intechstudio/grid-hardware/Packaging/PACKAGING-SLEEVE_Diecut.pdf

### Horizontal Grain

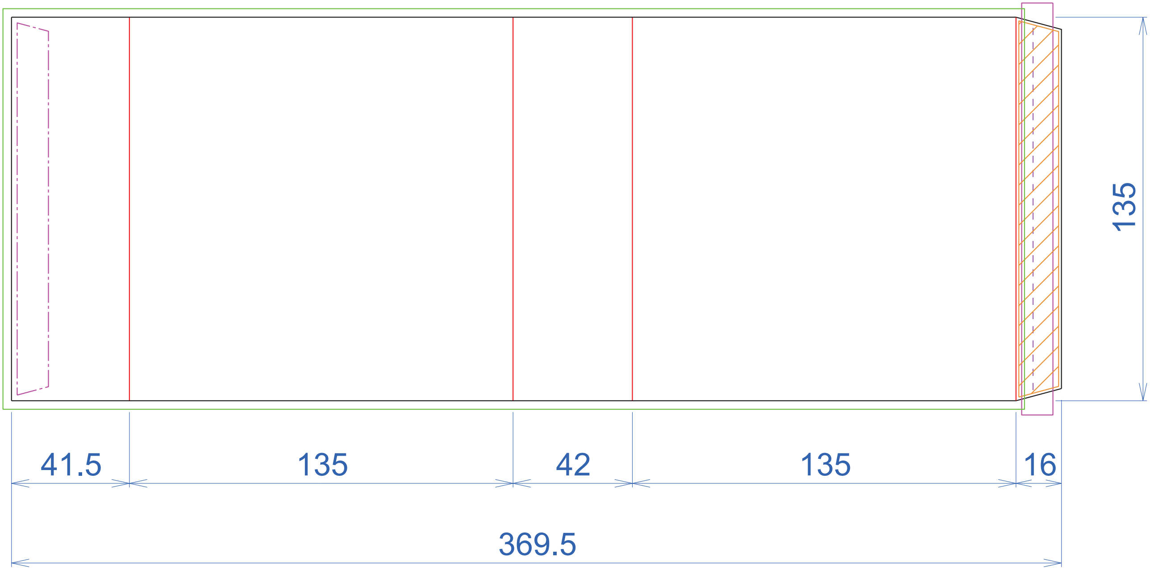
[picture p28: figure]
