intechstudio/grid-hardware/Electrical/failed to add usb.png

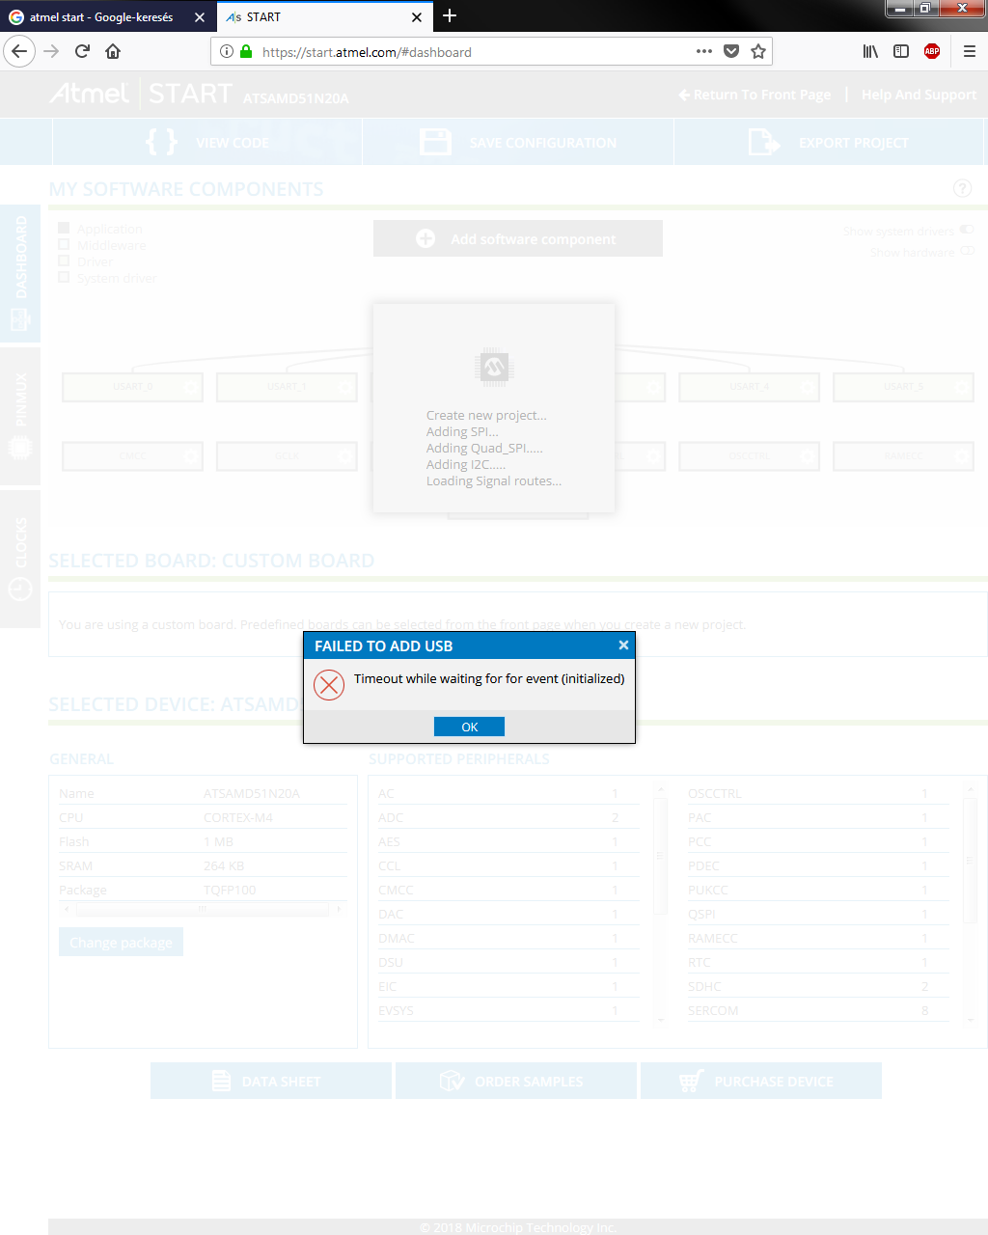
Electrical/failed to add usb.png
