intechstudio/grid-hardware/Electrical/Knowledge/4layer-stackup.jpg

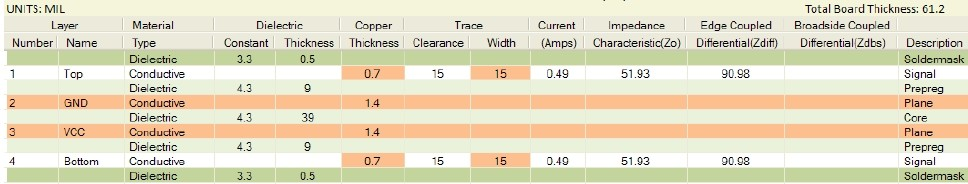
Electrical/Knowledge/4layer-stackup.jpg
