intechstudio/grid-hardware/Electrical/Knowledge/JLC_Stackup.PNG

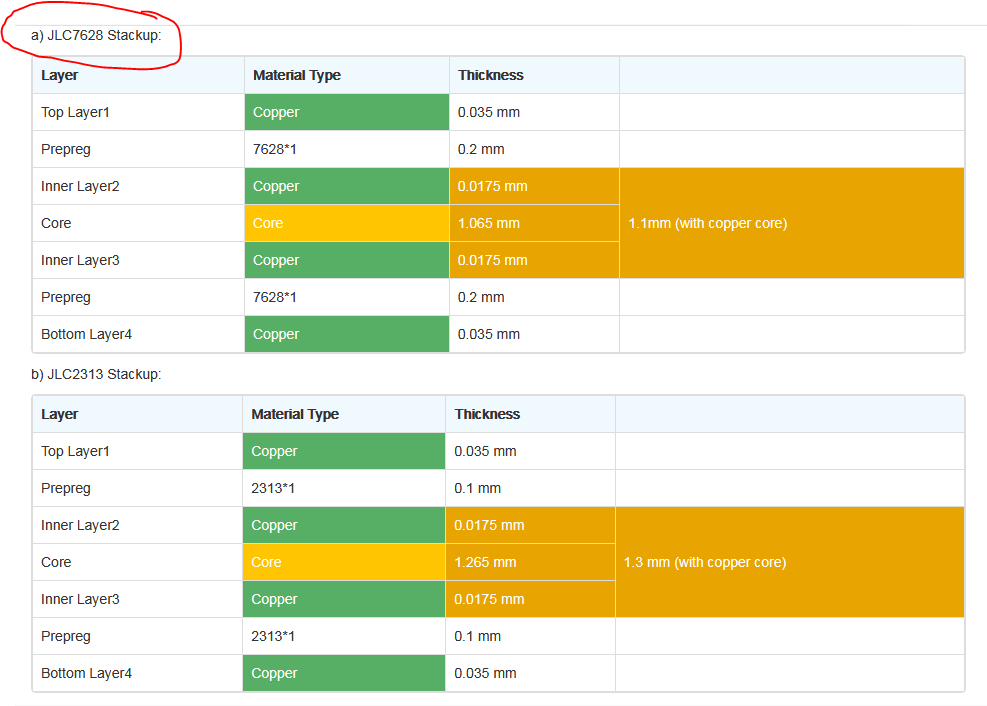
Electrical/Knowledge/JLC_Stackup.PNG
