intechstudio/grid-hardware/Electrical/Knowledge/New Stackup, JLC and WAY.PNG

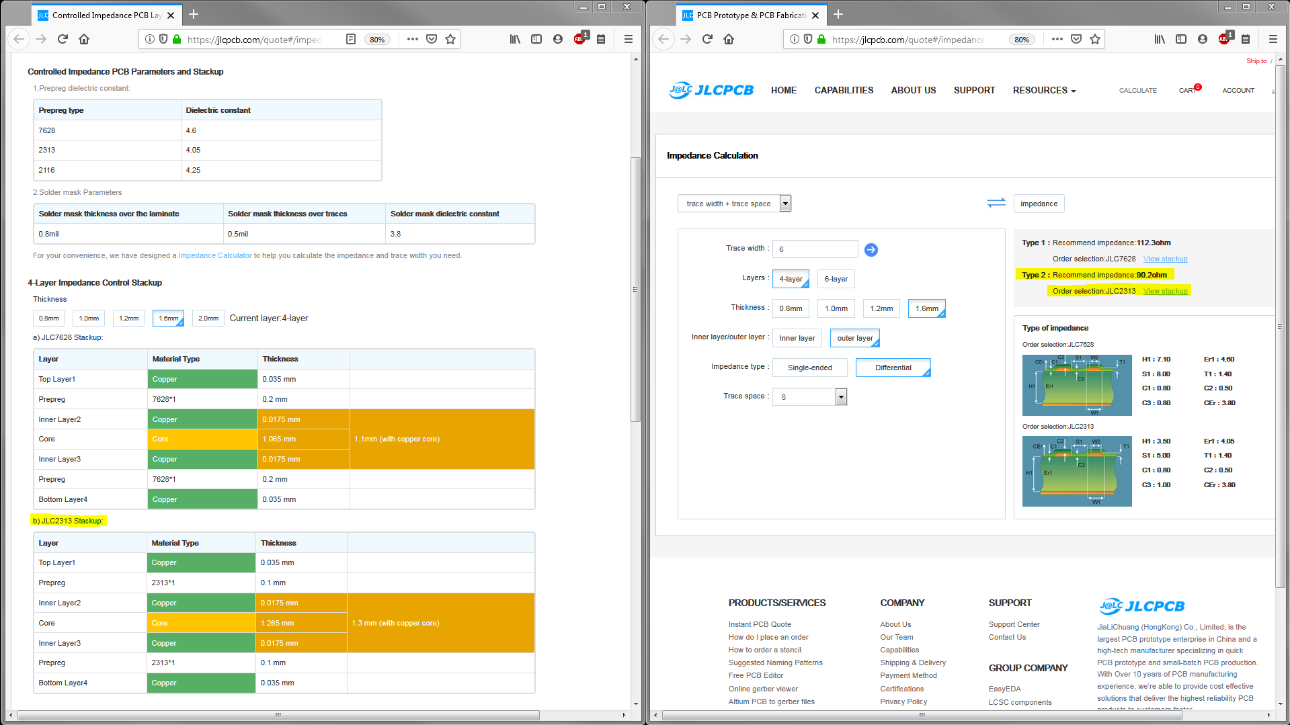
Electrical/Knowledge/New Stackup, JLC and WAY.PNG
