intechstudio/grid-hardware/Electrical/Knowledge/zdiff.png

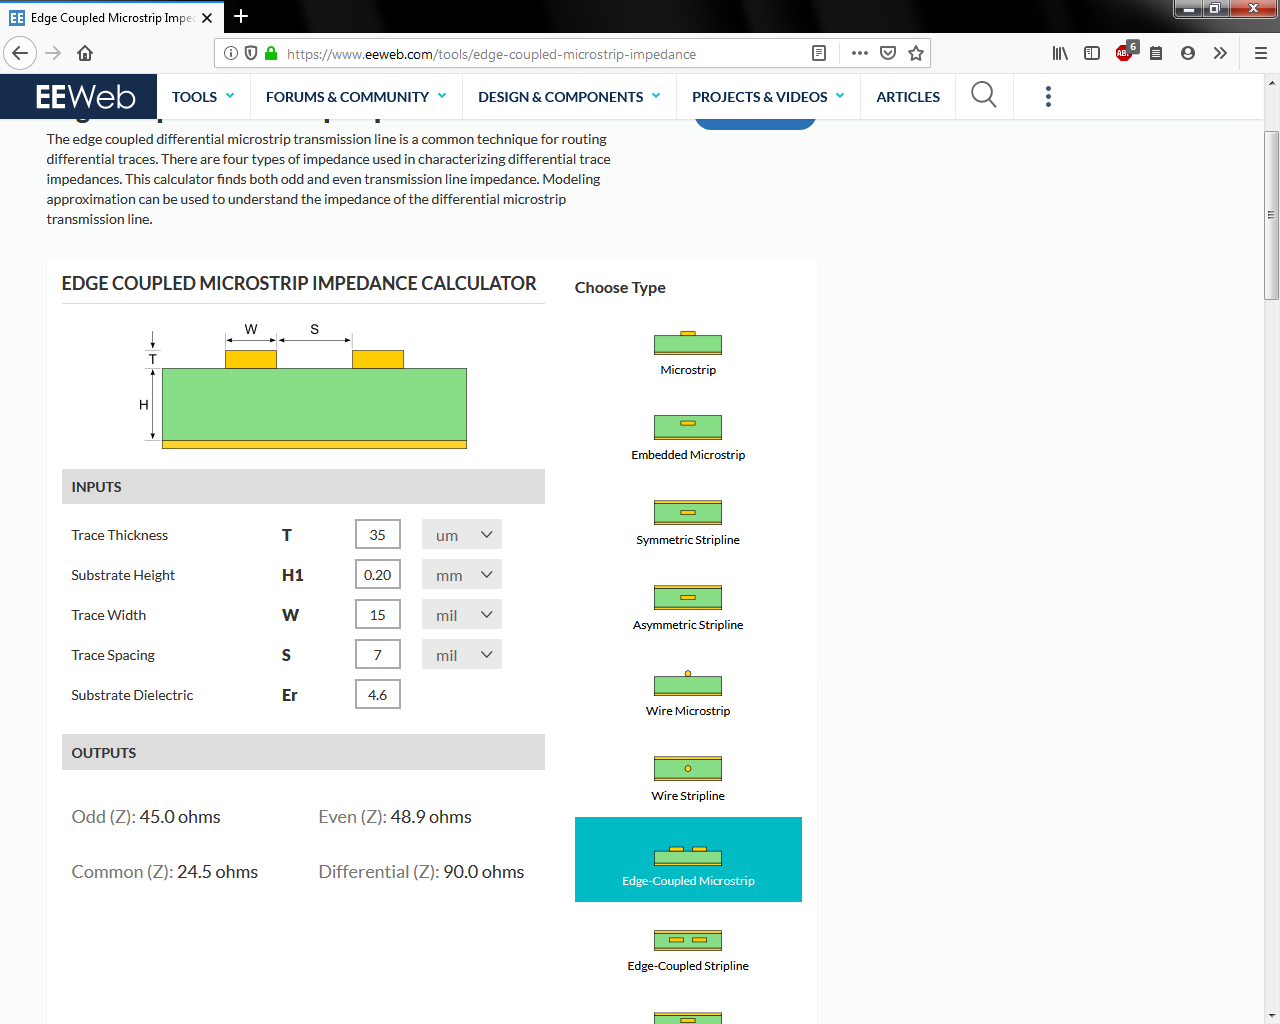
Electrical/Knowledge/zdiff.png
