intechstudio/grid-hardware/Electrical/rf_matching.png

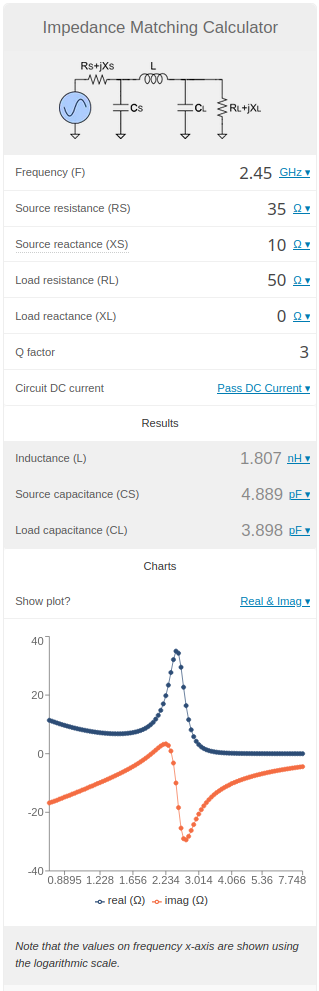
Electrical/rf_matching.png
