intechstudio/grid-hardware/Mechanical/Design/Pogo/Custom IS_POGO_Rev2_Latest/updated pogo.png

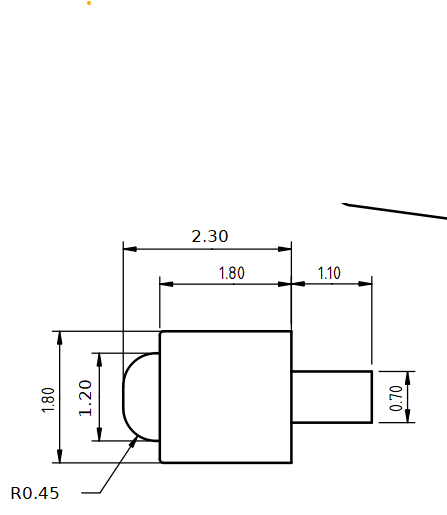
Mechanical/Design/Pogo/Custom IS_POGO_Rev2_Latest/updated pogo.png
