intechstudio/grid-hardware/Mechanical/Design/SMT-CONN-BATTERY/SMT-CONN-BATTERY_Photo.png

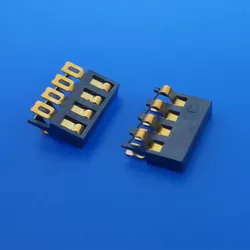
Mechanical/Design/SMT-CONN-BATTERY/SMT-CONN-BATTERY_Photo.png
