intechstudio/grid-hardware/Packaging/PACKAGING-SLEEVE-BU16.png

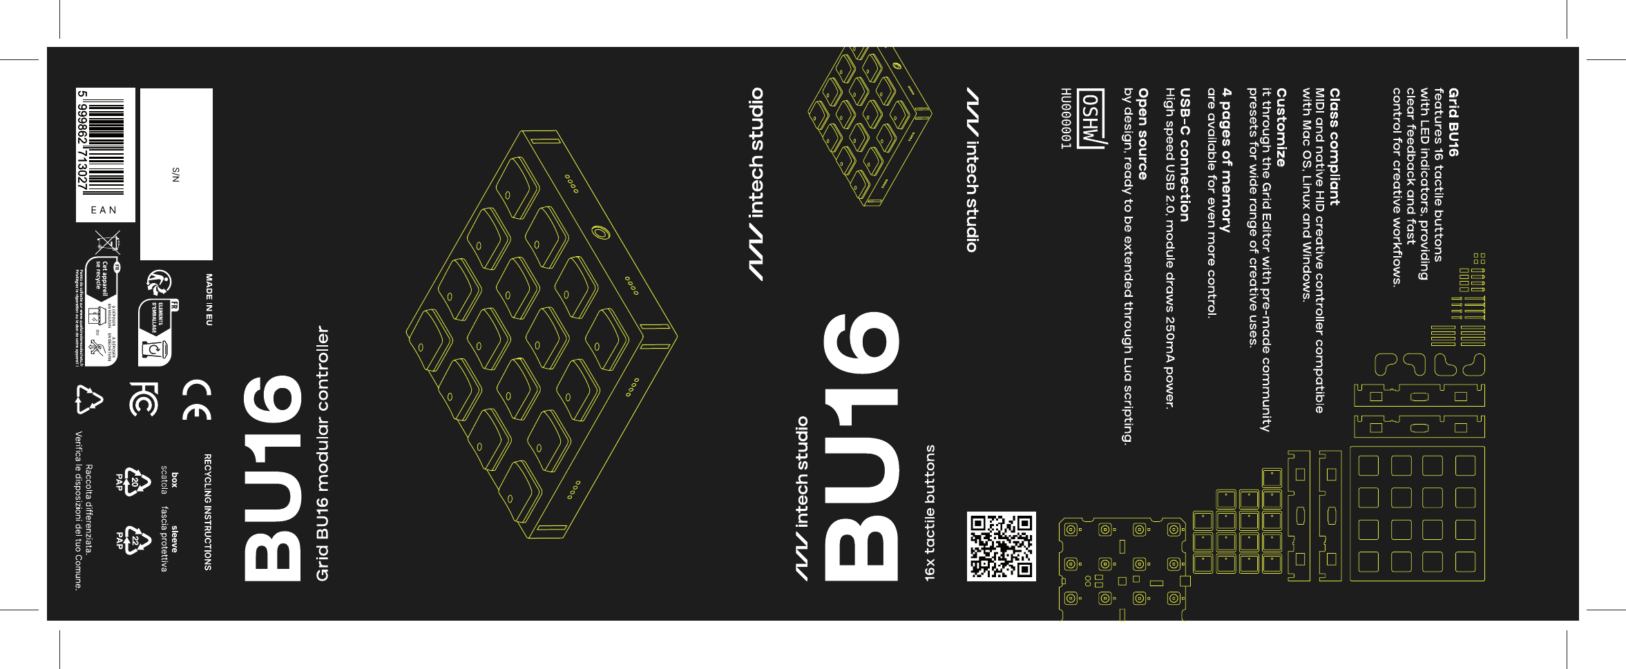
Packaging/PACKAGING-SLEEVE-BU16.png
