intechstudio/grid-hardware/Packaging/PACKAGING-SLEEVE-PBF4.png

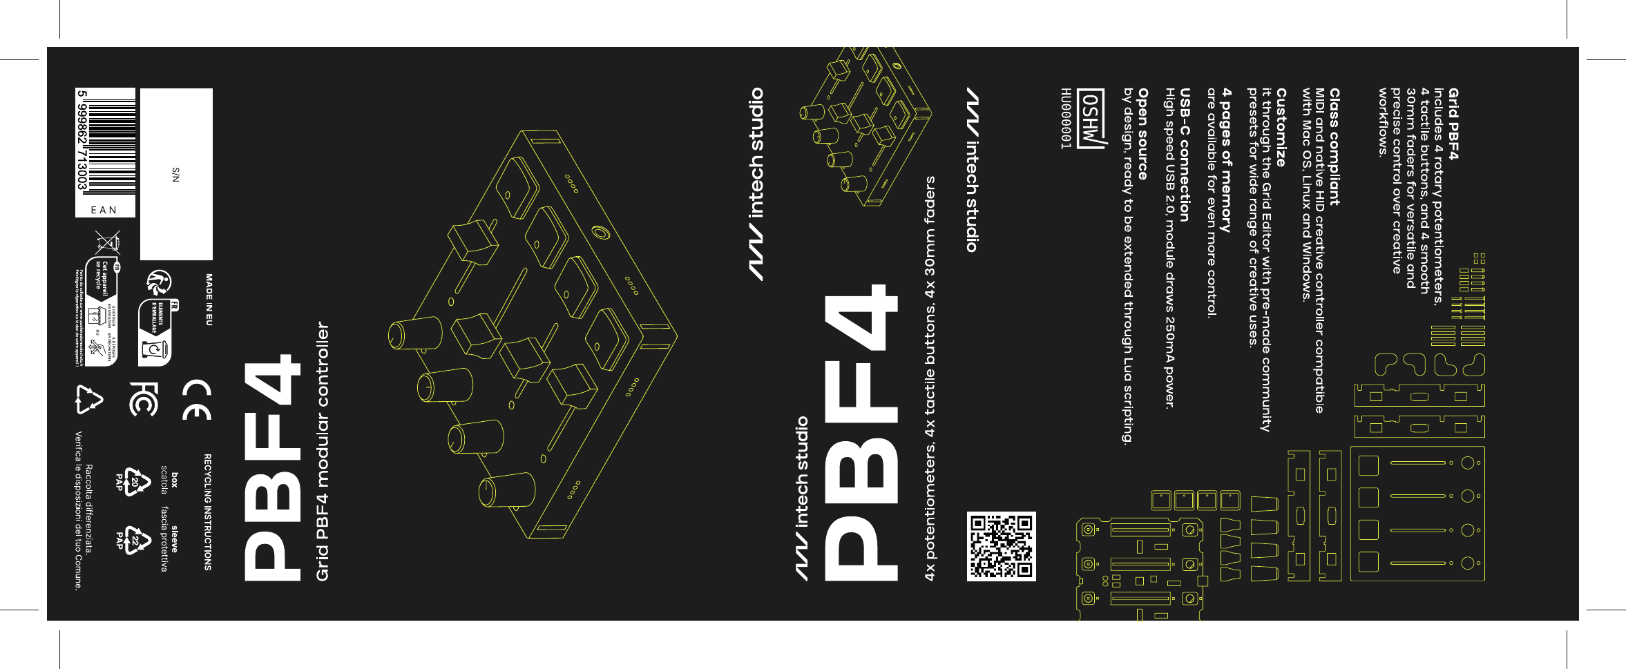
Packaging/PACKAGING-SLEEVE-PBF4.png
