intechstudio/grid-hardware/Packaging/PACKAGING-SLEEVE-PO16.png

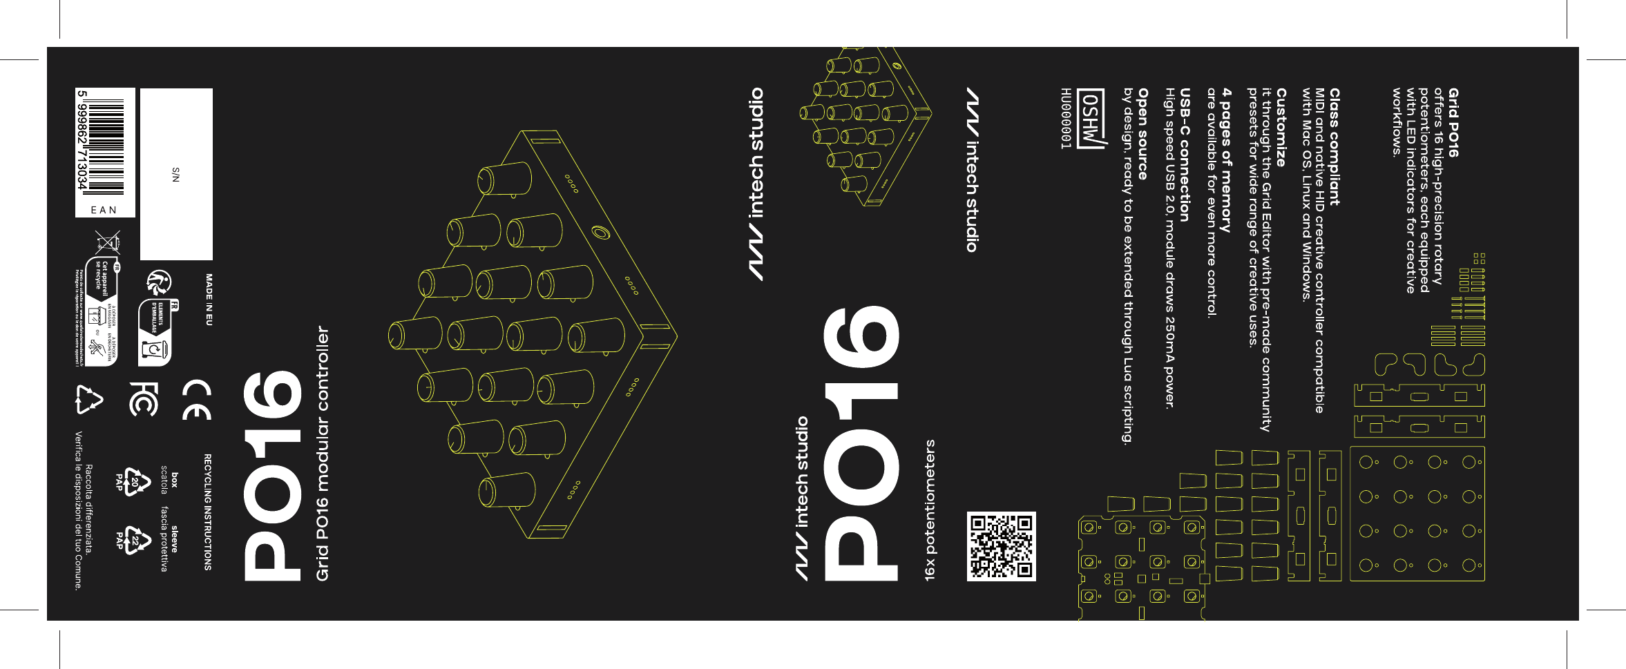
Packaging/PACKAGING-SLEEVE-PO16.png
