intechstudio/grid-hardware/Packaging/PACKAGING-SLEEVE-VSN1-L.png

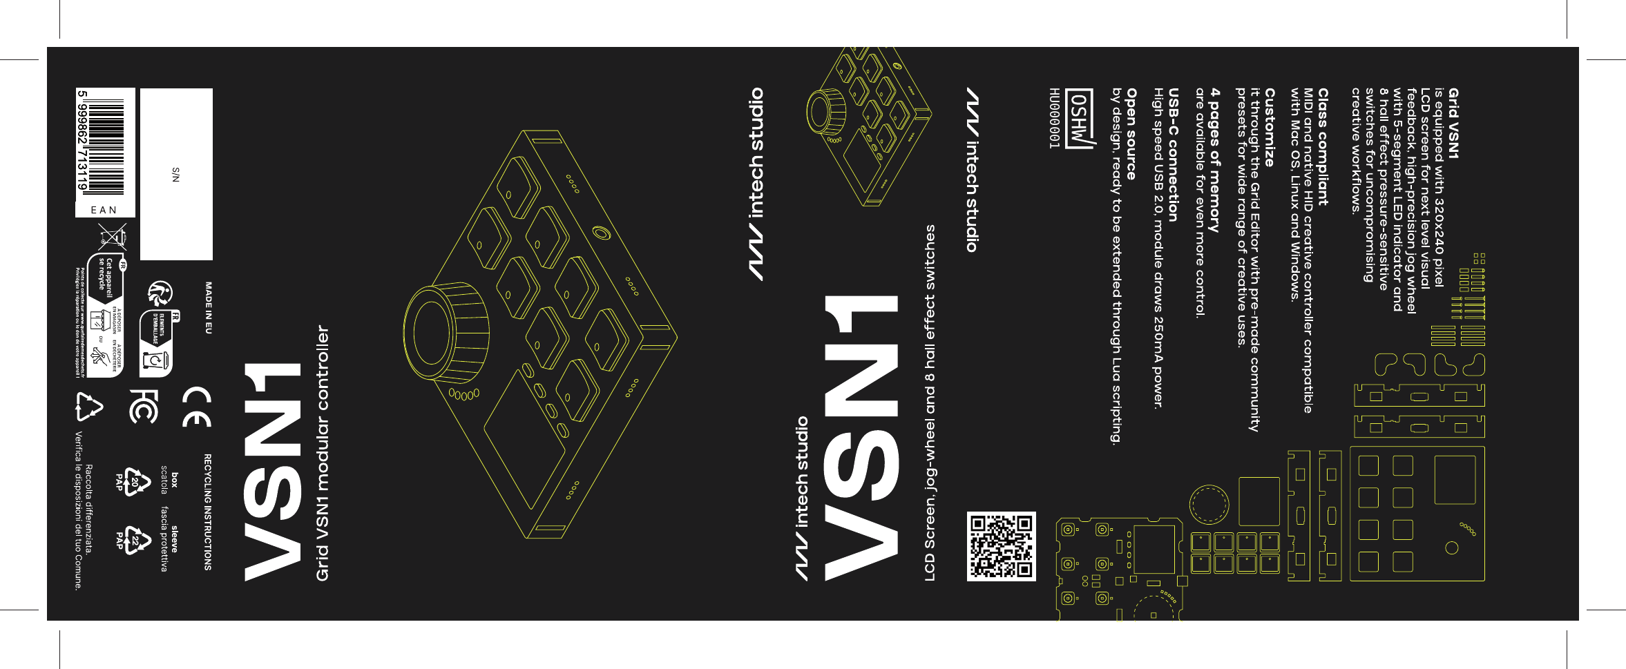
Packaging/PACKAGING-SLEEVE-VSN1-L.png
