intechstudio/grid-hardware/Packaging/PACKAGING-SLEEVE_Diecut.png

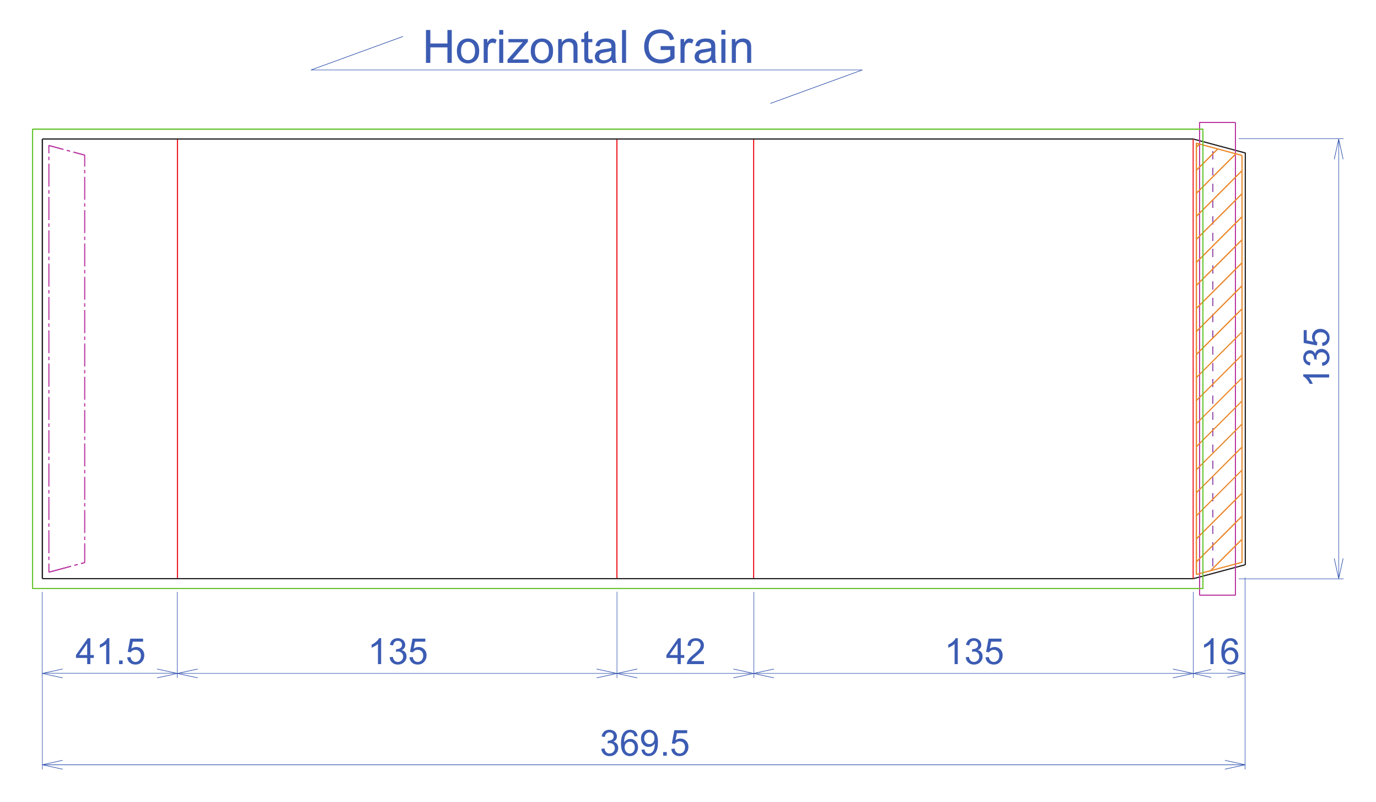
Packaging/PACKAGING-SLEEVE_Diecut.png
