intechstudio/grid-hardware/Packaging/PACKAGING-USB-CABLE.png

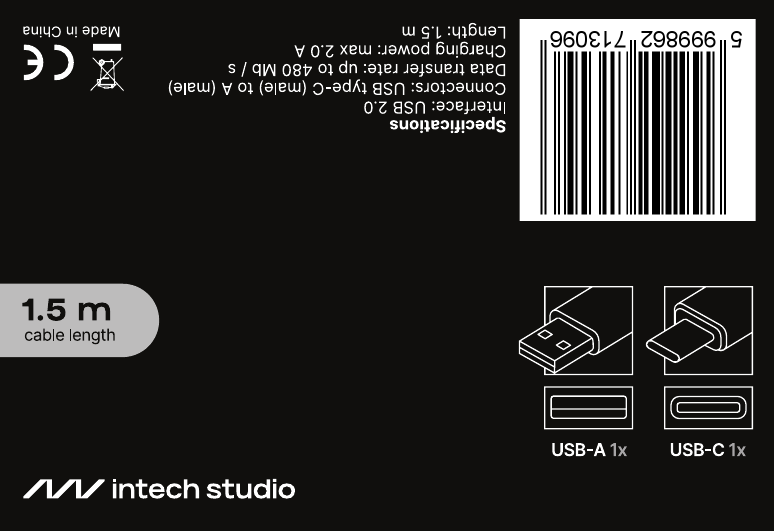
Packaging/PACKAGING-USB-CABLE.png
