intechstudio/grid-hardware/Electrical/Bill Of Materials/Photos/motherboard.jpg

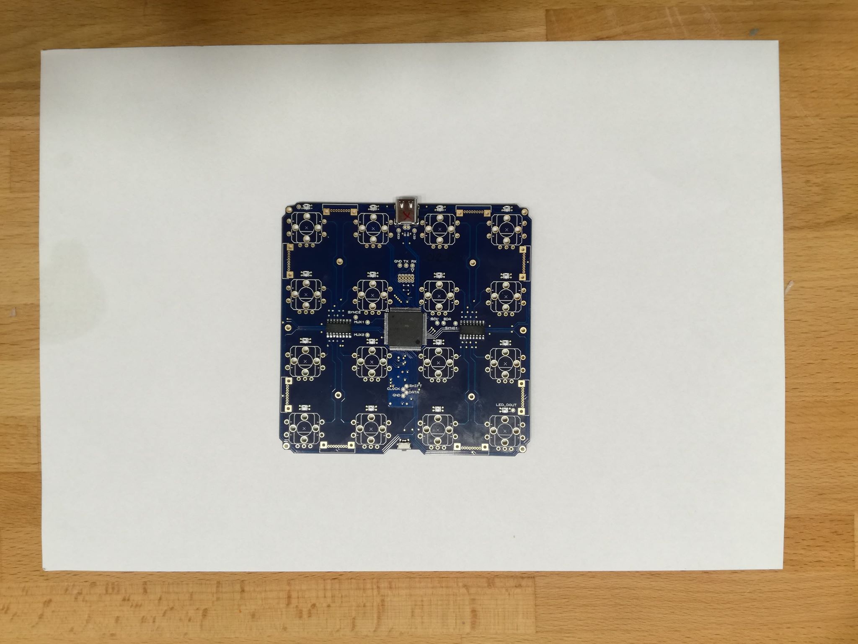
Electrical/Bill Of Materials/Photos/motherboard.jpg
