intechstudio/grid-hardware/Electrical/Bill Of Materials/Photos/product.jpg

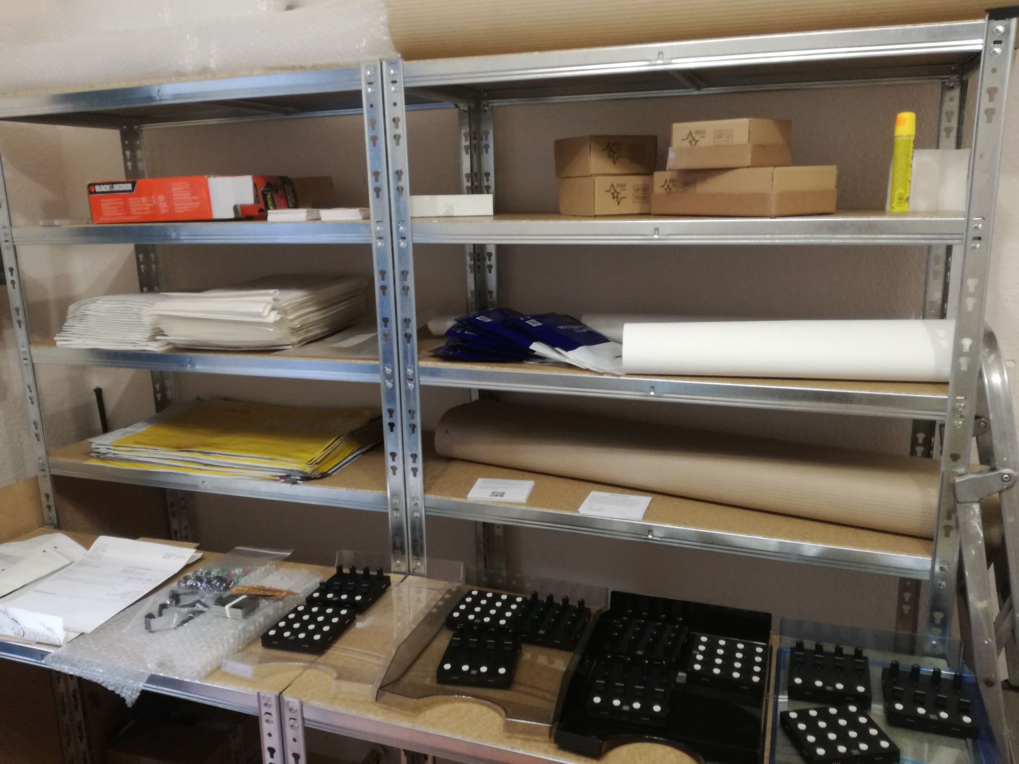
Electrical/Bill Of Materials/Photos/product.jpg
