intechstudio/grid-hardware/Manufacturing/Assembly/pot_cap_alignment_jig.FCStd

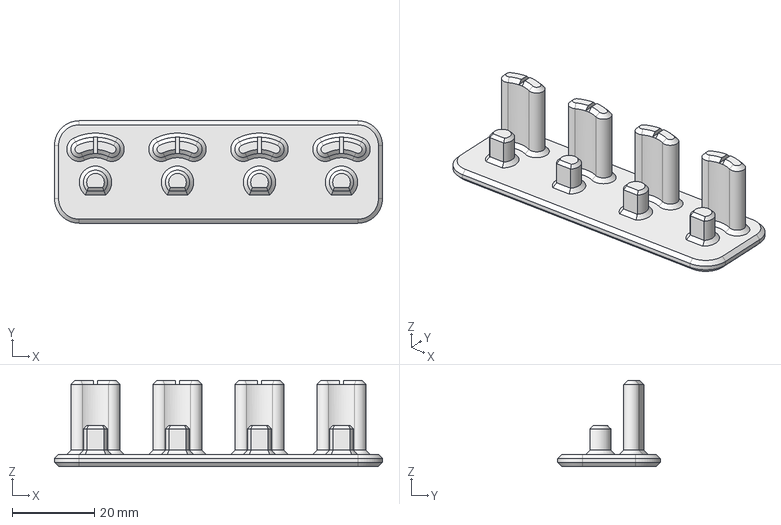
[picture p64: CAD file, 2020-11-19]
Manufacturing/Assembly/pot_cap_alignment_jig.FCStd
80.0 x 25.0 x 21.0 mm
