intechstudio/grid-hardware/Manufacturing/CarryCase/foam_insert.FCStd

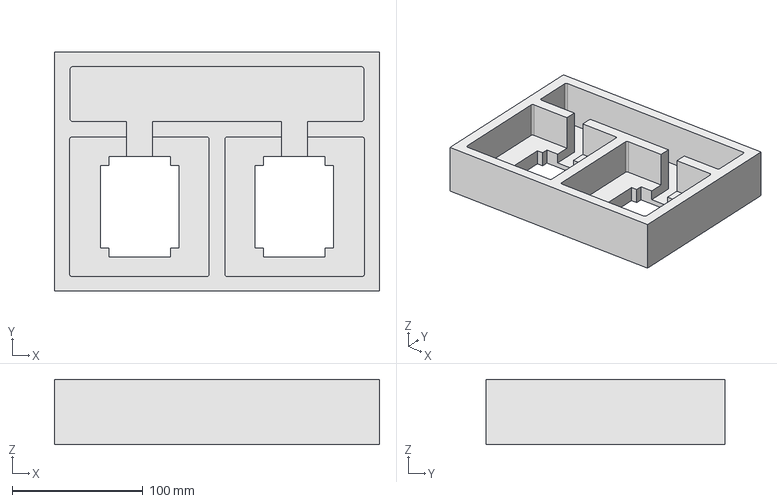
[picture p65: CAD file, 2023-02-24]
Manufacturing/CarryCase/foam_insert.FCStd
249.0 x 183.0 x 50.0 mm
