intechstudio/grid-hardware/Manufacturing/CNC/Electronics/cnc_endstop_mount_2.stl

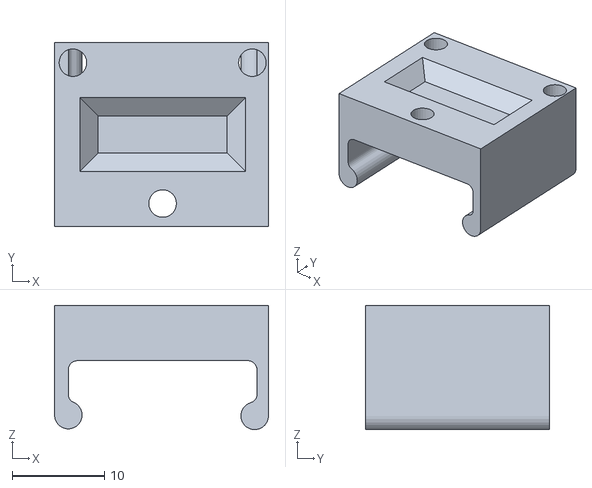
[picture p66: CAD file, 2021-02-25]
Manufacturing/CNC/Electronics/cnc_endstop_mount_2.stl
23.2 x 20.0 x 13.5
