intechstudio/grid-hardware/Manufacturing/CNC/vacuum_hole_fitting.FCStd

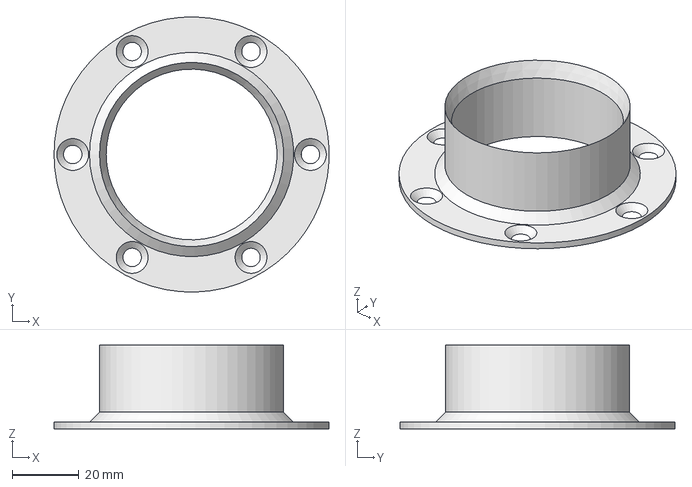
[picture p67: CAD file, 2021-04-12]
Manufacturing/CNC/vacuum_hole_fitting.FCStd
82.1 x 82.2 x 25.0 mm
