intechstudio/grid-hardware/Manufacturing/CNC_tristep/grid_cnc6.FCStd

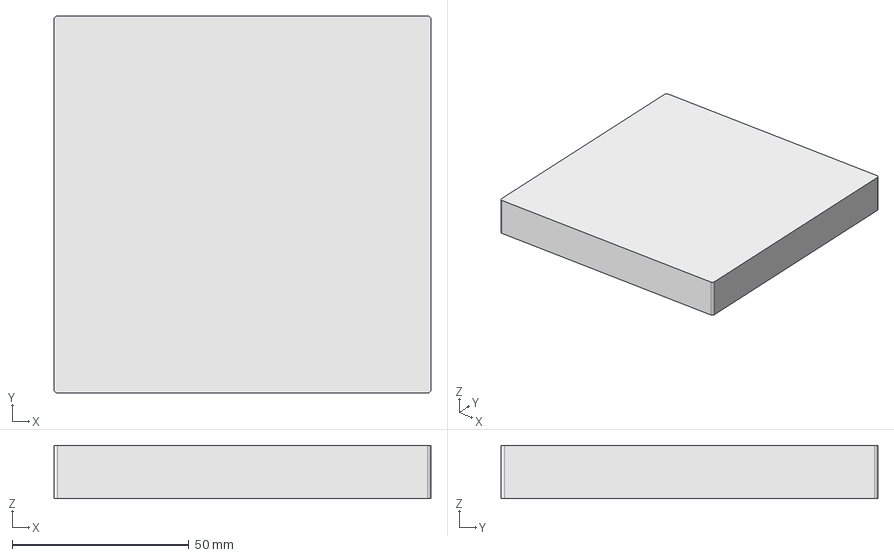
[picture p68: CAD file, 2023-06-28]
Manufacturing/CNC_tristep/grid_cnc6.FCStd
106.6 x 106.6 x 15.0 mm
