intechstudio/grid-hardware/Manufacturing/flatness_QC_jig/qc_jig_button_box.FCStd

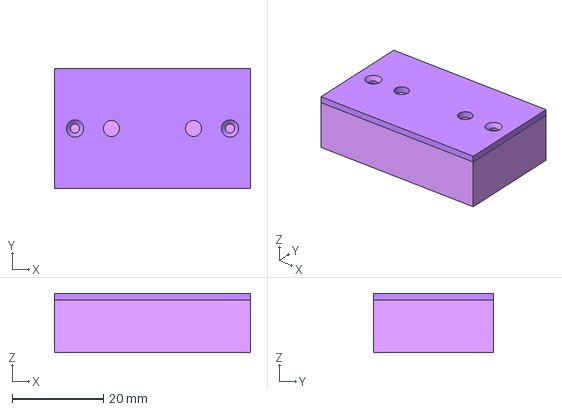
[picture p69: CAD file, 2024-06-20]
Manufacturing/flatness_QC_jig/qc_jig_button_box.FCStd
43.0 x 26.3 x 13.0 mm
