intechstudio/grid-hardware/Manufacturing/Fumefood/accessories/motormount.FCStd

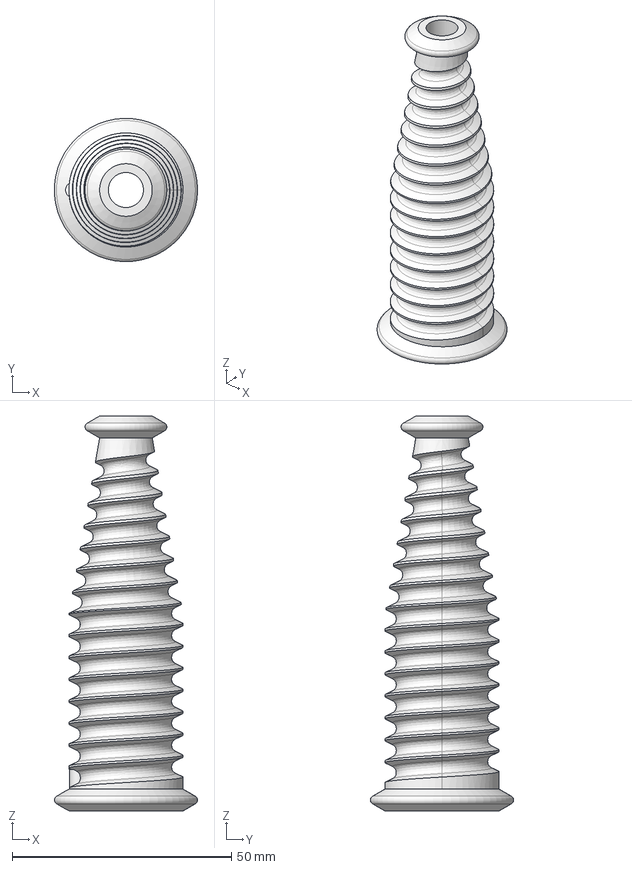
[picture p70: CAD file, 2021-10-26]
Manufacturing/Fumefood/accessories/motormount.FCStd
32.6 x 32.6 x 90.0 mm
