intechstudio/grid-hardware/Manufacturing/Fumefood/compliant_wheel.FCStd

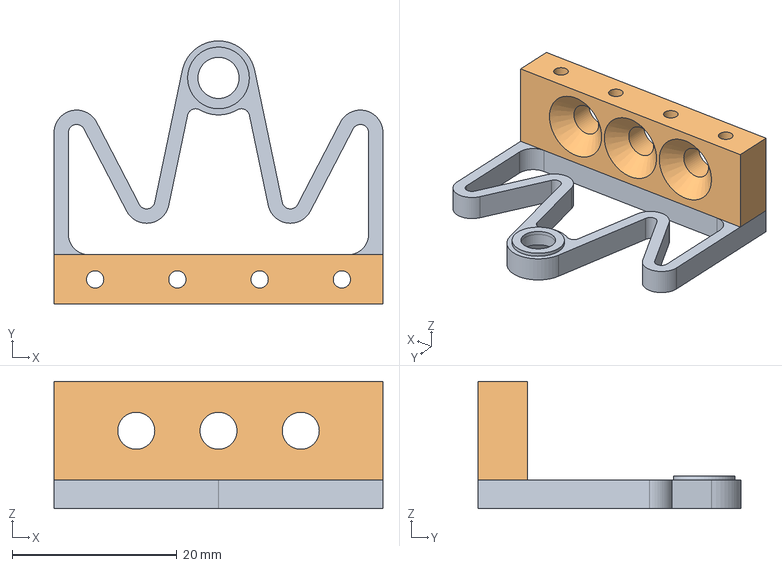
[picture p71: CAD file, 2021-03-19]
Manufacturing/Fumefood/compliant_wheel.FCStd
40.0 x 32.0 x 15.5 mm
