intechstudio/grid-hardware/Manufacturing/Fumefood/window_controls/2020_2x22mm_left.FCStd

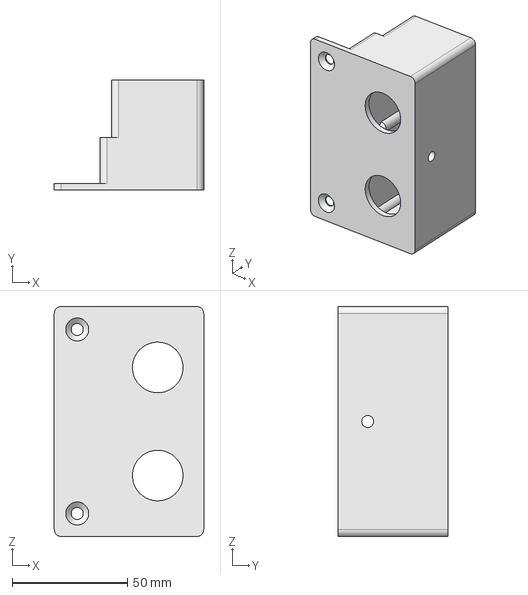
[picture p72: CAD file, 2021-09-23]
Manufacturing/Fumefood/window_controls/2020_2x22mm_left.FCStd
65.0 x 48.0 x 100.0 mm
