intechstudio/grid-hardware/Manufacturing/iroda/asztallab_szorito.FCStd

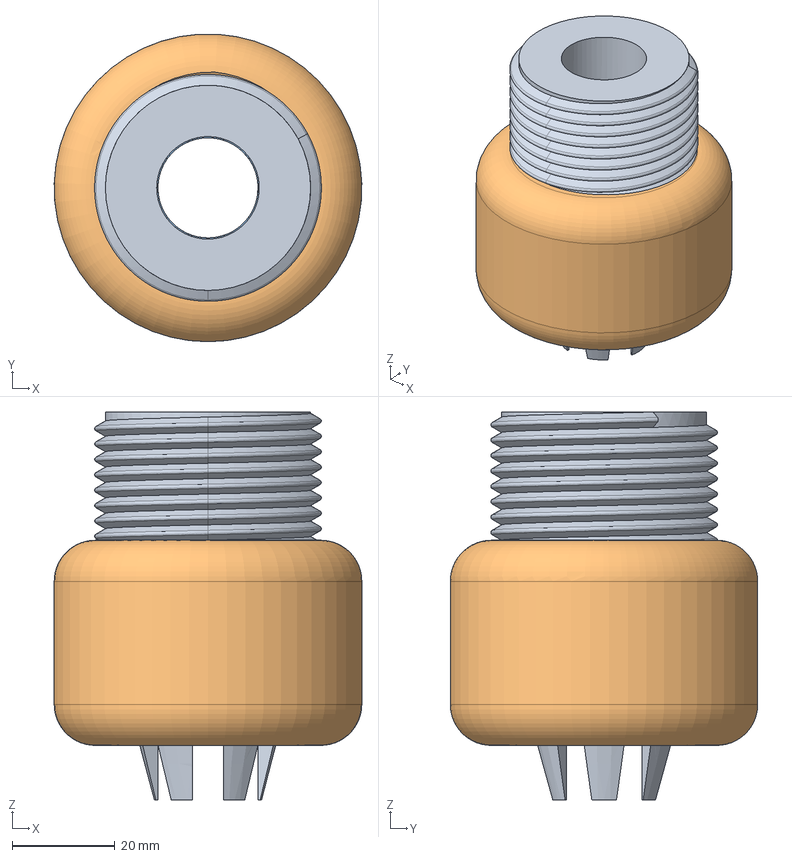
[picture p73: CAD file, 2024-03-14]
Manufacturing/iroda/asztallab_szorito.FCStd
60.0 x 59.9 x 75.6 mm
felso resz
szorito
hezagolo
