intechstudio/grid-hardware/Manufacturing/Laser/plotter_bearing_holder.FCStd

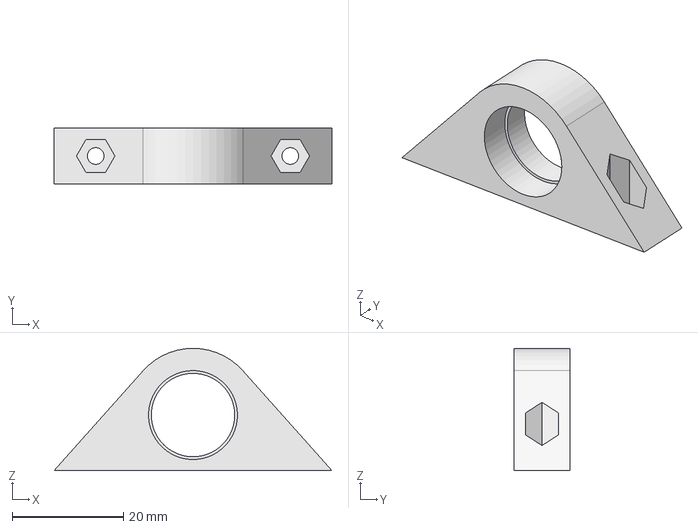
[picture p74: CAD file, 2021-02-25]
Manufacturing/Laser/plotter_bearing_holder.FCStd
50.0 x 10.0 x 22.0 mm
