intechstudio/grid-hardware/Manufacturing/Packaging/cardboard_insert.FCStd

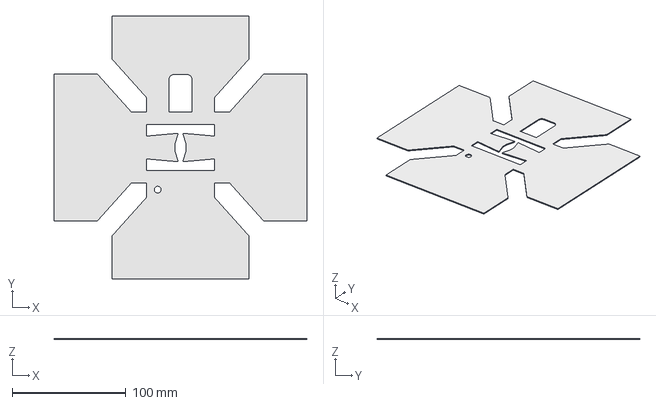
[picture p75: CAD file, 2023-03-27]
Manufacturing/Packaging/cardboard_insert.FCStd
222.0 x 231.0 x 1.00 mm
