intechstudio/grid-hardware/Manufacturing/Packaging/quote2/carboardinsert2.dxf

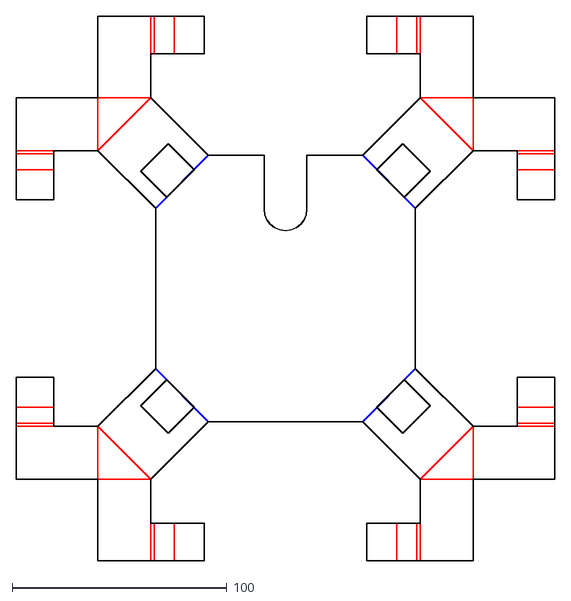
[picture p76: CAD file, 2020-11-30]
Manufacturing/Packaging/quote2/carboardinsert2.dxf
250.7 x 253.7
