intechstudio/grid-hardware/Manufacturing/Packaging/quote3/insert3.dxf

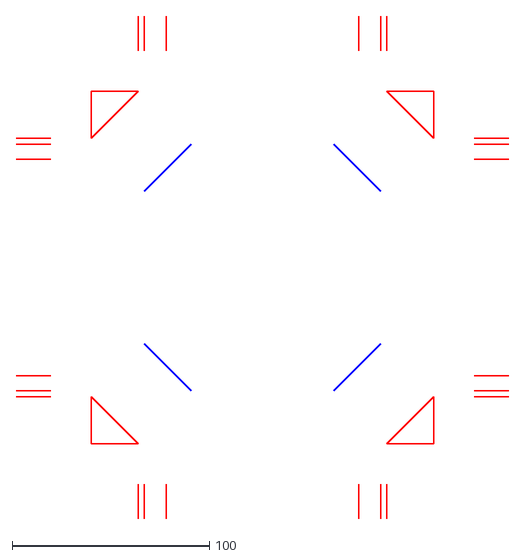
[picture p77: CAD file, 2020-12-07]
Manufacturing/Packaging/quote3/insert3.dxf
249.7 x 254.7
