intechstudio/grid-hardware/Manufacturing/Photobooth/gridstand_20deg.FCStd

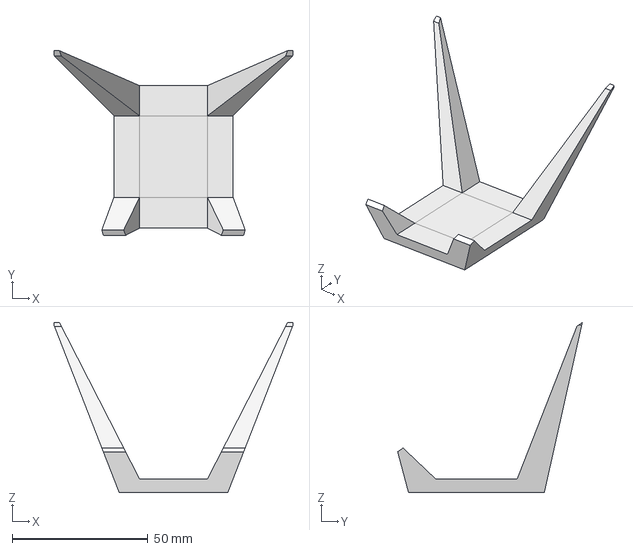
[picture p78: CAD file, 2021-02-25]
Manufacturing/Photobooth/gridstand_20deg.FCStd
88.0 x 68.0 x 62.6 mm
