intechstudio/grid-hardware/Manufacturing/Potbushing/pot_bushing.step

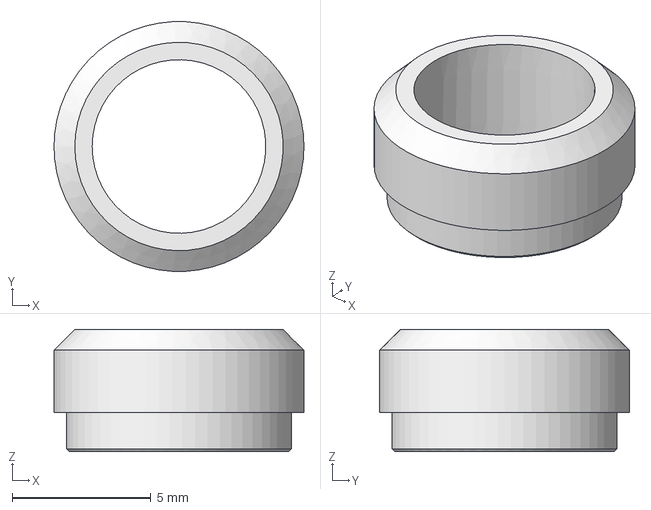
[picture p79: CAD file, 2021-09-28]
Manufacturing/Potbushing/pot_bushing.step
9.00 x 8.99 x 4.40 mm
