intechstudio/grid-hardware/Manufacturing/Potcap-insert/universal_insert.FCStd

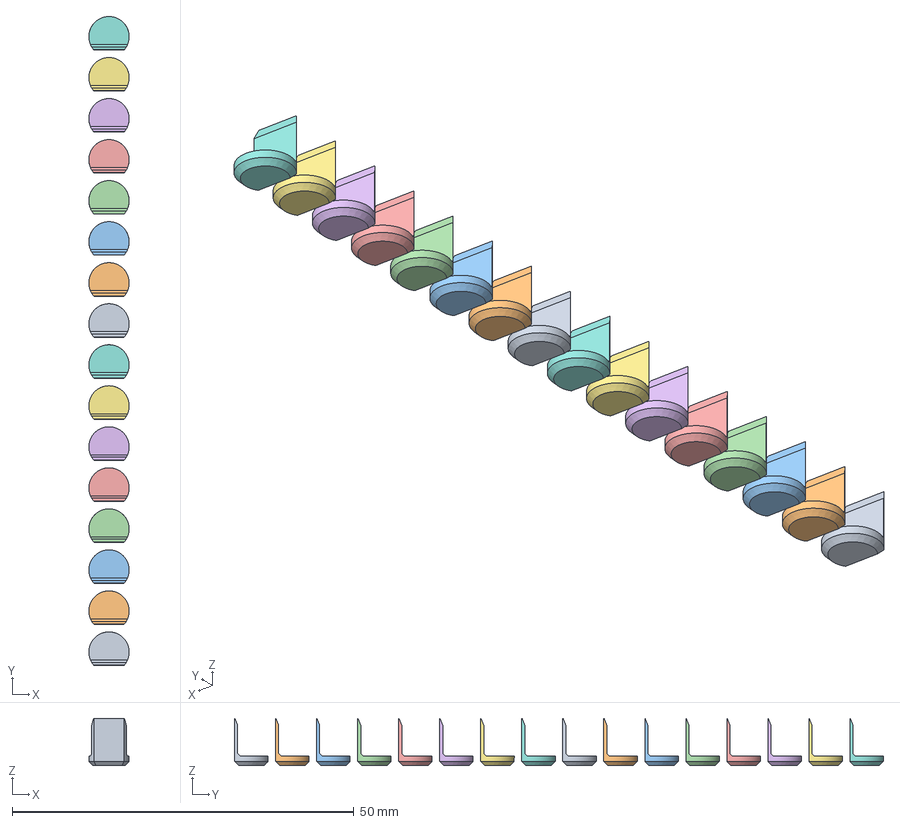
[picture p80: CAD file, 2024-07-18]
Manufacturing/Potcap-insert/universal_insert.FCStd
5.90 x 94.9 x 6.90 mm
Potentiometer001
