intechstudio/grid-hardware/Manufacturing/QC_jigs/pogo_pin_test_jig.FCStd

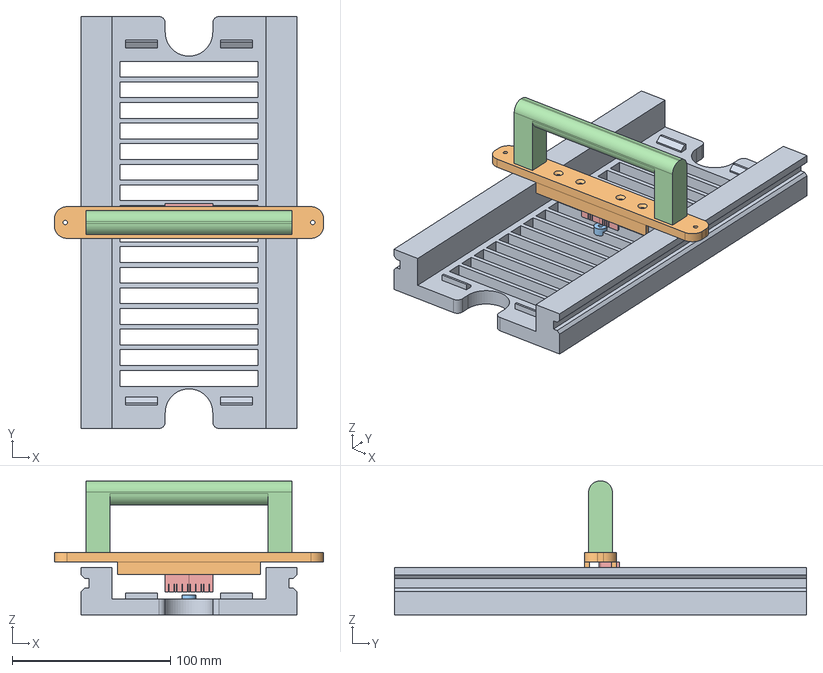
[picture p81: CAD file, 2024-03-14]
Manufacturing/QC_jigs/pogo_pin_test_jig.FCStd
170.0 x 260.0 x 84.5 mm
Jig
Handle sheet
Spacer
Handle
Comb
