intechstudio/grid-hardware/Mechanical/Assembly/Components/mapmode8.step

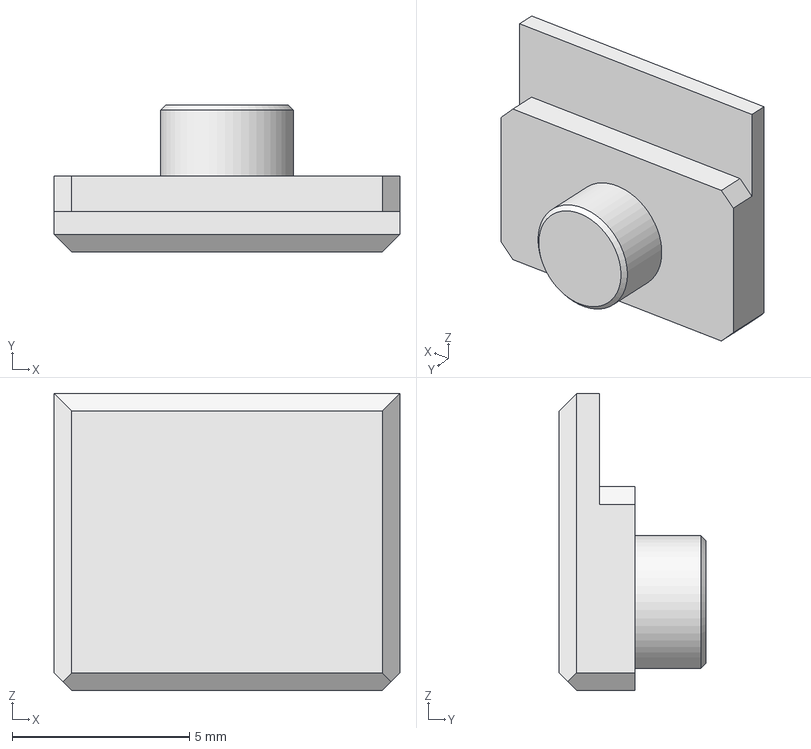
[picture p82: CAD file, 2020-07-10]
Mechanical/Assembly/Components/mapmode8.step
9.75 x 4.15 x 8.38 mm
