intechstudio/grid-hardware/Mechanical/Assembly/Frontpanels/FRONTPANEL-BU16-1.FCStd

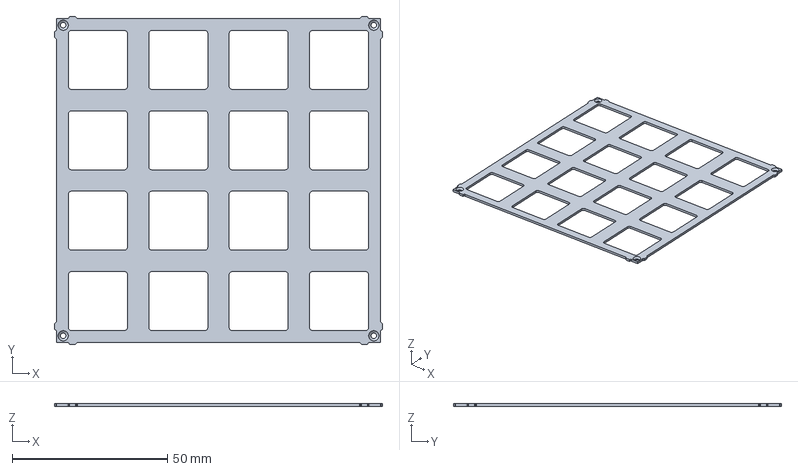
[picture p83: CAD file, 2025-09-30]
Mechanical/Assembly/Frontpanels/FRONTPANEL-BU16-1.FCStd
105.6 x 105.6 x 1.00 mm
