intechstudio/grid-hardware/Mechanical/Assembly/PCBAs/PCBA-VSNX-LCDMOUNT-LEFT.FCStd

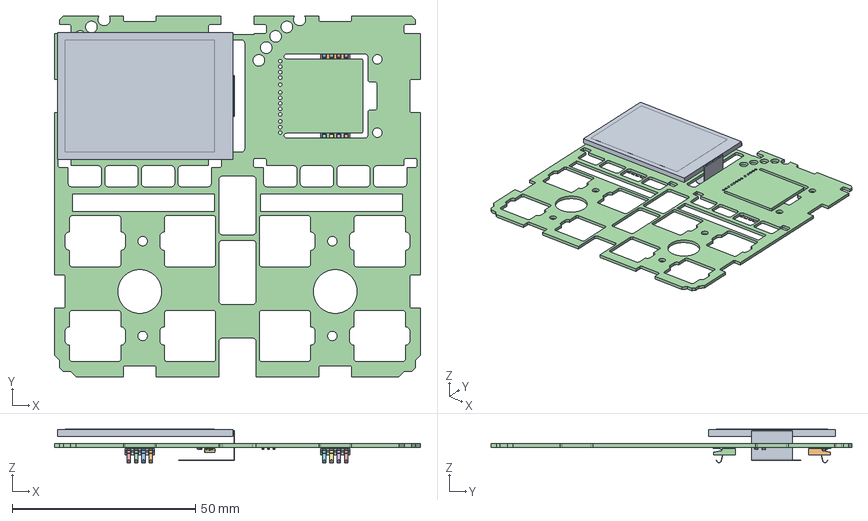
[picture p84: CAD file, 2025-09-30]
Mechanical/Assembly/PCBAs/PCBA-VSNX-LCDMOUNT-LEFT.FCStd
100.0 x 98.5 x 9.18 mm
PCBA-TEK1-DISPLAY
R_0402_1005Metric
R_0402_1005Metric001
Spring_original
Spring2
Spring3
Sprring4
Spring_original001
Spring004
Spring005
Sprring005
R_0402_1005Metric002
R_0402_1005Metric003
C_0402_1005Metric
C_0402_1005Metric001
Spring_original002
Spring006
Spring007
Sprring006
SOT-23
Spring_original003
Spring008
Spring009
Sprring007
C_0402_1005Metric002
R_0402_1005Metric004
C_0402_1005Metric003
R_0402_1005Metric005
R_0402_1005Metric006
R_0402_1005Metric007
R_0402_1005Metric008
kibot_zjonc10v_PCB
