intechstudio/grid-hardware/Mechanical/Design/Frontpanel/grid_frontpanel_new.FCStd

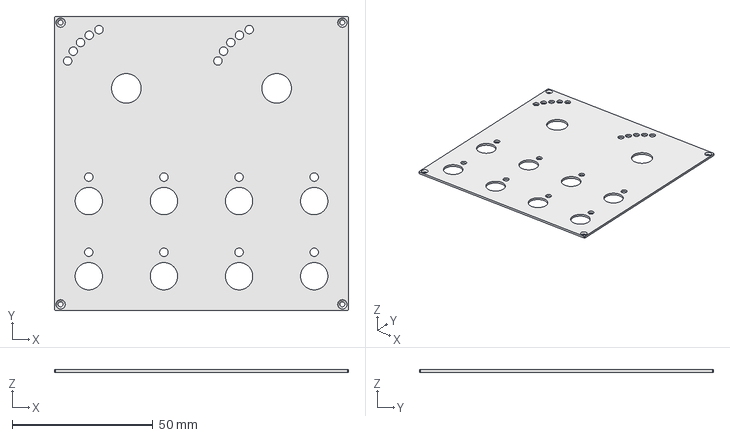
[picture p85: CAD file, 2023-08-14]
Mechanical/Design/Frontpanel/grid_frontpanel_new.FCStd
104.3 x 104.4 x 1.00 mm
