intechstudio/grid-hardware/Mechanical/Design/INSERT-FADER/INSERT-FADER.FCStd

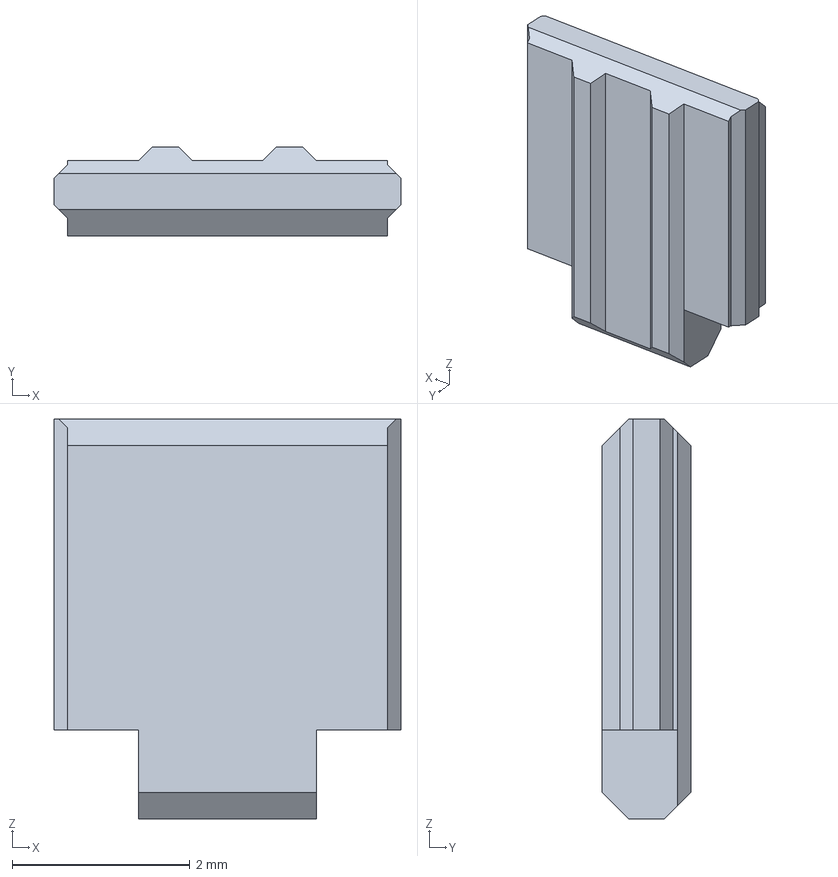
[picture p86: CAD file, 2025-09-02]
Mechanical/Design/INSERT-FADER/INSERT-FADER.FCStd
3.90 x 1.00 x 4.50 mm
