intechstudio/grid-hardware/Mechanical/Design/INSERT-M1.6x2.5x3/INSERT-M1.6x2.5x3.FCStd

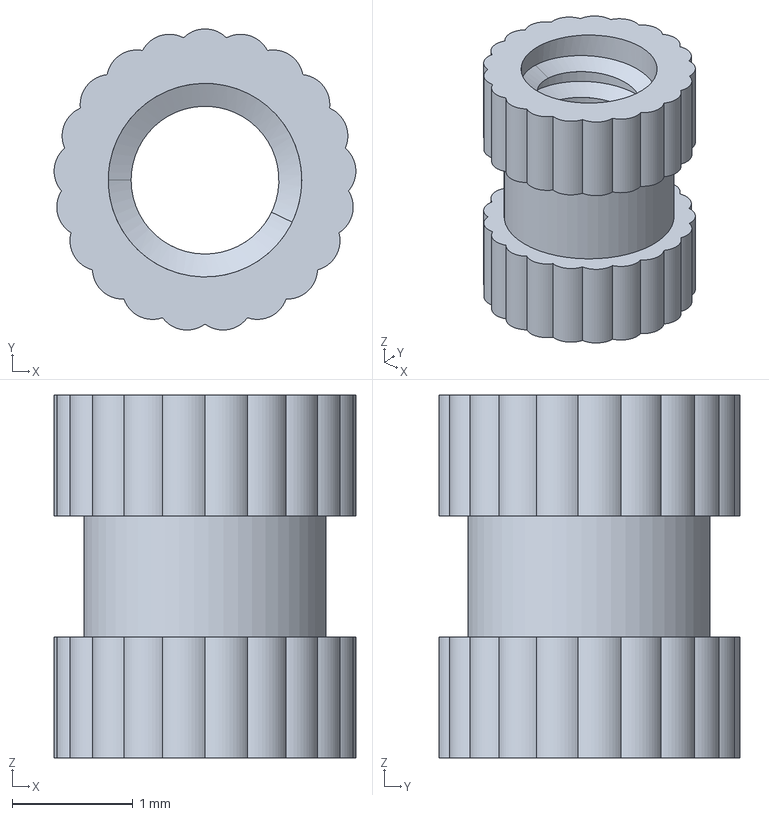
[picture p87: CAD file, 2025-09-19]
Mechanical/Design/INSERT-M1.6x2.5x3/INSERT-M1.6x2.5x3.FCStd
2.49 x 2.49 x 3.00 mm
