intechstudio/grid-hardware/Mechanical/Design/INSERT-M1.6x2.5x4/INSERT-M1.6x2.5x4.FCStd

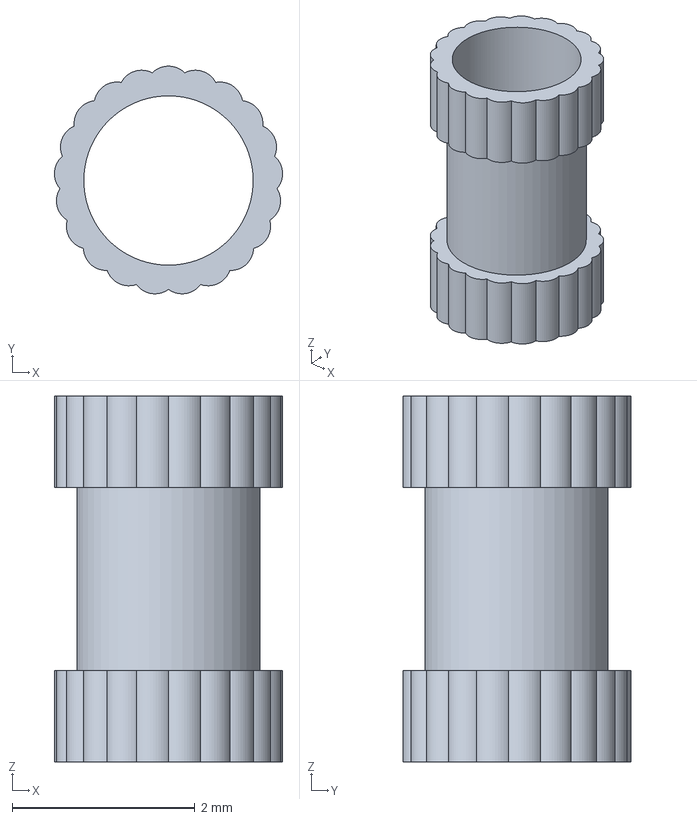
[picture p88: CAD file, 2025-09-19]
Mechanical/Design/INSERT-M1.6x2.5x4/INSERT-M1.6x2.5x4.FCStd
2.49 x 2.49 x 4.00 mm
