intechstudio/grid-hardware/Mechanical/Design/KNOB-TEK2/KNOB-TEK2.FCStd

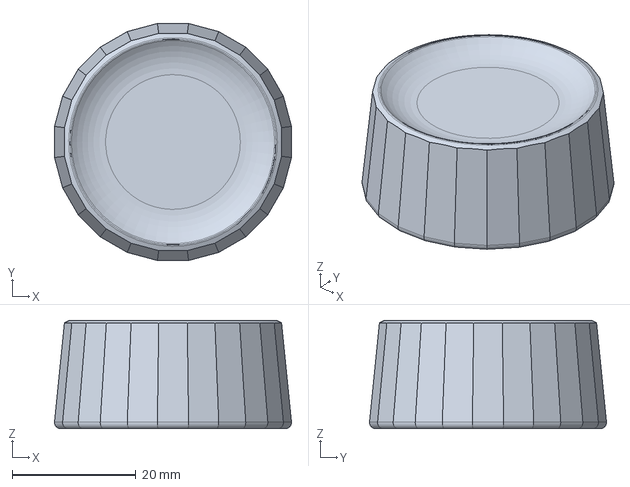
[picture p89: CAD file, 2025-09-19]
Mechanical/Design/KNOB-TEK2/KNOB-TEK2.FCStd
38.3 x 38.3 x 17.5 mm
