intechstudio/grid-hardware/Mechanical/Design/MAGNET-D3x14/MAGNET-D3x14.FCStd

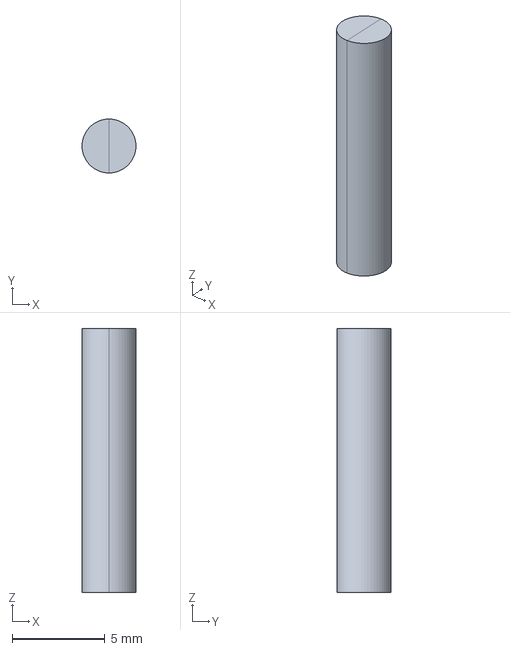
[picture p90: CAD file, 2025-09-19]
Mechanical/Design/MAGNET-D3x14/MAGNET-D3x14.FCStd
2.90 x 2.90 x 14.2 mm
