intechstudio/grid-hardware/Mechanical/Design/MAGNET-SQ3/MAGNET-SQ3.FCStd

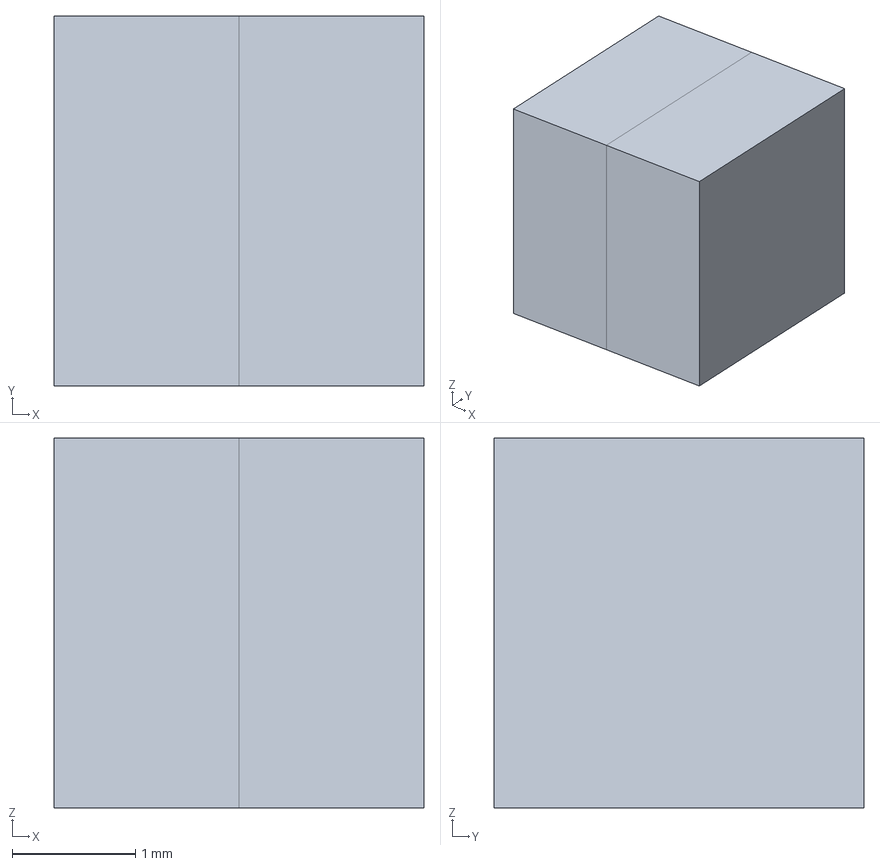
[picture p91: CAD file, 2025-09-30]
Mechanical/Design/MAGNET-SQ3/MAGNET-SQ3.FCStd
3.00 x 3.00 x 3.00 mm
