intechstudio/grid-hardware/Mechanical/Design/PLASTIC-BUSHING-POT-TEK2/PLASTIC-BUSHING-POT-TEK2.FCStd

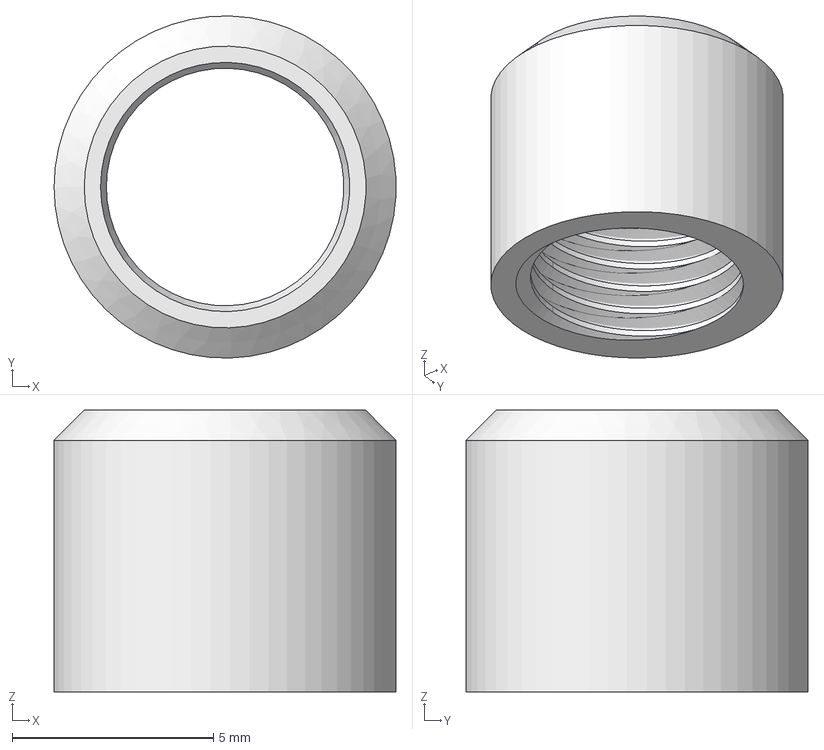
[picture p92: CAD file, 2024-03-12]
Mechanical/Design/PLASTIC-BUSHING-POT-TEK2/PLASTIC-BUSHING-POT-TEK2.FCStd
8.49 x 8.50 x 7.00 mm
