intechstudio/grid-hardware/Mechanical/Design/PLASTIC-CAP-BUTTON/PLASTIC-CAP-BUTTON.FCStd

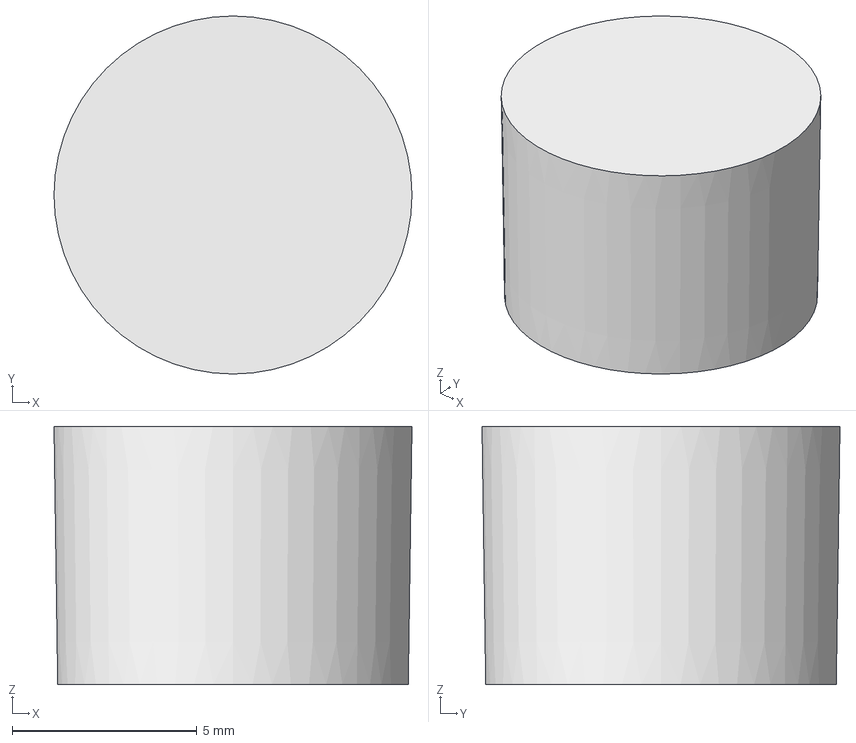
[picture p93: CAD file, 2023-12-20]
Mechanical/Design/PLASTIC-CAP-BUTTON/PLASTIC-CAP-BUTTON.FCStd
9.70 x 9.70 x 7.00 mm
