intechstudio/grid-hardware/Mechanical/Design/PLASTIC-CAP-FADER/PLASTIC-CAP-FADER_printable.FCStd

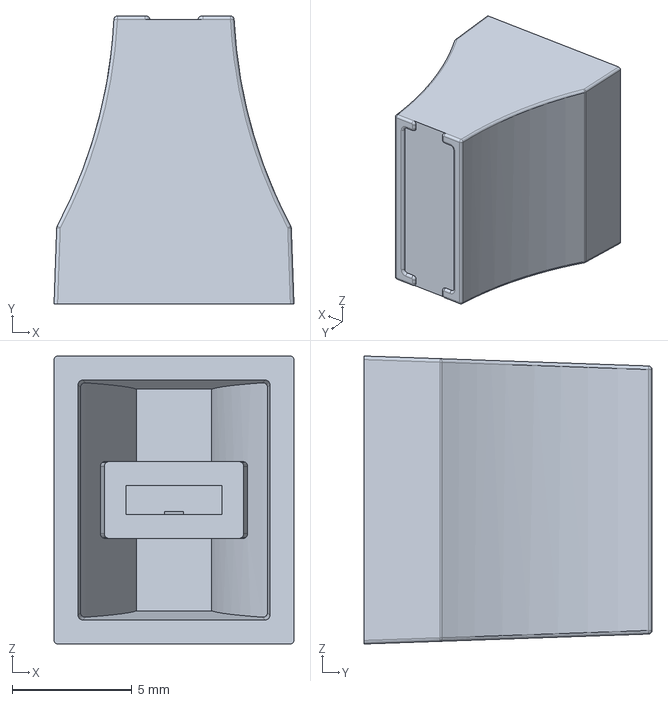
[picture p94: CAD file, 2025-09-02]
Mechanical/Design/PLASTIC-CAP-FADER/PLASTIC-CAP-FADER_printable.FCStd
10.00 x 12.0 x 12.0 mm
