intechstudio/grid-hardware/Mechanical/Design/PLASTIC-KNOB-ENC/PLASTIC-KNOB-ENC_v2.FCStd

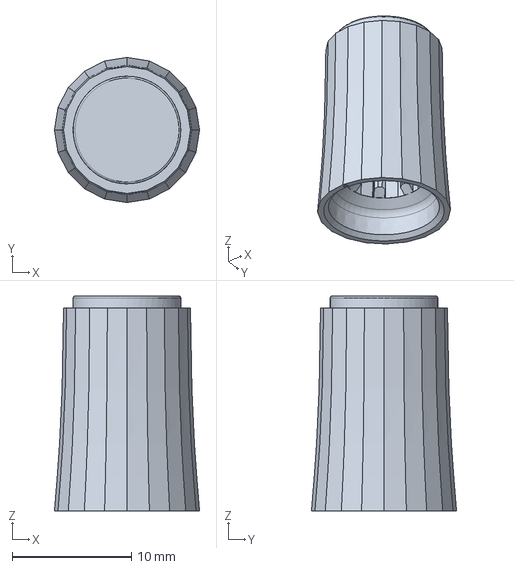
[picture p95: CAD file, 2025-09-30]
Mechanical/Design/PLASTIC-KNOB-ENC/PLASTIC-KNOB-ENC_v2.FCStd
12.1 x 12.1 x 18.0 mm
