intechstudio/grid-hardware/Mechanical/Design/PLASTIC-LIGHTPIPE/PLASTIC-LIGHTPIPE.FCStd

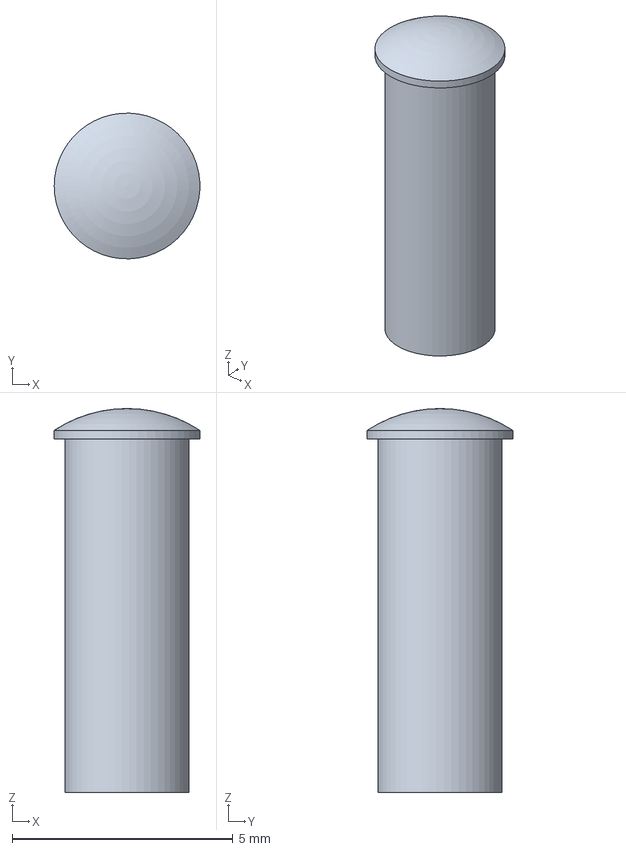
[picture p96: CAD file, 2025-09-19]
Mechanical/Design/PLASTIC-LIGHTPIPE/PLASTIC-LIGHTPIPE.FCStd
3.30 x 3.30 x 8.69 mm
