intechstudio/grid-hardware/Mechanical/Design/PLASTIC-LOW-PROFILE-KEYCAP/PLASTIC-LOW-PROFILE-KEYCAP_THT.FCStd

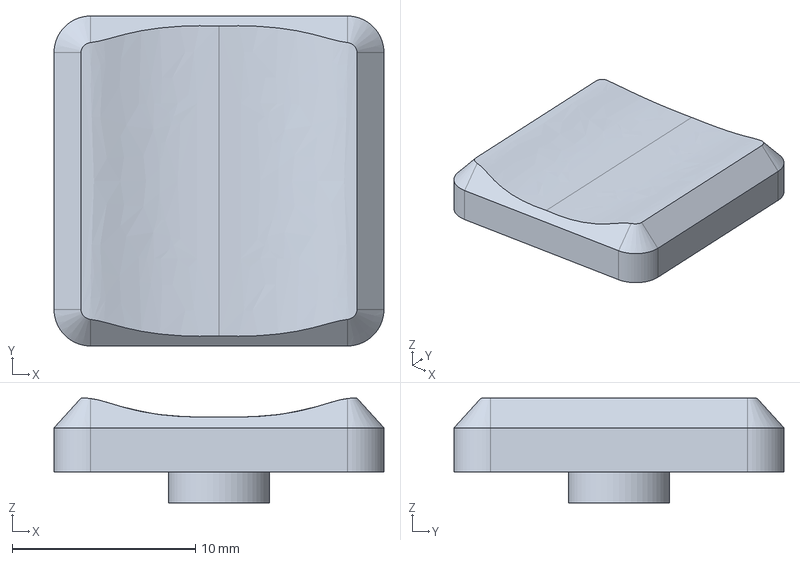
[picture p97: CAD file, 2025-09-19]
Mechanical/Design/PLASTIC-LOW-PROFILE-KEYCAP/PLASTIC-LOW-PROFILE-KEYCAP_THT.FCStd
18.0 x 18.0 x 5.72 mm
