intechstudio/grid-hardware/Mechanical/Design/PLASTIC-MAGNET-COVER/PLASTIC-MAGNET-COVER.FCStd

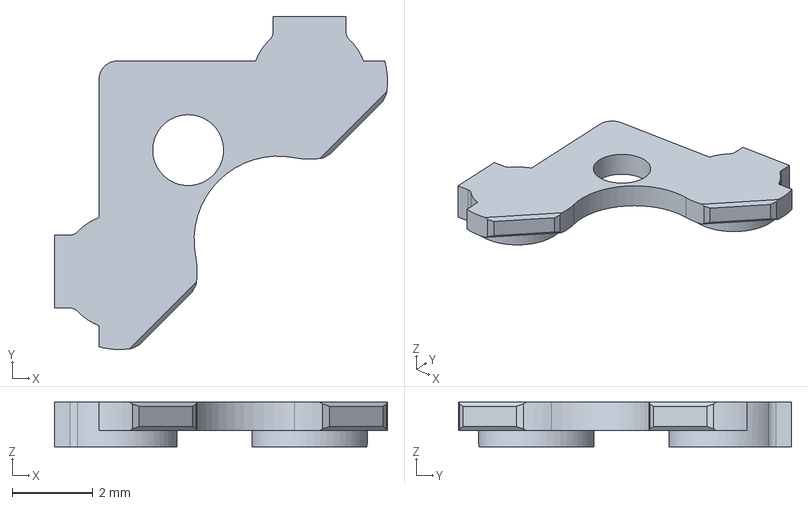
[picture p98: CAD file, 2025-03-10]
Mechanical/Design/PLASTIC-MAGNET-COVER/PLASTIC-MAGNET-COVER.FCStd
8.22 x 8.22 x 1.10 mm
