intechstudio/grid-hardware/Mechanical/Design/PLASTIC-MAPMODE/PLASTIC-MAPMODE.FCStd

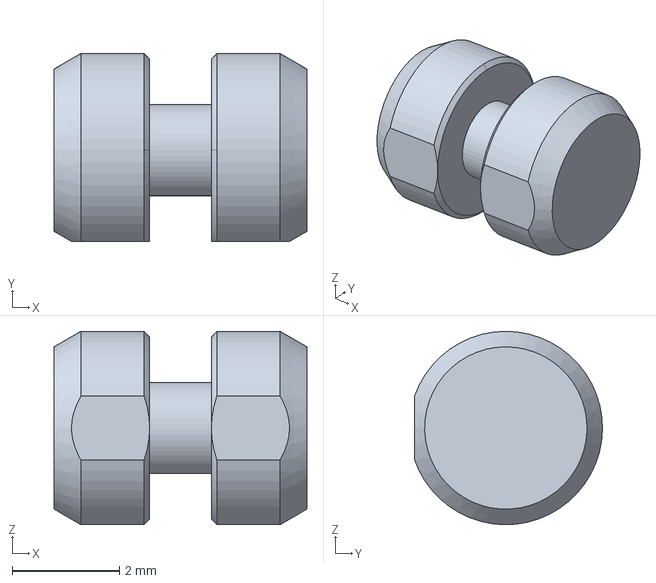
[picture p99: CAD file, 2025-09-30]
Mechanical/Design/PLASTIC-MAPMODE/PLASTIC-MAPMODE.FCStd
4.71 x 3.50 x 3.60 mm
