intechstudio/grid-hardware/Mechanical/Design/PLASTIC-OCTV-KEY/PLASTIC-OCTV-KEY.FCStd

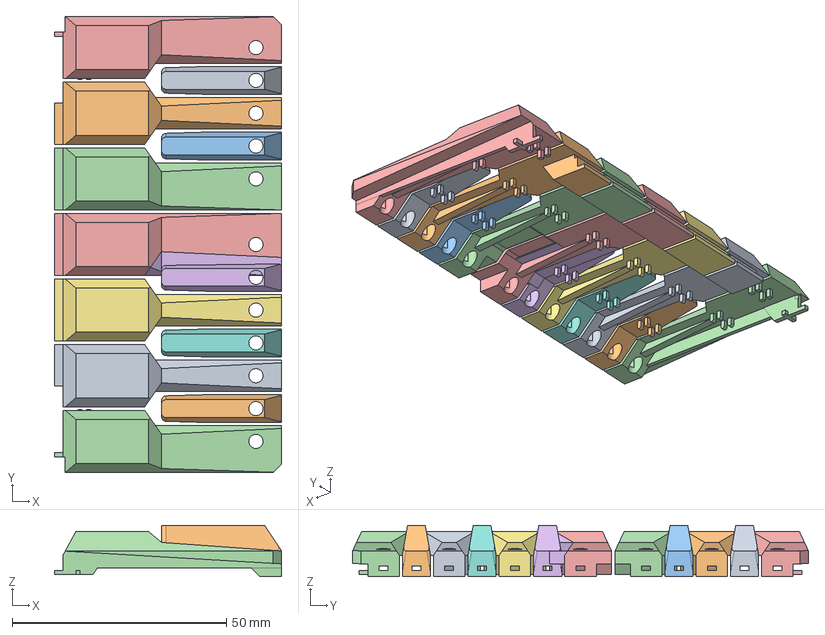
[picture p100: CAD file, 2026-06-01]
Mechanical/Design/PLASTIC-OCTV-KEY/PLASTIC-OCTV-KEY.FCStd
53.0 x 106.3 x 12.0 mm
black_C#
white_D
black_D#
white_E
white_F
black_F#
white_G
black_G#
white_A
black_A#
white_B
white_C (Mirror #1)
white_LeftCut_BASE
