intechstudio/grid-hardware/Mechanical/Design/PLASTIC-TEK2-KNOB-INTERFACE/PLASTIC-TEK2-KNOB-INTERFACE_Bence_printer.FCStd

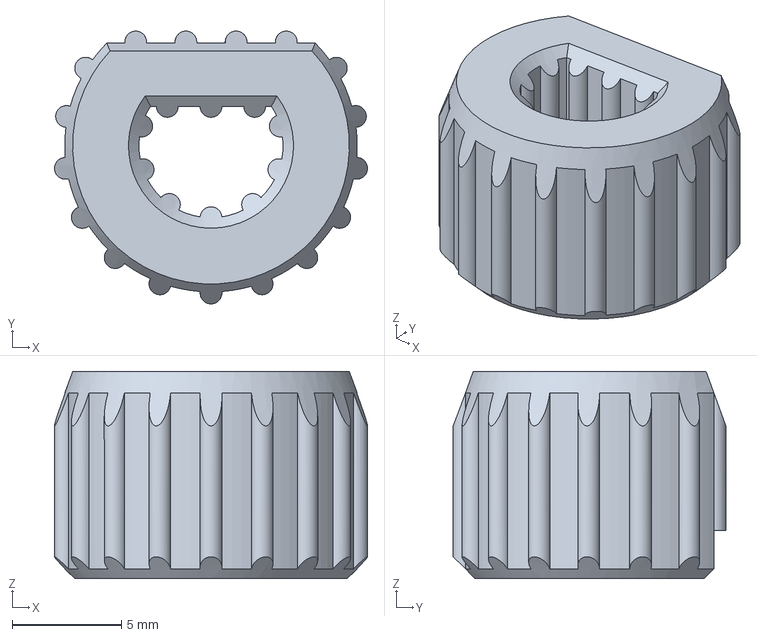
[picture p101: CAD file, 2025-09-30]
Mechanical/Design/PLASTIC-TEK2-KNOB-INTERFACE/PLASTIC-TEK2-KNOB-INTERFACE_Bence_printer.FCStd
14.3 x 12.5 x 9.50 mm
