intechstudio/grid-hardware/Mechanical/Design/PLASTIC-VSN-DISPLAY-SPACER/PLASTIC-VSN-DISPLAY-SPACER_2.FCStd

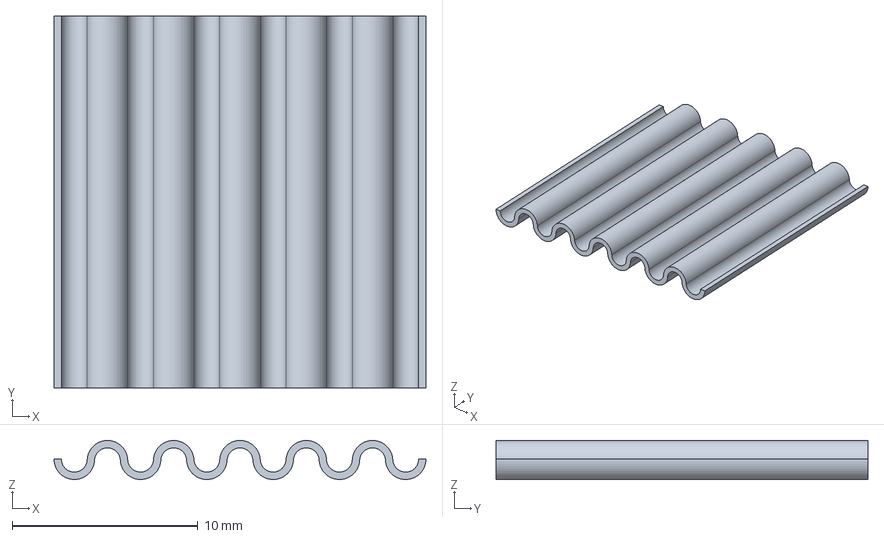
[picture p102: CAD file, 2025-03-20]
Mechanical/Design/PLASTIC-VSN-DISPLAY-SPACER/PLASTIC-VSN-DISPLAY-SPACER_2.FCStd
20.0 x 20.0 x 2.10 mm
