intechstudio/grid-hardware/Mechanical/Design/PLASTIC-VSN1-BUTTON/PLASTIC-VSN1-BUTTON.FCStd

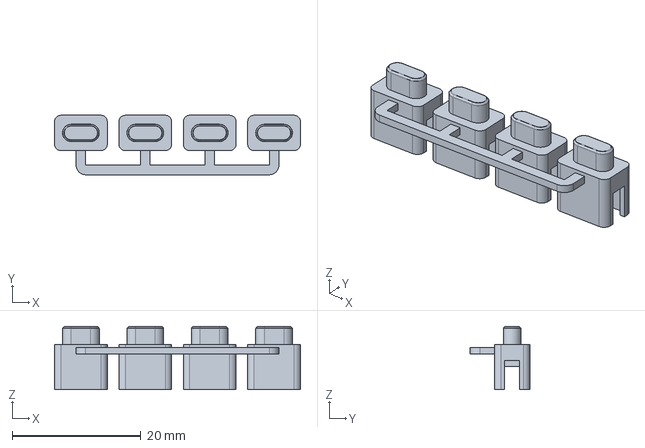
[picture p103: CAD file, 2025-09-19]
Mechanical/Design/PLASTIC-VSN1-BUTTON/PLASTIC-VSN1-BUTTON.FCStd
38.2 x 9.25 x 9.80 mm
