intechstudio/grid-hardware/Mechanical/Design/PLASTIC-VSN1-DISPLAY-INTERFACE/PLASTIC-VSN1-DISPLAY-INTERFACE.FCStd

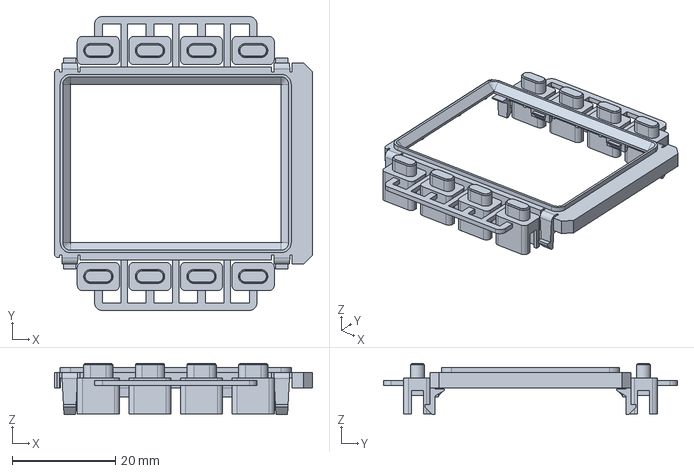
[picture p104: CAD file, 2026-02-25]
Mechanical/Design/PLASTIC-VSN1-DISPLAY-INTERFACE/PLASTIC-VSN1-DISPLAY-INTERFACE.FCStd
50.1 x 57.0 x 9.95 mm
