intechstudio/grid-hardware/Mechanical/Design/Pogo/Custom IS_POGO_Rev2_Latest/Ball_test.FCStd

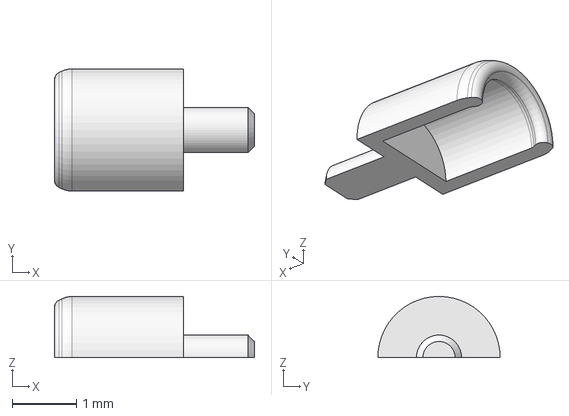
[picture p105: CAD file, 2020-11-19]
Mechanical/Design/Pogo/Custom IS_POGO_Rev2_Latest/Ball_test.FCStd
3.11 x 1.90 x 0.95 mm
