intechstudio/grid-hardware/Mechanical/Design/RUBBER-FOOT/RUBBER-FOOT.FCStd

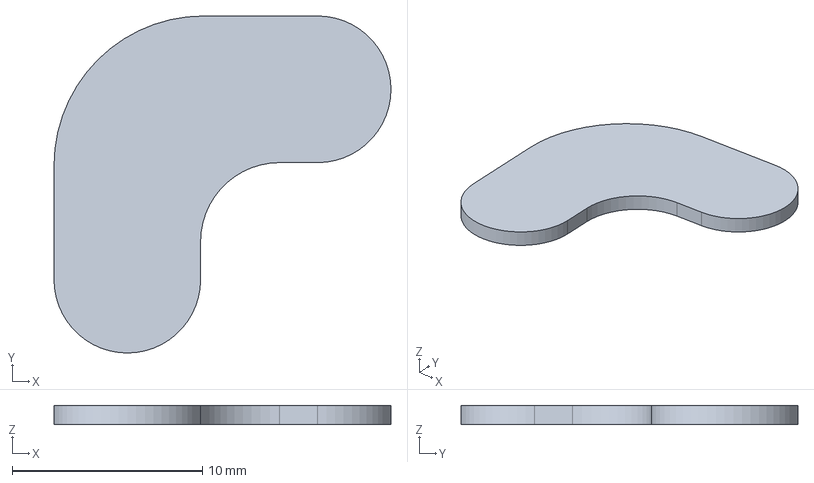
[picture p106: CAD file, 2025-09-02]
Mechanical/Design/RUBBER-FOOT/RUBBER-FOOT.FCStd
17.7 x 17.7 x 1.00 mm
