intechstudio/grid-hardware/Mechanical/Design/SMT-CONN-BATTERY/SMT-CONN-BATTERY.FCStd

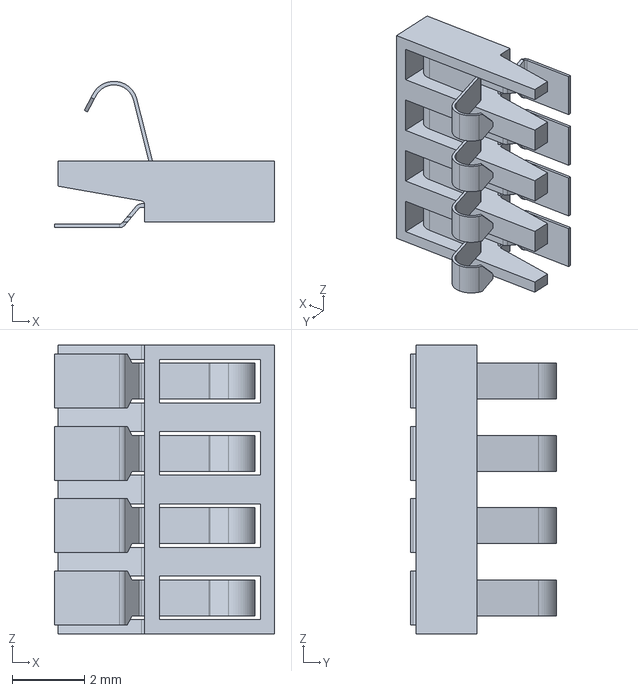
[picture p107: CAD file, 2025-04-26]
Mechanical/Design/SMT-CONN-BATTERY/SMT-CONN-BATTERY.FCStd
6.10 x 4.05 x 8.00 mm
