intechstudio/grid-hardware/Mechanical/Design/SMT-CONN-POGO/SMT-CONN-POGO.FCStd

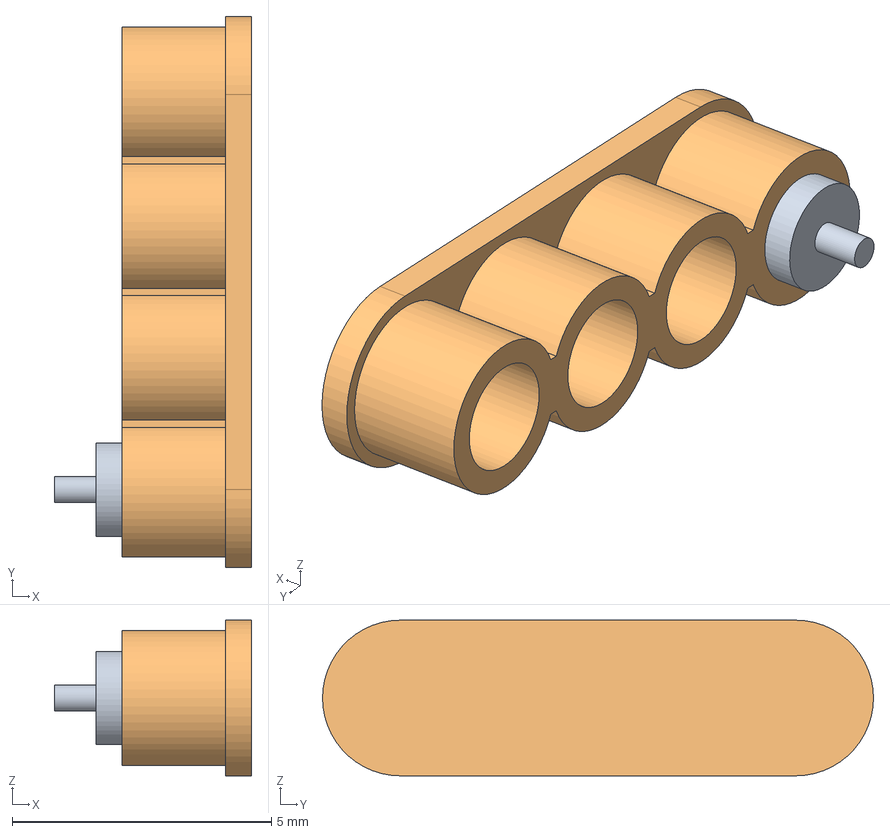
[picture p108: CAD file, 2025-04-26]
Mechanical/Design/SMT-CONN-POGO/SMT-CONN-POGO.FCStd
3.80 x 10.6 x 3.00 mm
SMT-CONN-POGO
SMT-CONN-POGO_Cap
