intechstudio/grid-hardware/Mechanical/Design/SMT-VSN1-DISPLAY/SMT-VSN1-DISPLAY.FCStd

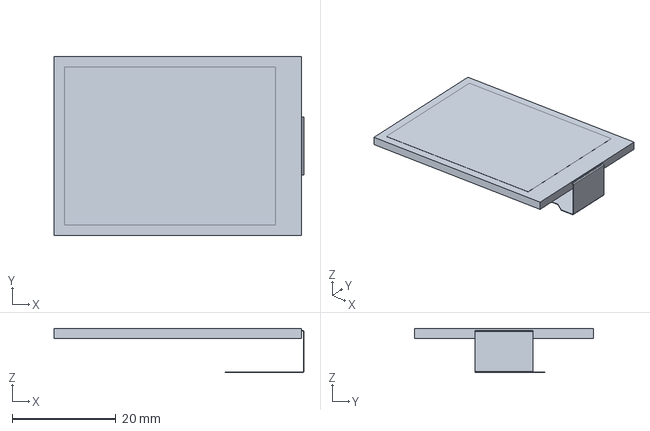
[picture p109: CAD file, 2025-09-05]
Mechanical/Design/SMT-VSN1-DISPLAY/SMT-VSN1-DISPLAY.FCStd
48.3 x 34.6 x 8.55 mm
