intechstudio/grid-hardware/Mechanical/Design/SPACER/SPACER.FCStd

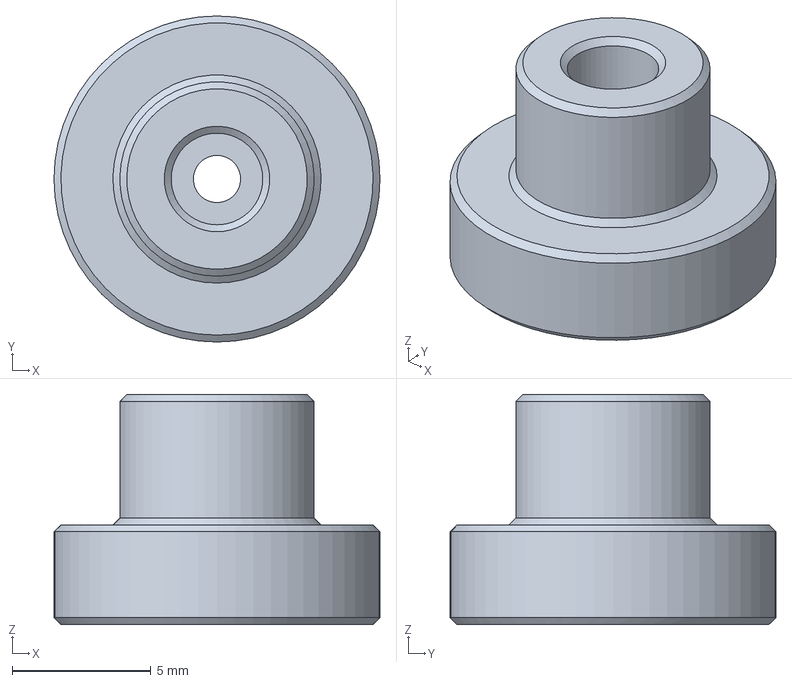
[picture p110: CAD file, 2026-03-20]
Mechanical/Design/SPACER/SPACER.FCStd
11.8 x 11.8 x 8.30 mm
