intechstudio/grid-hardware/Mechanical/Design/THT-BUTTON/THT-BUTTON.FCStd

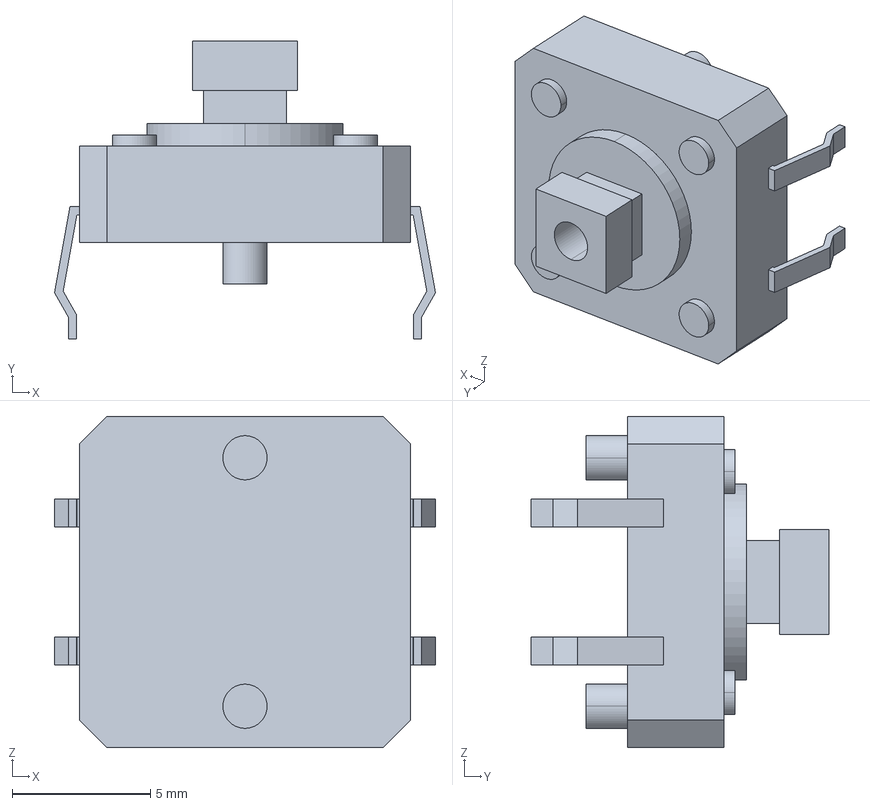
[picture p111: CAD file, 2025-04-26]
Mechanical/Design/THT-BUTTON/THT-BUTTON.FCStd
13.8 x 10.8 x 12.0 mm
