intechstudio/grid-hardware/Mechanical/Design/THT-ENC/THT-ENC.step

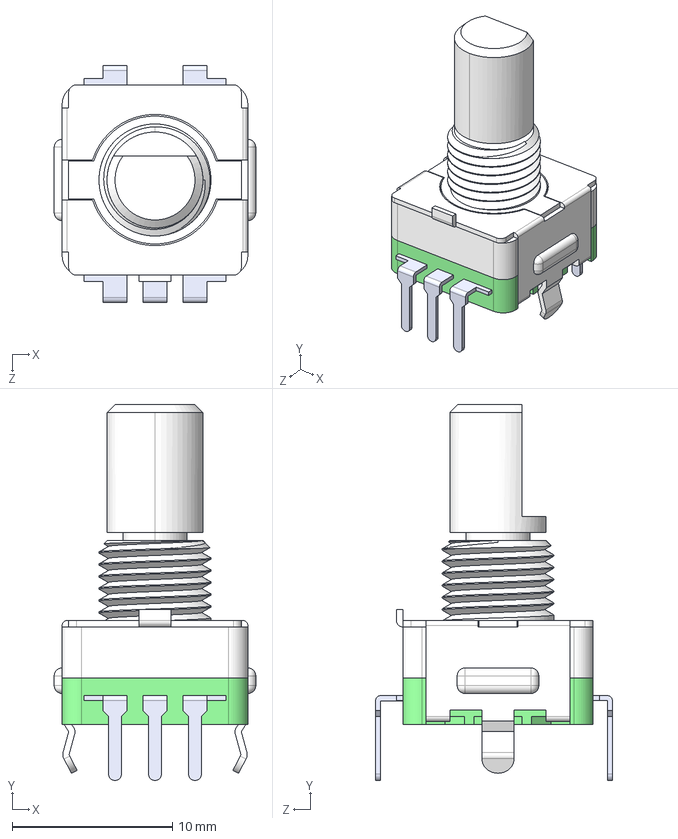
[picture p112: CAD file, 2025-09-02]
Mechanical/Design/THT-ENC/THT-ENC.step
12.6 x 23.5 x 14.8 mm
端子
支架
轴套
13.5F-N=5-F=7
