intechstudio/grid-hardware/Mechanical/Design/THT-ENDLESSPOT/THT-ENDLESSPOT.FCStd

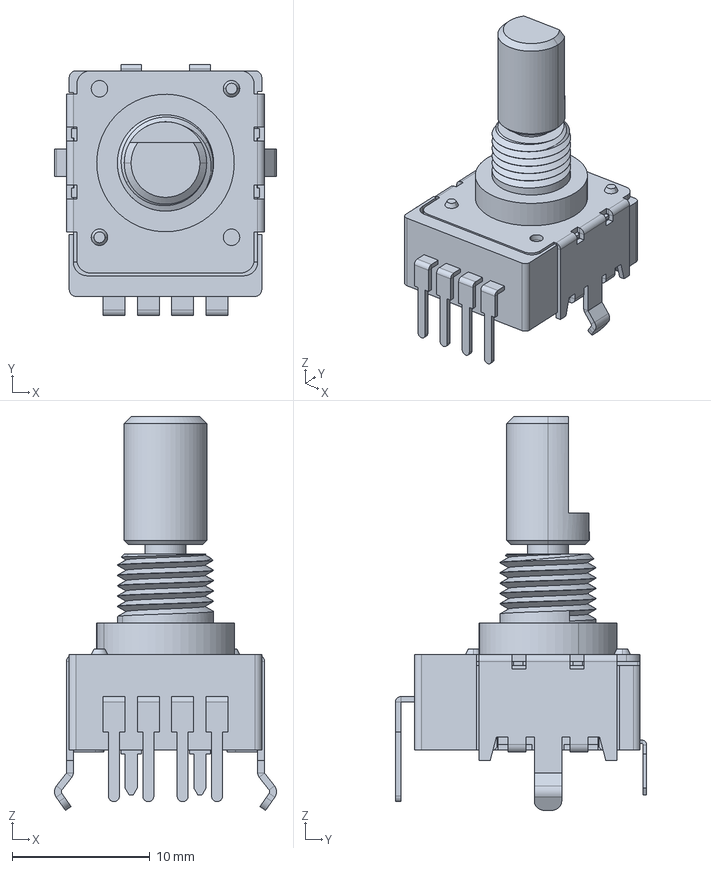
[picture p113: CAD file, 2025-09-19]
Mechanical/Design/THT-ENDLESSPOT/THT-ENDLESSPOT.FCStd
16.1 x 18.3 x 28.6 mm
