intechstudio/grid-hardware/Mechanical/Design/THT-FADER/THT-FADER.FCStd

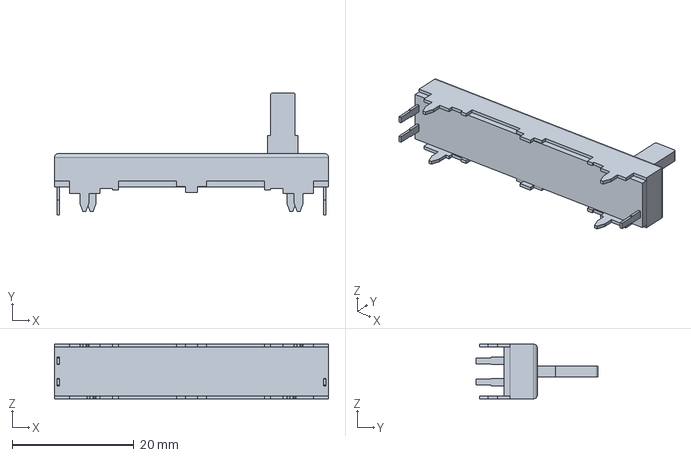
[picture p114: CAD file, 2025-04-26]
Mechanical/Design/THT-FADER/THT-FADER.FCStd
45.0 x 20.1 x 9.00 mm
