intechstudio/grid-hardware/Mechanical/Design/THT-HALL-SWITCH/THT-HALL-SWITCH.FCStd

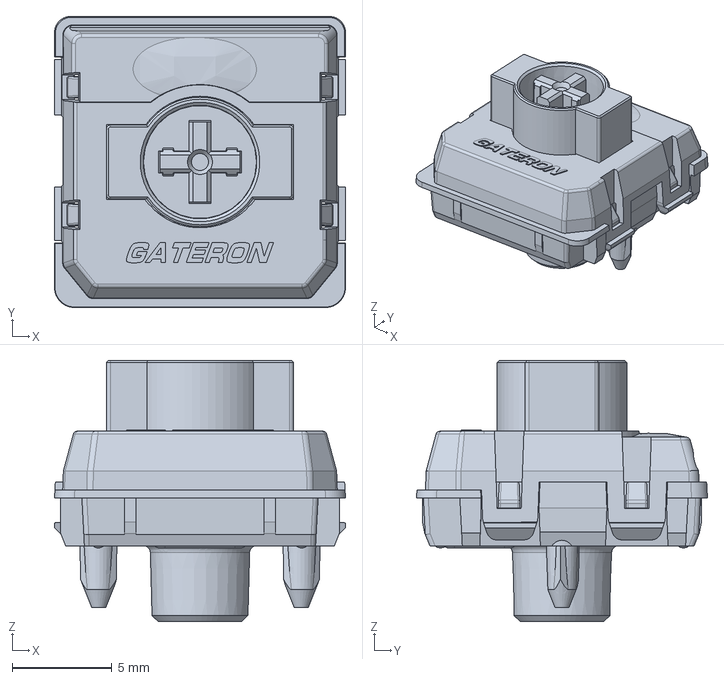
[picture p115: CAD file, 2025-09-19]
Mechanical/Design/THT-HALL-SWITCH/THT-HALL-SWITCH.FCStd
14.6 x 14.6 x 13.1 mm
