intechstudio/grid-hardware/Mechanical/Design/THT-LONGFADER/THT-LONGFADER.FCStd

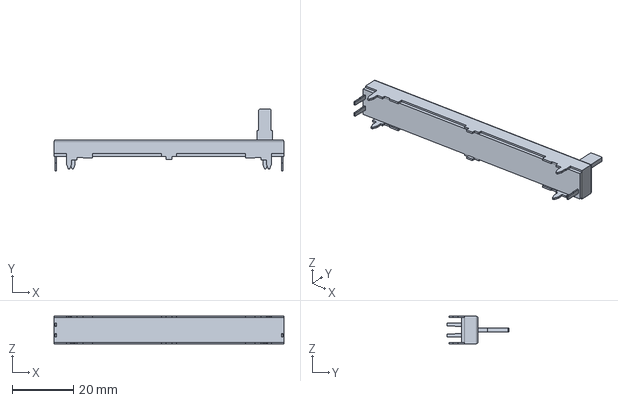
[picture p116: CAD file, 2025-04-26]
Mechanical/Design/THT-LONGFADER/THT-LONGFADER.FCStd
75.0 x 20.1 x 9.00 mm
