intechstudio/grid-hardware/Mechanical/Design/THT-POT/THT-POT.step

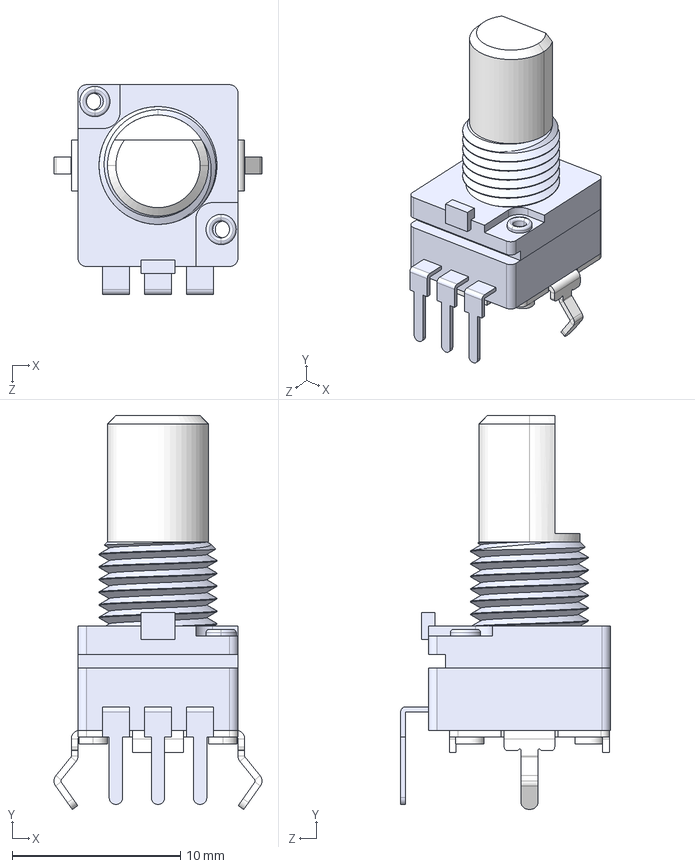
[picture p117: CAD file, 2025-09-02]
Mechanical/Design/THT-POT/THT-POT.step
12.3 x 23.4 x 12.5 mm
轴套N=5
支架
电阻片
轴心12.5F-N=5
