intechstudio/grid-hardware/Mechanical/Experiment/3DFDM_Base/3DFDM_Attachment_tool.FCStd

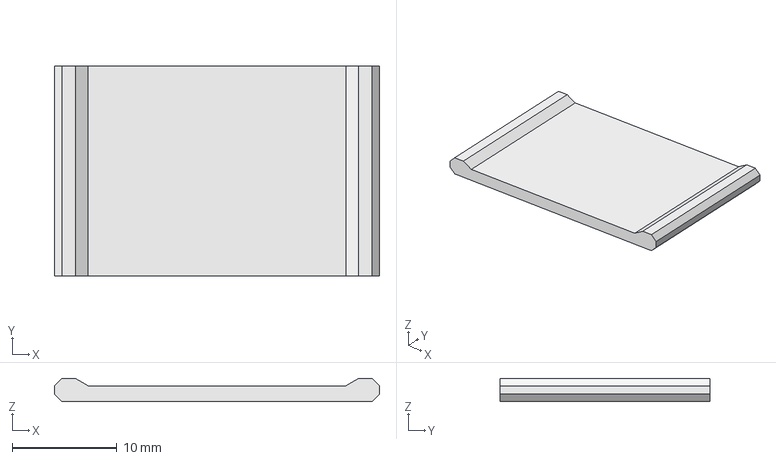
[picture p118: CAD file, 2024-07-18]
Mechanical/Experiment/3DFDM_Base/3DFDM_Attachment_tool.FCStd
31.0 x 20.0 x 2.20 mm
