intechstudio/grid-hardware/Mechanical/Experiment/DisplayStand/mfg/Pin.stl

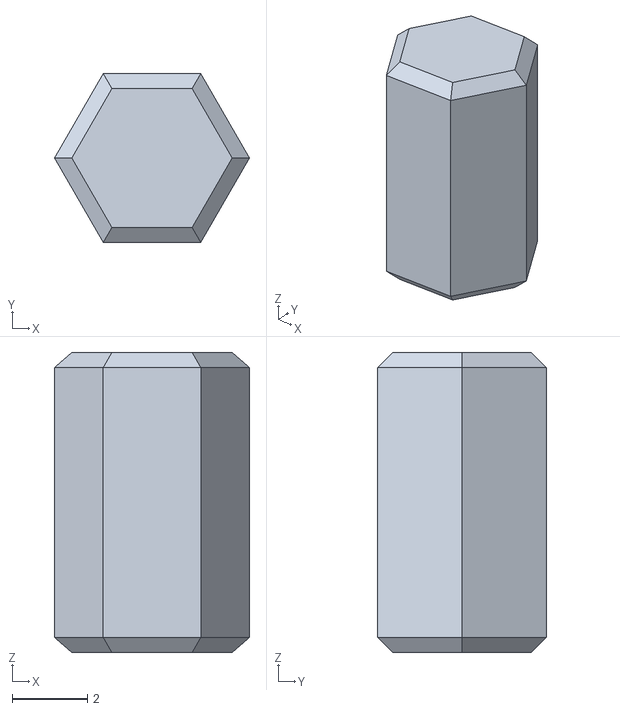
[picture p119: CAD file, 2021-10-01]
Mechanical/Experiment/DisplayStand/mfg/Pin.stl
5.20 x 4.50 x 8.00
