intechstudio/grid-hardware/Mechanical/Experiment/DisplayStand/module_display_stand_dual.FCStd

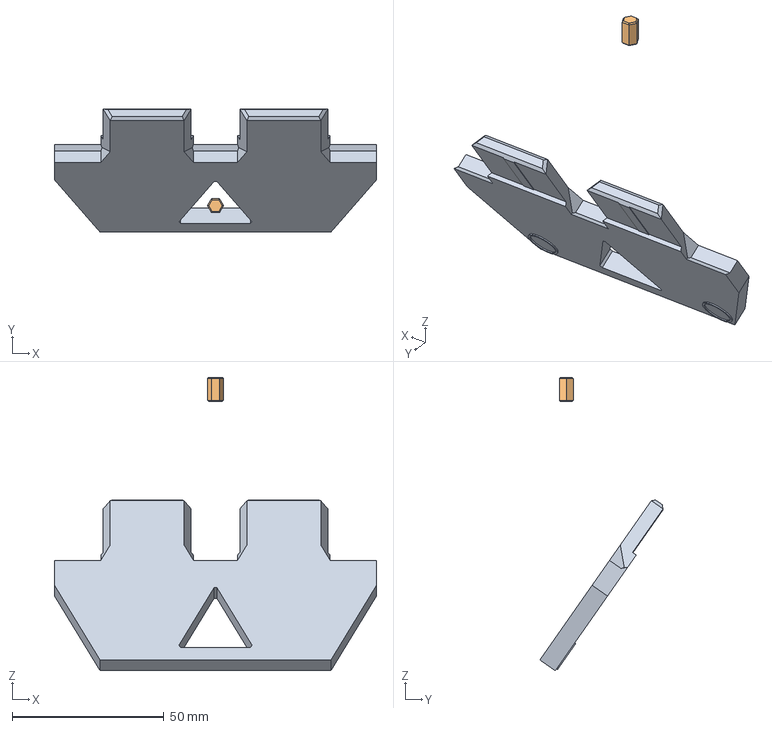
[picture p120: CAD file, 2024-02-27]
Mechanical/Experiment/DisplayStand/module_display_stand_dual.FCStd
106.0 x 40.6 x 96.6 mm
Leg
Pin
