intechstudio/grid-hardware/Mechanical/Experiment/Eurorack_adapter/eurorack_adapter.FCStd

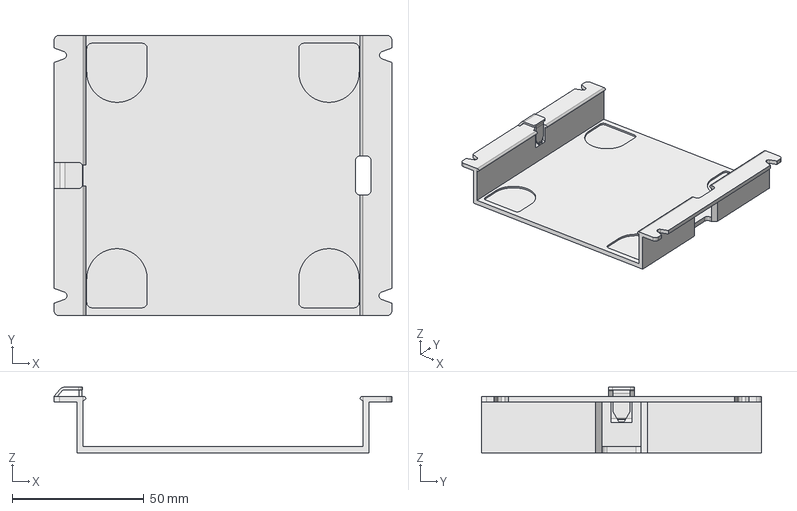
[picture p121: CAD file, 2024-03-20]
Mechanical/Experiment/Eurorack_adapter/eurorack_adapter.FCStd
128.5 x 106.6 x 25.0 mm
