intechstudio/grid-hardware/Mechanical/Experiment/Eurorack_adapter/w_button/eurorack_adapter_v3_shorter button.FCStd

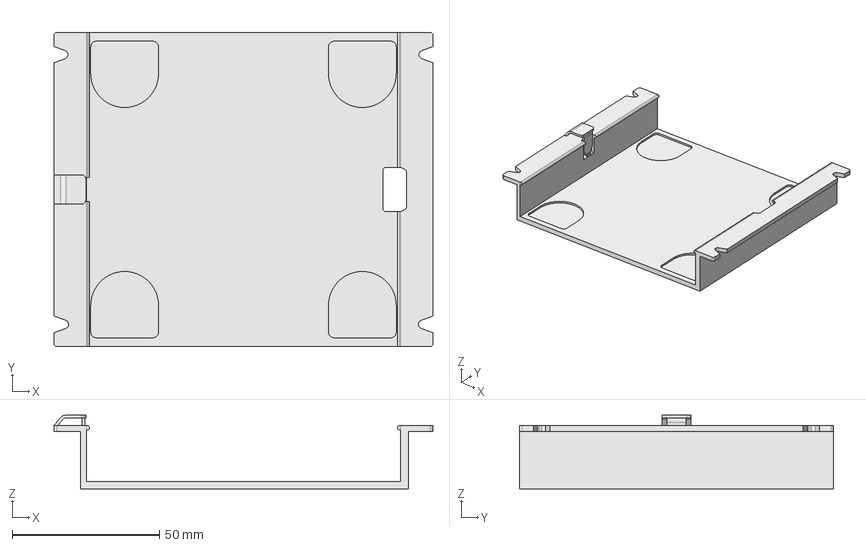
[picture p122: CAD file, 2024-03-04]
Mechanical/Experiment/Eurorack_adapter/w_button/eurorack_adapter_v3_shorter button.FCStd
128.5 x 106.6 x 25.0 mm
