intechstudio/grid-hardware/Mechanical/Experiment/Eurorack_adapter/wo_button/eurorack_adapter_wo_switch.FCStd

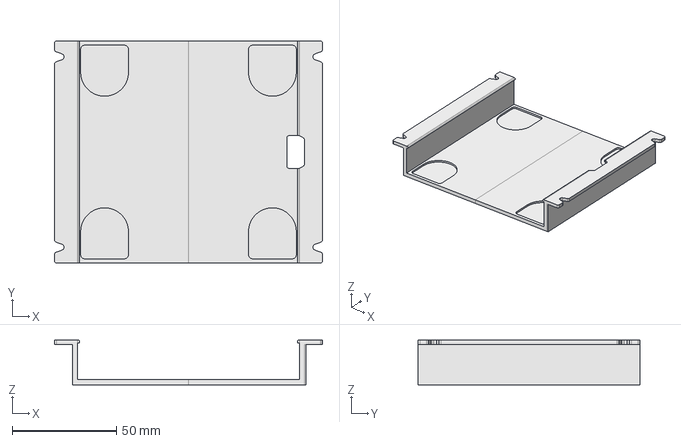
[picture p123: CAD file, 2024-02-26]
Mechanical/Experiment/Eurorack_adapter/wo_button/eurorack_adapter_wo_switch.FCStd
128.7 x 106.6 x 21.5 mm
