intechstudio/grid-hardware/Mechanical/Experiment/Eurorack_leg/eurorack_leg.FCStd

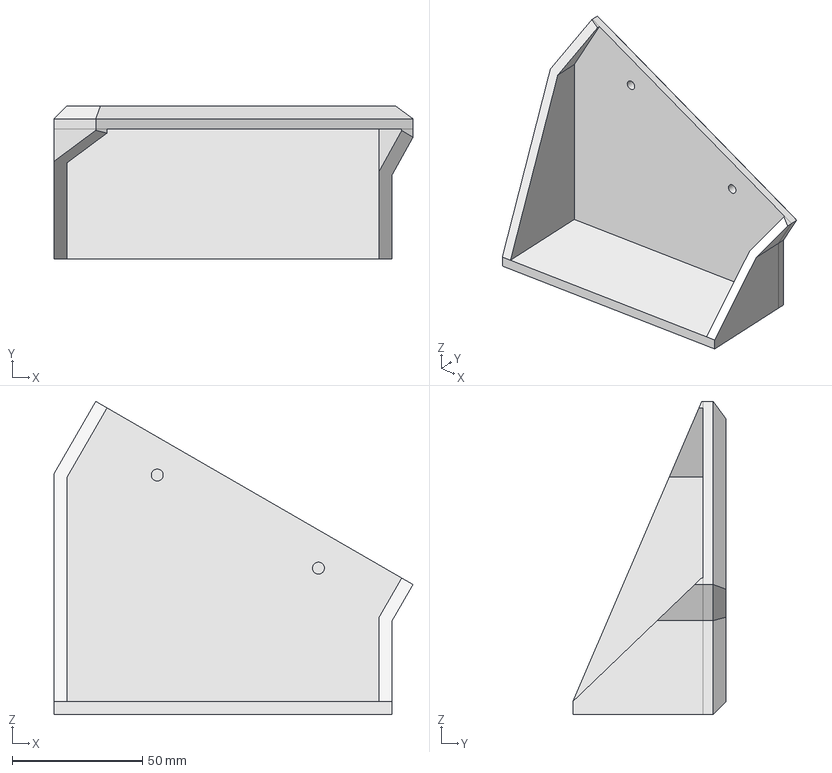
[picture p124: CAD file, 2024-03-27]
Mechanical/Experiment/Eurorack_leg/eurorack_leg.FCStd
138.0 x 59.0 x 120.4 mm
