intechstudio/grid-hardware/Mechanical/Experiment/Octave/piano.FCStd

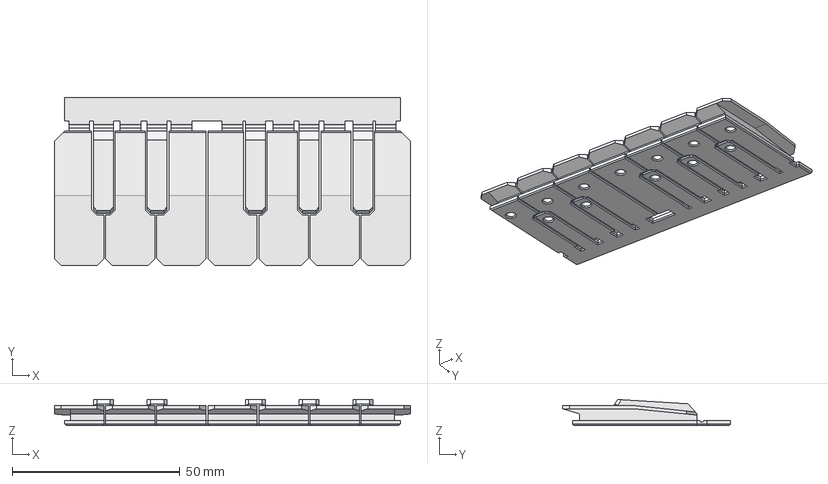
[picture p125: CAD file, 2021-09-23]
Mechanical/Experiment/Octave/piano.FCStd
106.1 x 50.0 x 7.78 mm
