intechstudio/grid-hardware/Mechanical/R0903N_L-20F-PH.STEP

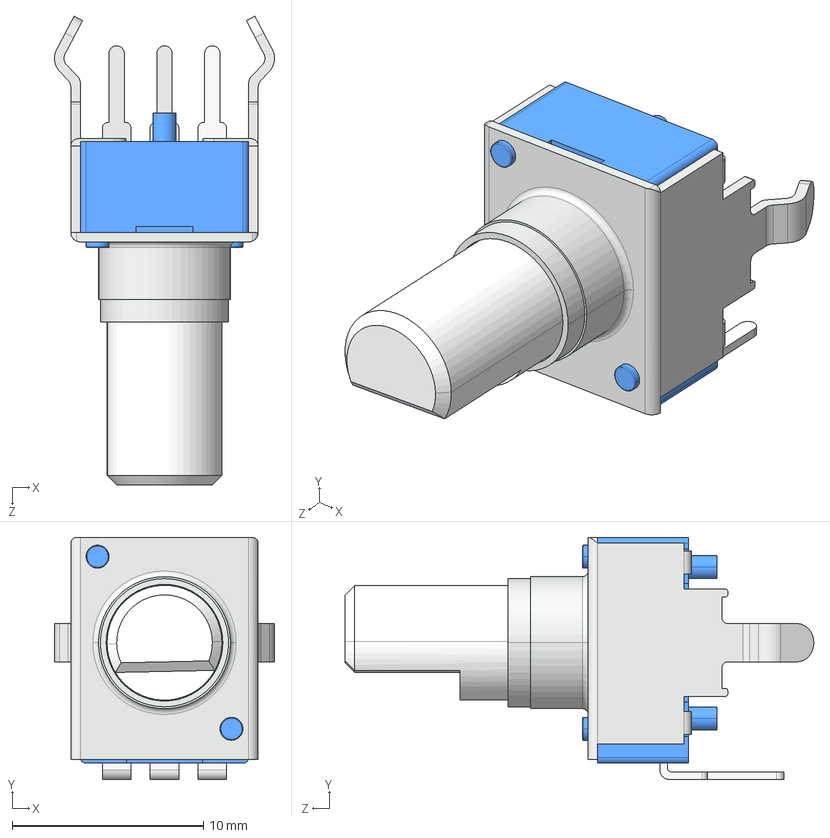
[picture p126: CAD file, 2021-10-26]
Mechanical/R0903N_L-20F-PH.STEP
11.5 x 12.7 x 24.5 mm
r0902n-1.prt.6
r0903n盓殤
i19310
