intechstudio/grid-hardware/Mechanical/Source/canvas_injection.FCStd

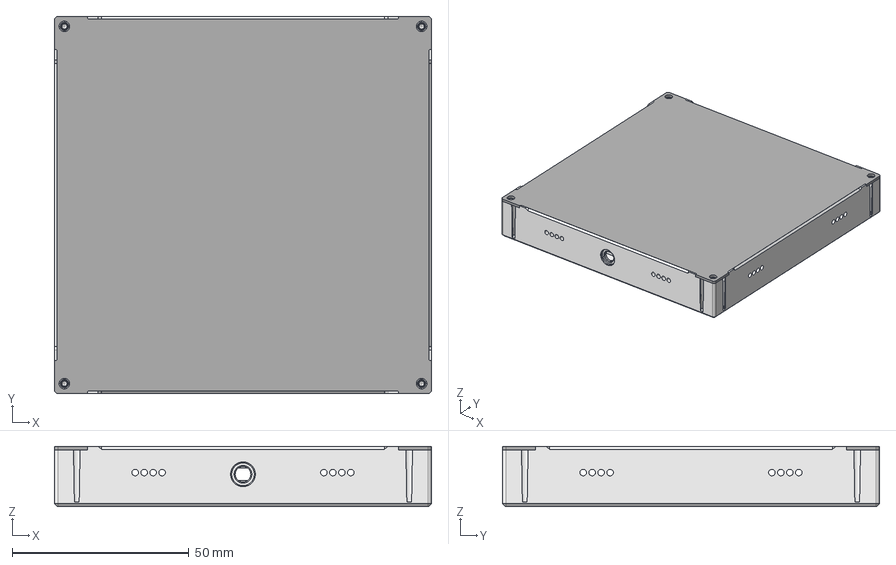
[picture p127: CAD file, 2022-08-11]
Mechanical/Source/canvas_injection.FCStd
106.6 x 106.6 x 17.0 mm
G4_Unibody
Frontpanel
