intechstudio/grid-hardware/Manufacturing/bushing_jig/drill_chuck_base.FCStd

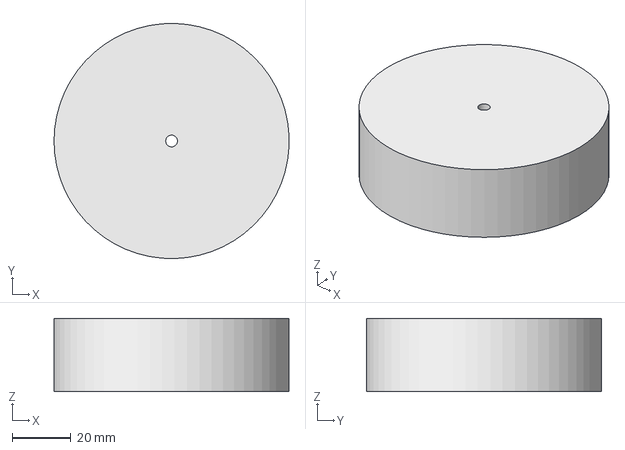
[picture p128: CAD file, 2024-02-26]
Manufacturing/bushing_jig/drill_chuck_base.FCStd
79.9 x 80.0 x 25.0 mm
