intechstudio/grid-hardware/Manufacturing/CNC/Electronics/Driver-3.5A.STEP

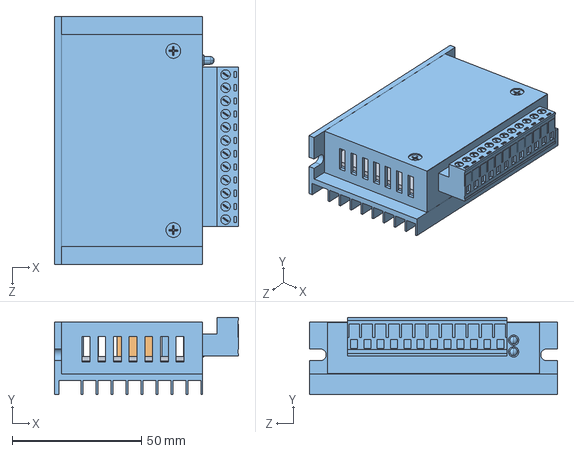
[picture p129: CAD file, 2021-02-25]
Manufacturing/CNC/Electronics/Driver-3.5A.STEP
71.2 x 29.8 x 96.0 mm
