intechstudio/grid-hardware/Manufacturing/CNC/vacuum_hose_mount.FCStd

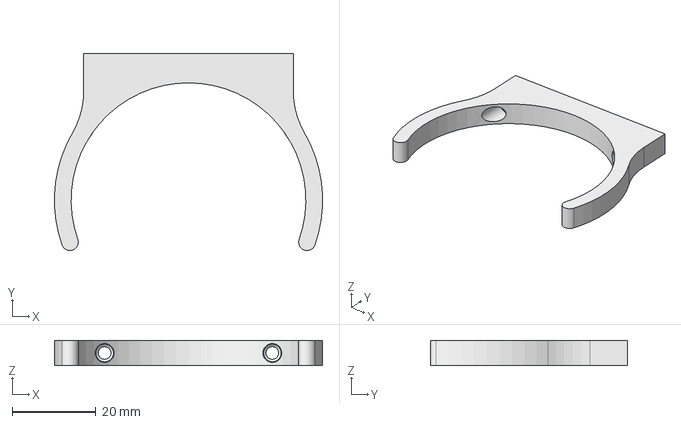
[picture p130: CAD file, 2021-04-12]
Manufacturing/CNC/vacuum_hose_mount.FCStd
63.9 x 47.0 x 6.00 mm
