intechstudio/grid-hardware/Manufacturing/flatness_QC_jig/qc_jig_box.FCStd

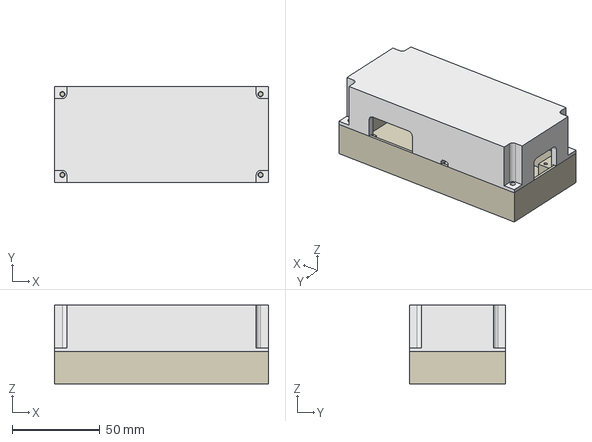
[picture p131: CAD file, 2024-06-20]
Manufacturing/flatness_QC_jig/qc_jig_box.FCStd
122.0 x 55.0 x 45.0 mm
