intechstudio/grid-hardware/Manufacturing/Fumefood/accessories/ethernet_panel.FCStd

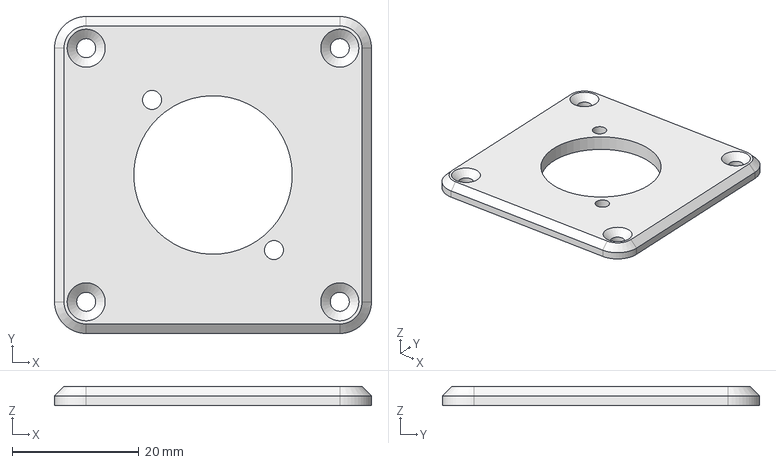
[picture p132: CAD file, 2021-02-25]
Manufacturing/Fumefood/accessories/ethernet_panel.FCStd
50.0 x 50.0 x 3.00 mm
