intechstudio/grid-hardware/Manufacturing/iroda/tabla_kozepso_lab_tarto.FCStd

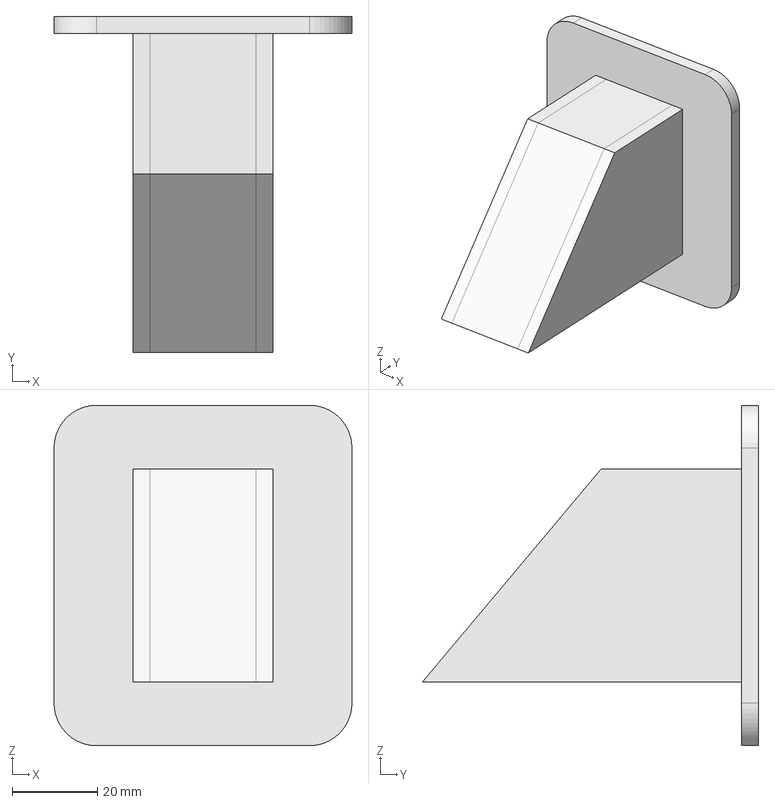
[picture p133: CAD file, 2024-03-14]
Manufacturing/iroda/tabla_kozepso_lab_tarto.FCStd
70.0 x 79.0 x 80.0 mm
