intechstudio/grid-hardware/Manufacturing/Laser/plotter_pen_holder_2.FCStd

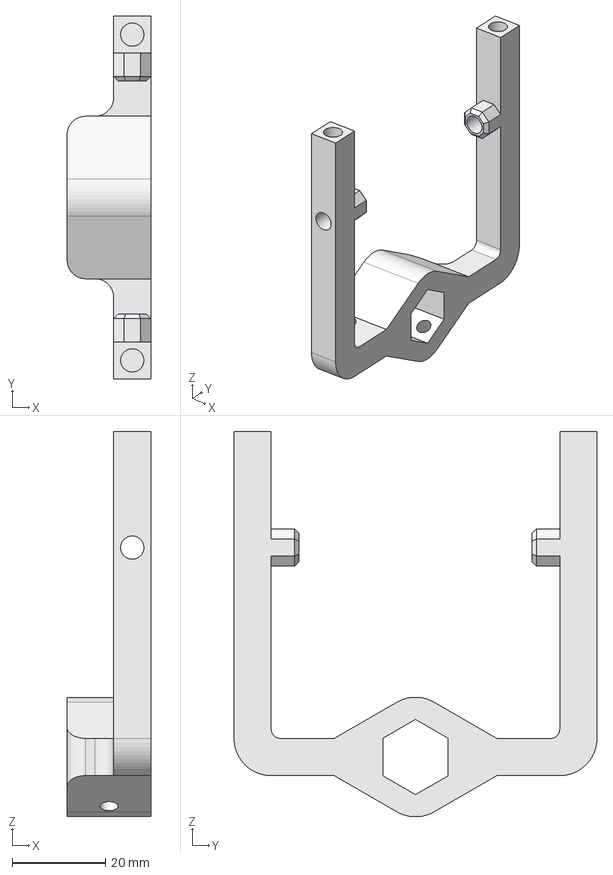
[picture p134: CAD file, 2021-02-25]
Manufacturing/Laser/plotter_pen_holder_2.FCStd
18.0 x 78.0 x 82.8 mm
