intechstudio/grid-hardware/Manufacturing/Packaging/cardboard_hanger.FCStd

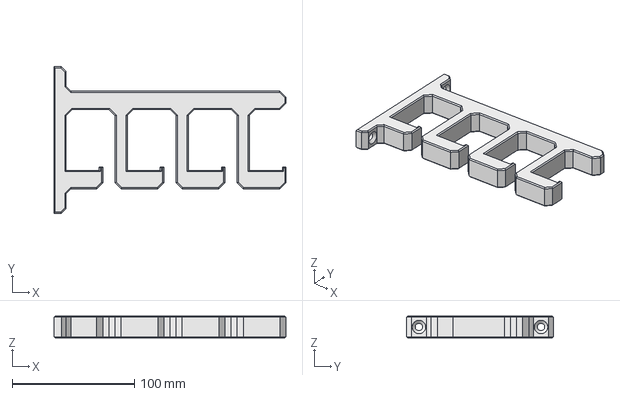
[picture p135: CAD file, 2021-10-15]
Manufacturing/Packaging/cardboard_hanger.FCStd
190.0 x 120.0 x 18.0 mm
