intechstudio/grid-hardware/Manufacturing/Potcap-insert/potcap_indicator_alignment_jig.FCStd

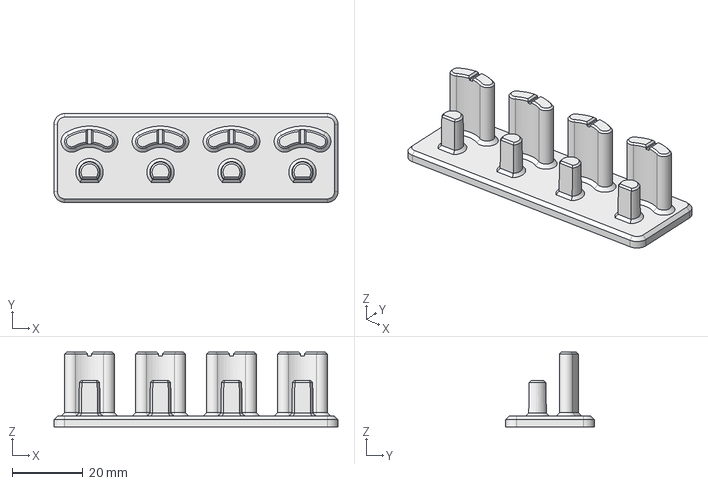
[picture p136: CAD file, 2022-07-05]
Manufacturing/Potcap-insert/potcap_indicator_alignment_jig.FCStd
80.0 x 25.0 x 21.0 mm
