intechstudio/grid-hardware/Manufacturing/random_stuff/alu_profile_T-slot_M5.FCStd

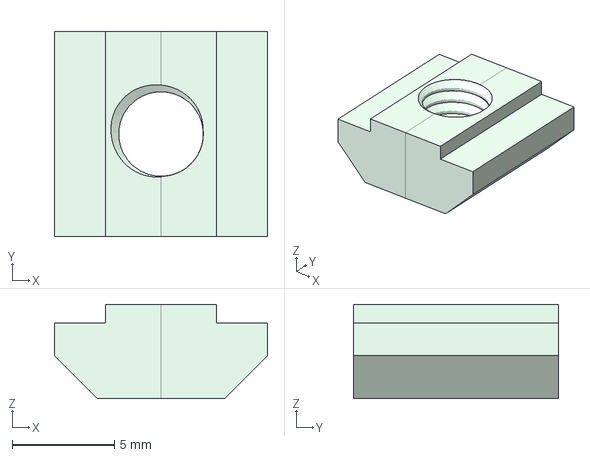
[picture p137: CAD file, 2024-04-25]
Manufacturing/random_stuff/alu_profile_T-slot_M5.FCStd
10.4 x 10.0 x 4.60 mm
