intechstudio/grid-hardware/Mechanical/Assembly/Frontpanels/FRONTPANEL-TEK2.step

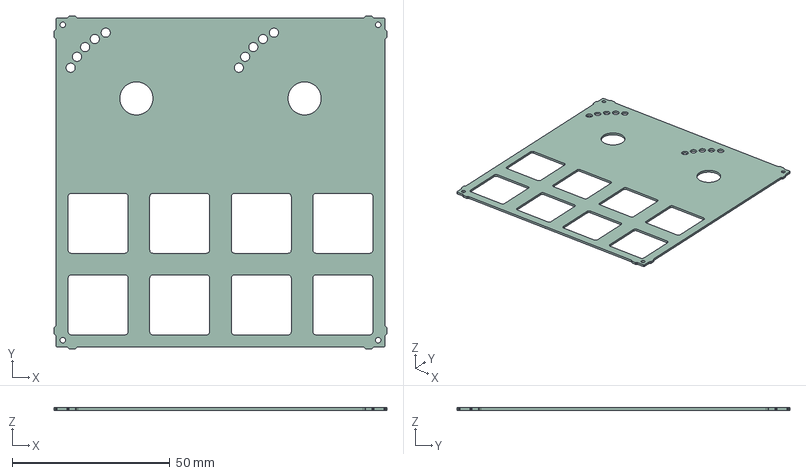
[picture p138: CAD file, 2025-09-02]
Mechanical/Assembly/Frontpanels/FRONTPANEL-TEK2.step
105.6 x 105.6 x 0.91 mm
