intechstudio/grid-hardware/Mechanical/Design/Frontpanel/grid_frontpanel_logo.FCStd

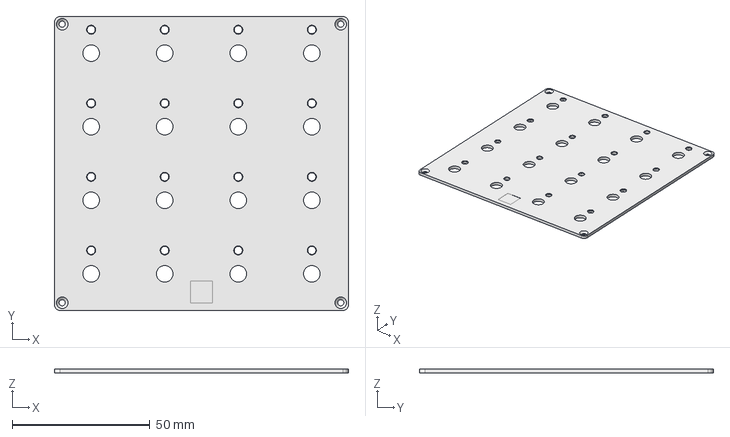
[picture p140: CAD file, 2022-07-28]
Mechanical/Design/Frontpanel/grid_frontpanel_logo.FCStd
106.6 x 106.6 x 1.50 mm
