intechstudio/grid-hardware/Mechanical/Design/PLASTIC-LOW-PROFILE-KEYCAP/PLASTIC-LOW-PROFILE-KEYCAP.FCStd

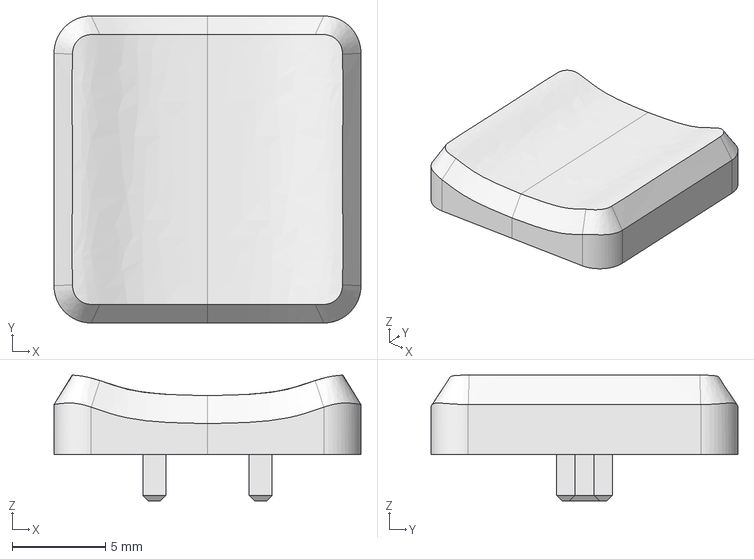
[picture p141: CAD file, 2024-07-11]
Mechanical/Design/PLASTIC-LOW-PROFILE-KEYCAP/PLASTIC-LOW-PROFILE-KEYCAP.FCStd
16.5 x 16.5 x 6.76 mm
