intechstudio/grid-hardware/Mechanical/Design/PLASTIC-MAGNET-COVER/PLASTIC-MAGNET-CLIP.FCStd

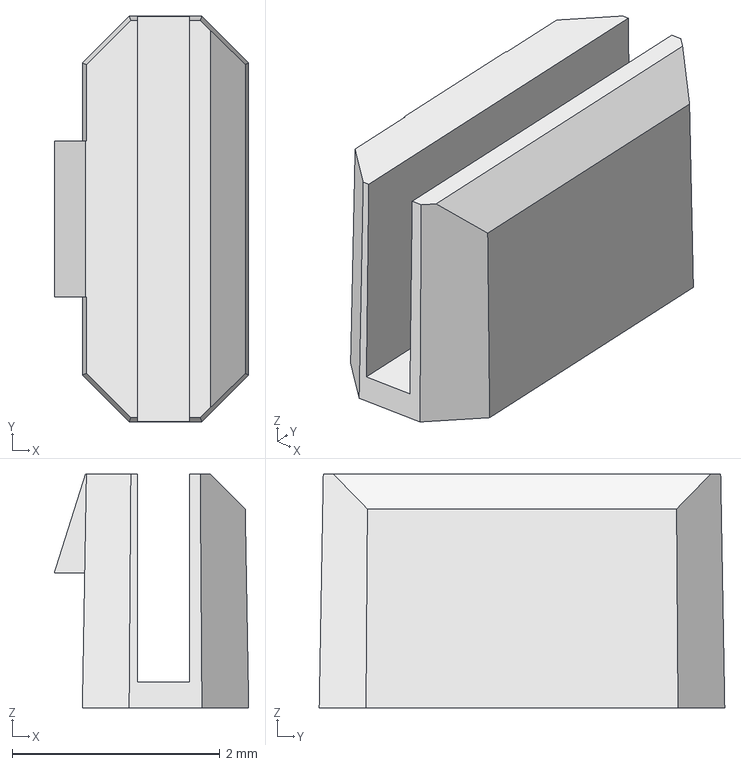
[picture p142: CAD file, 2024-01-03]
Mechanical/Design/PLASTIC-MAGNET-COVER/PLASTIC-MAGNET-CLIP.FCStd
1.87 x 3.90 x 2.25 mm
