intechstudio/grid-hardware/Mechanical/Design/PLASTIC-MAPMODE/PLASTIC-MAPMODE_connected.FCStd

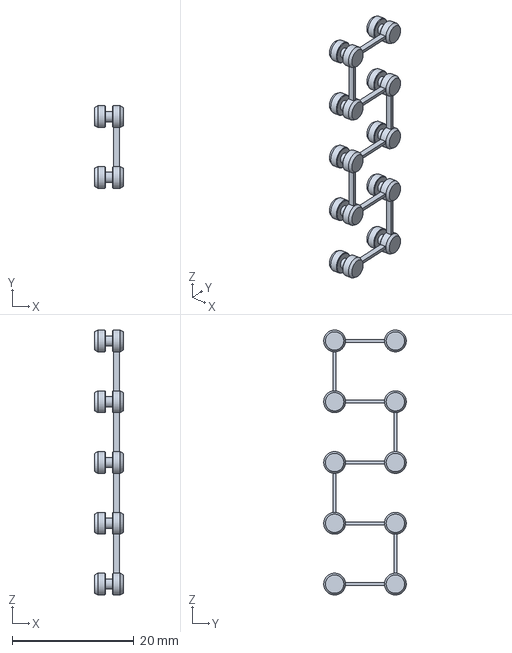
[picture p143: CAD file, 2025-09-30]
Mechanical/Design/PLASTIC-MAPMODE/PLASTIC-MAPMODE_connected.FCStd
4.70 x 13.6 x 43.6 mm
