intechstudio/grid-hardware/Mechanical/Design/PLASTIC-TEK2-KNOB-INTERFACE/PLASTIC-TEK2-KNOB-INTERFACE.FCStd

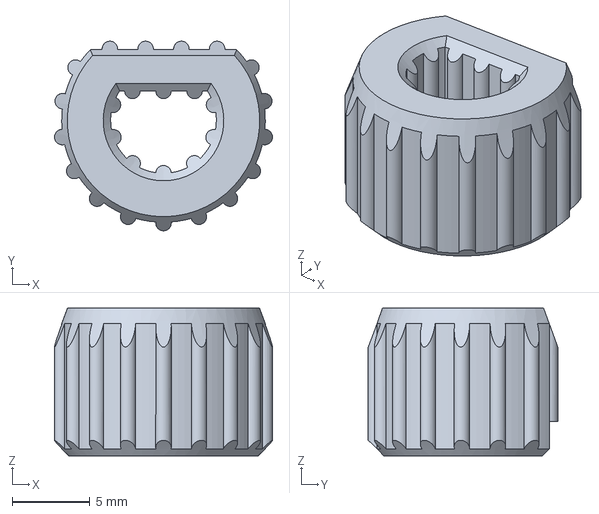
[picture p144: CAD file, 2025-09-30]
Mechanical/Design/PLASTIC-TEK2-KNOB-INTERFACE/PLASTIC-TEK2-KNOB-INTERFACE.FCStd
14.0 x 12.2 x 9.50 mm
