intechstudio/grid-hardware/Mechanical/Design/PLASTIC-VSN-DISPLAY-SPACER/PLASTIC-VSN-DISPLAY-SPACER_1.FCStd

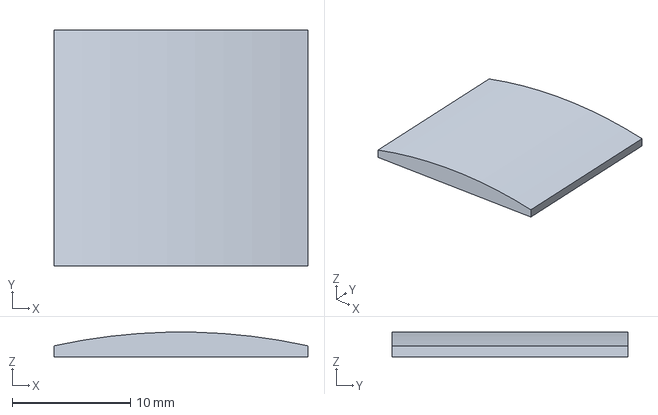
[picture p145: CAD file, 2025-03-20]
Mechanical/Design/PLASTIC-VSN-DISPLAY-SPACER/PLASTIC-VSN-DISPLAY-SPACER_1.FCStd
21.5 x 20.0 x 2.09 mm
