intechstudio/grid-hardware/Mechanical/Experiment/3DFDM_Base/3DFDM_Base.FCStd

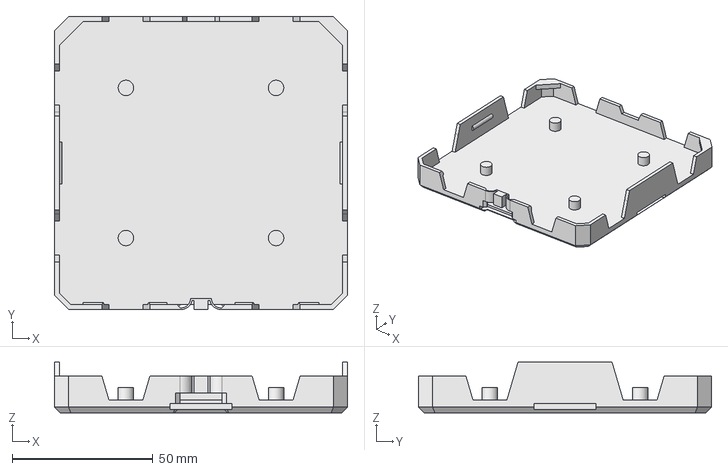
[picture p146: CAD file, 2024-07-18]
Mechanical/Experiment/3DFDM_Base/3DFDM_Base.FCStd
104.1 x 104.1 x 18.0 mm
