intechstudio/grid-hardware/Mechanical/Experiment/DisplayStand/mfg/Stand.stl

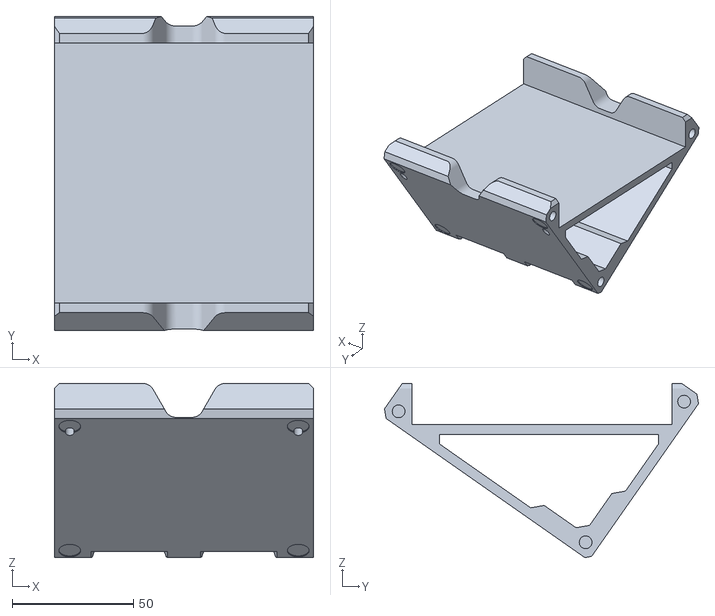
[picture p147: CAD file, 2021-09-23]
Mechanical/Experiment/DisplayStand/mfg/Stand.stl
106.6 x 129.3 x 71.7
