intechstudio/grid-hardware/Mechanical/Experiment/DisplayStand/module_display_stand.FCStd

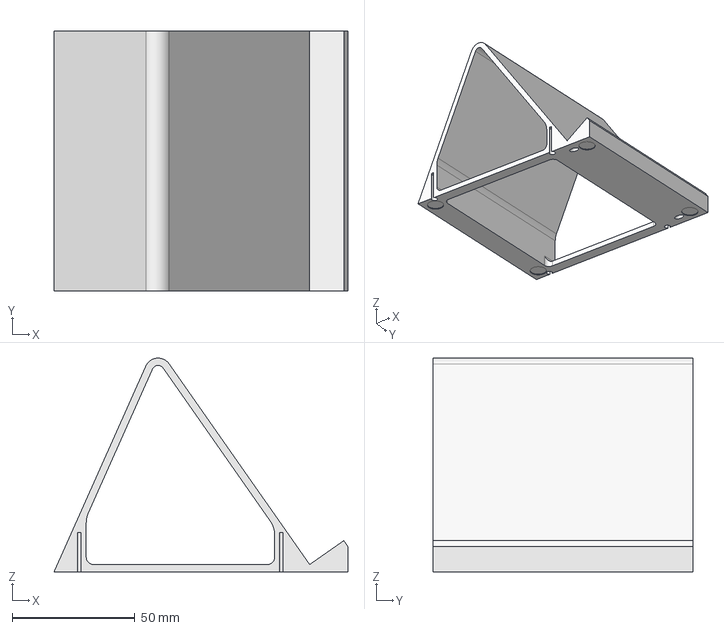
[picture p148: CAD file, 2021-07-14]
Mechanical/Experiment/DisplayStand/module_display_stand.FCStd
120.0 x 106.0 x 87.3 mm
