intechstudio/grid-hardware/Mechanical/Experiment/Eurorack_adapter/wo_button/eurorack_adapter_wo_switch_nominal.FCStd

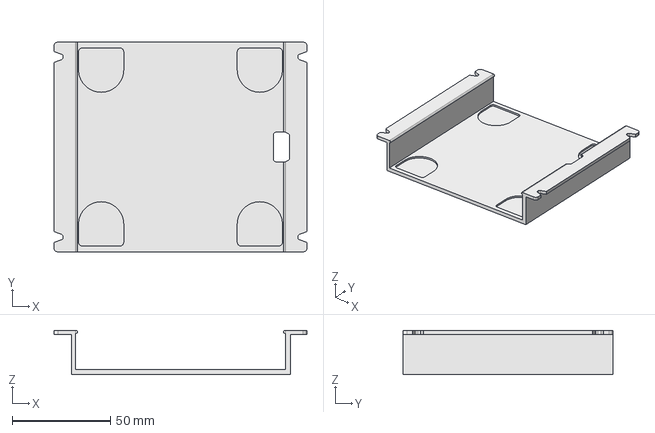
[picture p149: CAD file, 2024-02-26]
Mechanical/Experiment/Eurorack_adapter/wo_button/eurorack_adapter_wo_switch_nominal.FCStd
128.5 x 106.6 x 22.5 mm
