intechstudio/grid-hardware/Mechanical/RK0952N_L-15F-N7-CI.STEP

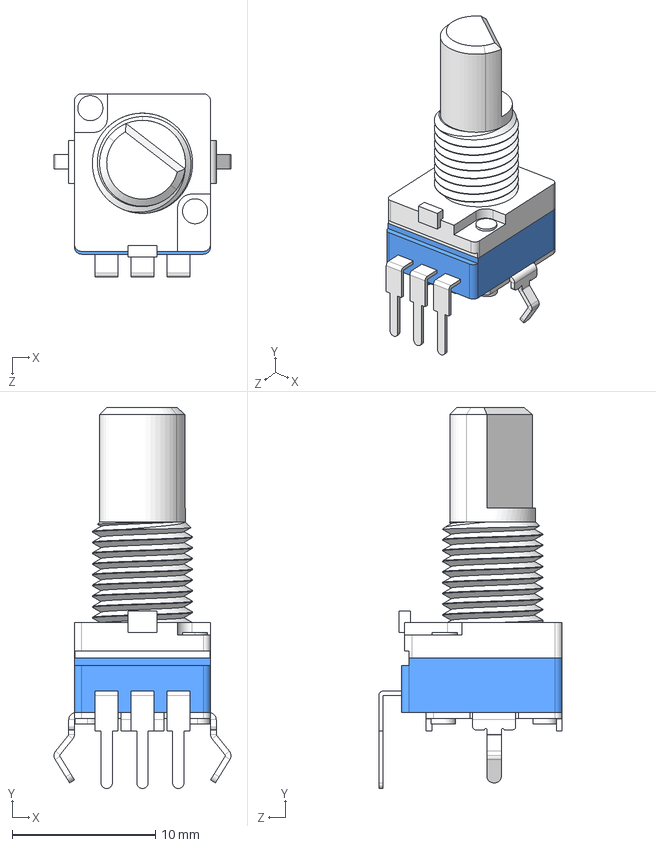
[picture p150: CAD file, 2021-10-26]
Mechanical/RK0952N_L-15F-N7-CI.STEP
12.4 x 26.6 x 12.8 mm
蟯伎
盓殤
粣杶N=7
粣陑15F-N=7
