intechstudio/grid-hardware/Mechanical/Source/curing_rig_3.FCStd

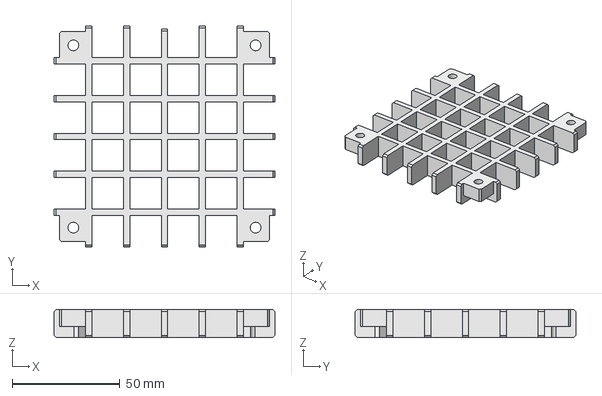
[picture p151: CAD file, 2019-08-26]
Mechanical/Source/curing_rig_3.FCStd
102.6 x 102.6 x 13.0 mm
