intechstudio/grid-hardware/Manufacturing/bushing_jig/concentricity_tool.FCStd

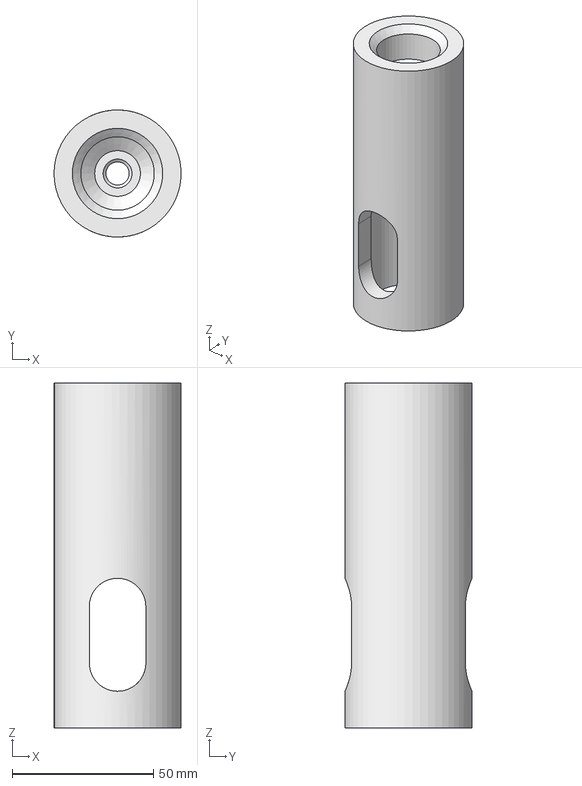
[picture p152: CAD file, 2024-02-26]
Manufacturing/bushing_jig/concentricity_tool.FCStd
45.0 x 45.0 x 122.2 mm
