intechstudio/grid-hardware/Manufacturing/CNC/electrical_socket.FCStd

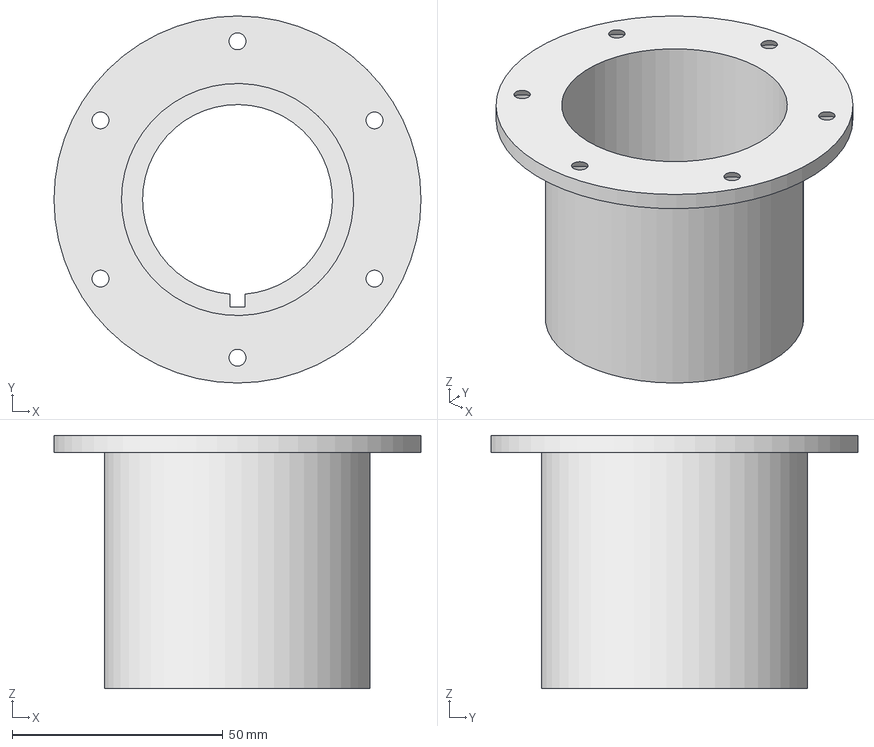
[picture p153: CAD file, 2021-03-19]
Manufacturing/CNC/electrical_socket.FCStd
87.0 x 87.0 x 60.0 mm
