intechstudio/grid-hardware/Manufacturing/CNC/Electronics/cnc_endstop_mount_z.FCStd

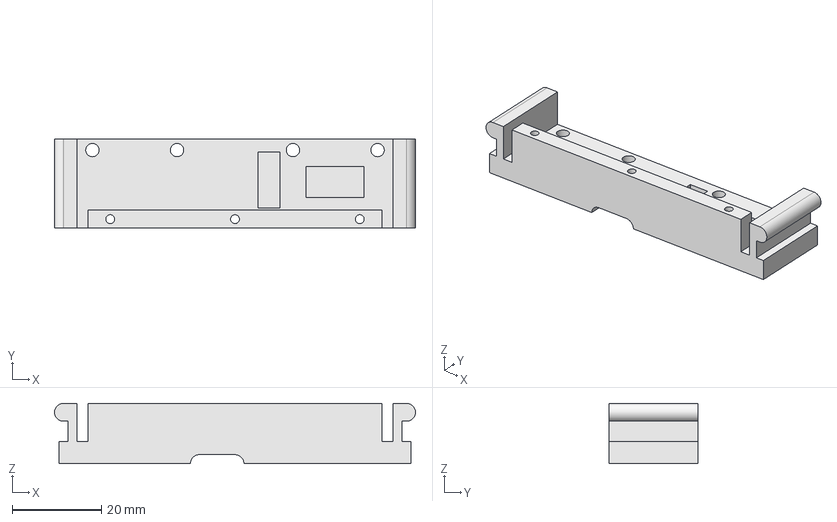
[picture p154: CAD file, 2021-02-25]
Manufacturing/CNC/Electronics/cnc_endstop_mount_z.FCStd
81.0 x 20.0 x 13.5 mm
