intechstudio/grid-hardware/Manufacturing/flatness_QC_jig/digital_indicator_holder_all5.FCStd

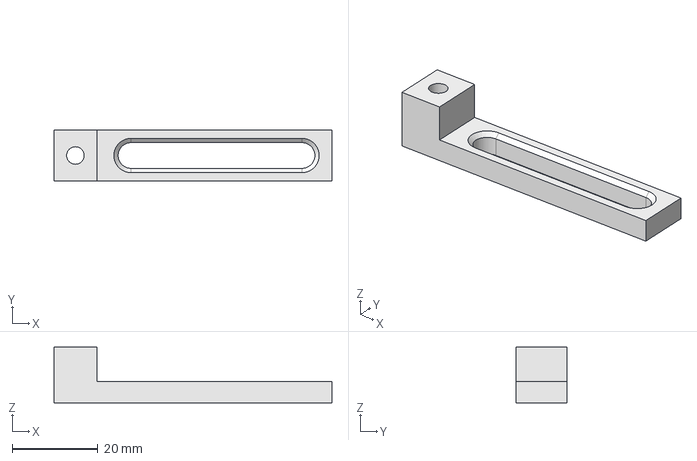
[picture p155: CAD file, 2024-05-15]
Manufacturing/flatness_QC_jig/digital_indicator_holder_all5.FCStd
65.0 x 12.0 x 13.0 mm
