intechstudio/grid-hardware/Manufacturing/Fumefood/fumehood600.FCStd

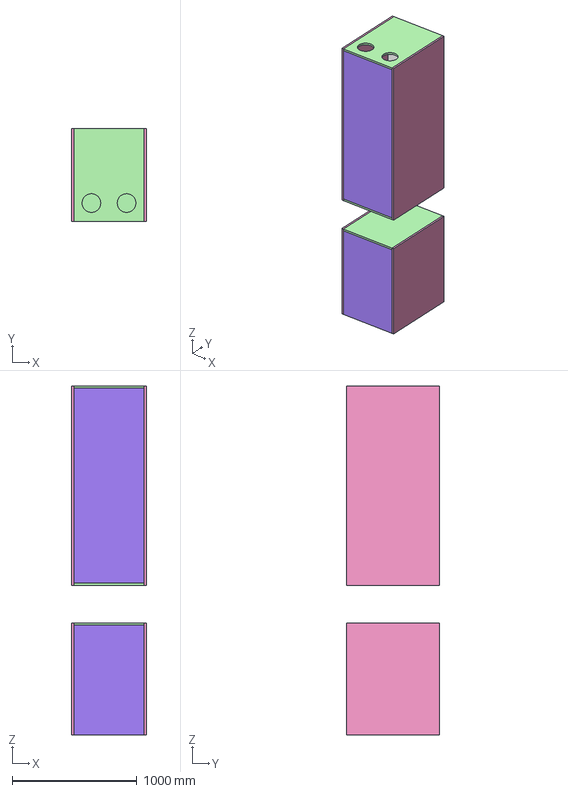
[picture p156: CAD file, 2021-02-25]
Manufacturing/Fumefood/fumehood600.FCStd
600.0 x 750.0 x 2800.0 mm
BackWall
Side1
Side2
Bottom
Front
Window
Rail1
Rail2
ShelfSide1
ShelfSide2
ShelfTop
ShelfBack
ShelfMid1
ShelfMid2
Top001
