intechstudio/grid-hardware/Manufacturing/iroda/router_jig.FCStd

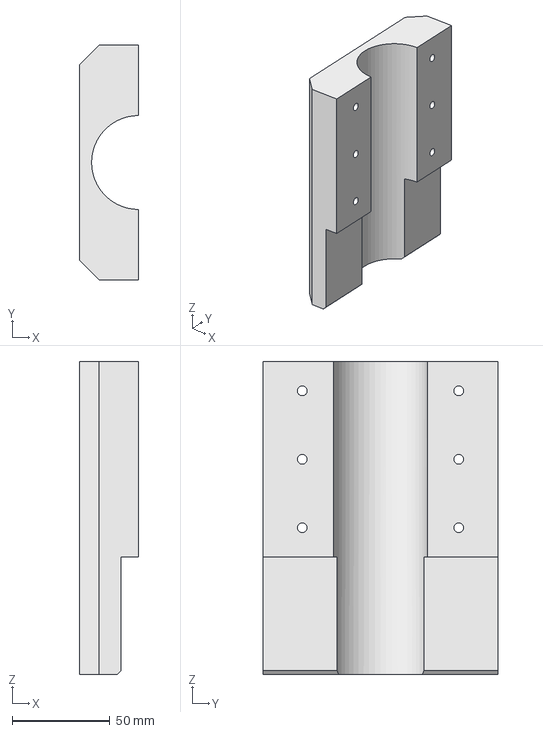
[picture p157: CAD file, 2021-02-25]
Manufacturing/iroda/router_jig.FCStd
30.0 x 120.0 x 160.0 mm
