intechstudio/grid-hardware/Manufacturing/Laser/plotter_pen_holder.FCStd

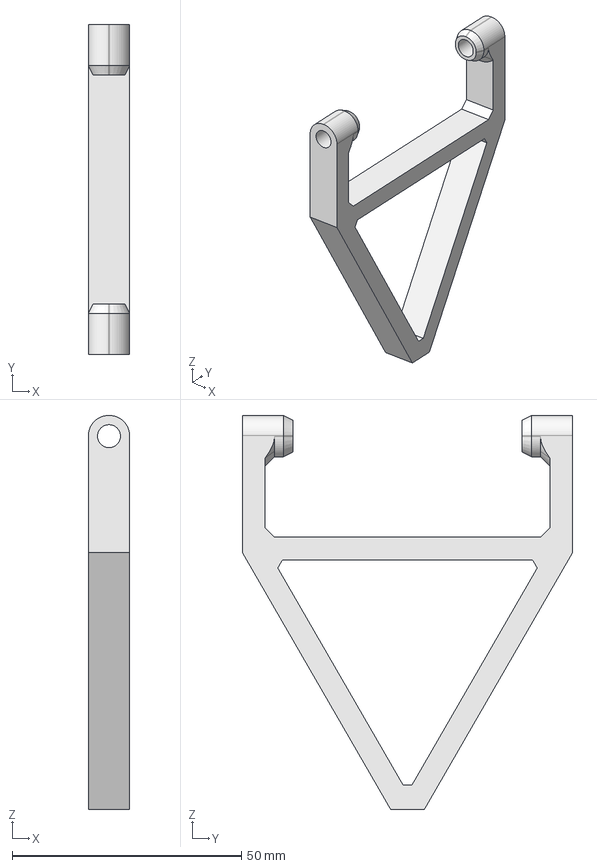
[picture p158: CAD file, 2021-02-25]
Manufacturing/Laser/plotter_pen_holder.FCStd
9.00 x 72.0 x 85.9 mm
