intechstudio/grid-hardware/Manufacturing/Packaging/test3.dxf

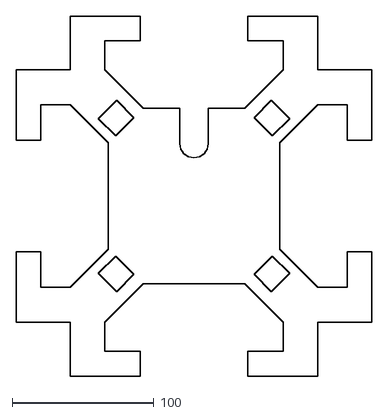
[picture p159: CAD file, 2020-11-30]
Manufacturing/Packaging/test3.dxf
250.7 x 253.7
