intechstudio/grid-hardware/Manufacturing/random_stuff/printer_chamber_door_lock.FCStd

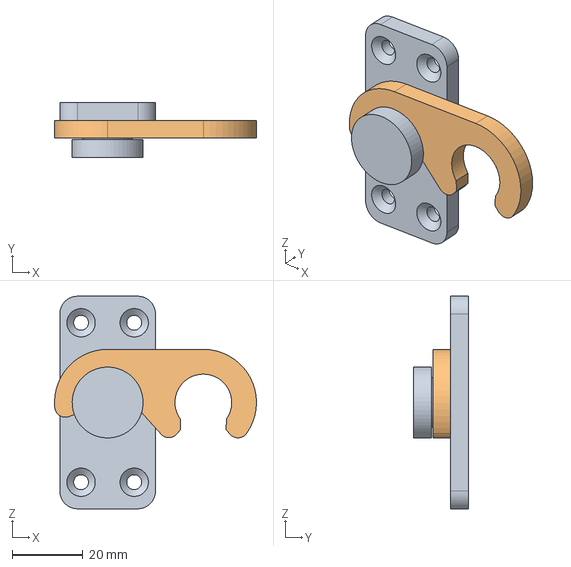
[picture p160: CAD file, 2024-03-14]
Manufacturing/random_stuff/printer_chamber_door_lock.FCStd
57.0 x 15.5 x 60.0 mm
