intechstudio/grid-hardware/Mechanical/Assembly/Components/rubber_dome.FCStd

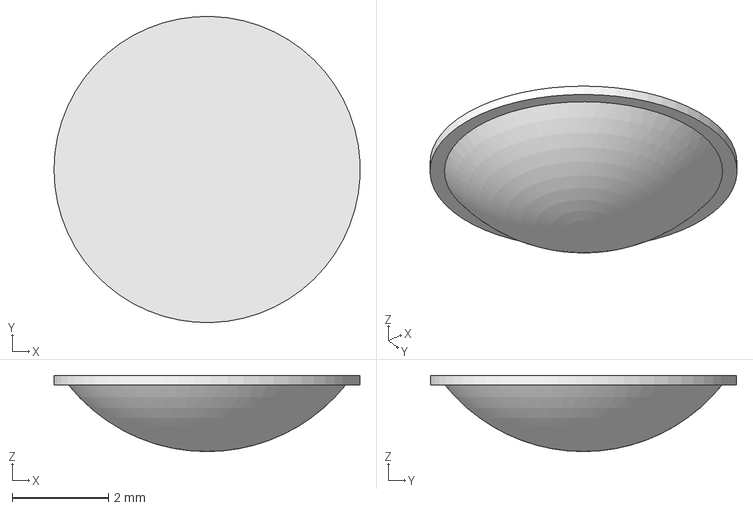
[picture p161: CAD file, 2019-08-26]
Mechanical/Assembly/Components/rubber_dome.FCStd
6.35 x 6.35 x 1.58 mm
