intechstudio/grid-hardware/Mechanical/Assembly/Frontpanels/FRONTPANEL-PBF4.step

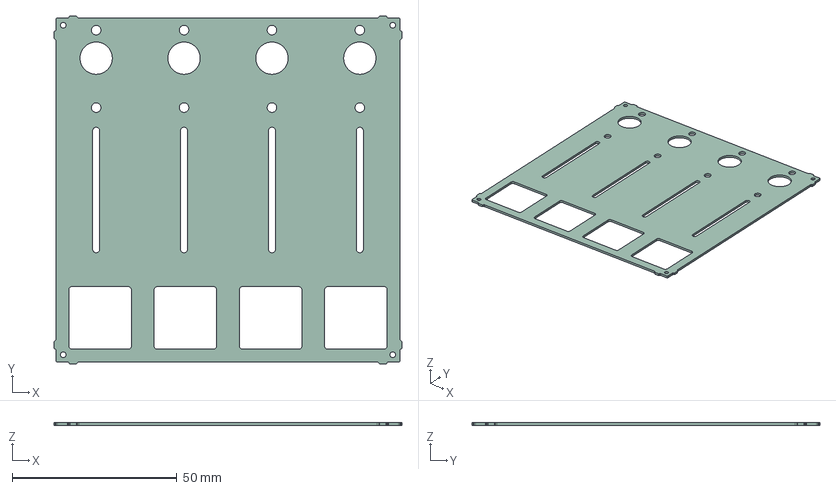
[picture p162: CAD file, 2025-09-02]
Mechanical/Assembly/Frontpanels/FRONTPANEL-PBF4.step
105.6 x 105.6 x 0.91 mm
