intechstudio/grid-hardware/Mechanical/Assembly/PCBAs/PCBA-VSNX.FCStd

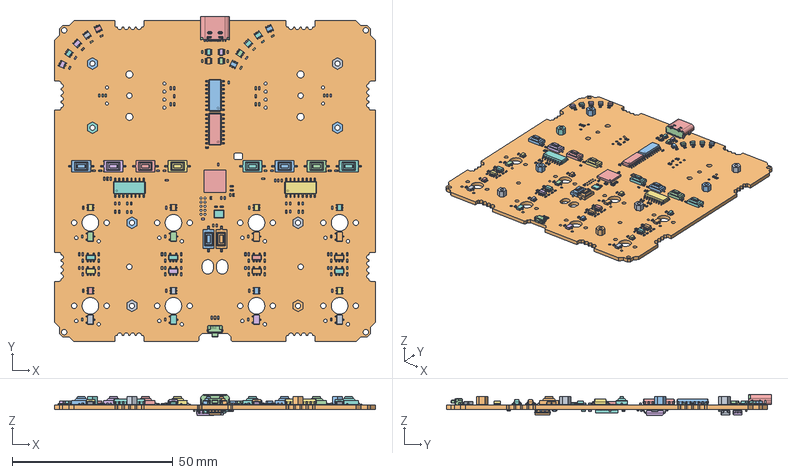
[picture p163: CAD file, 2025-09-30]
Mechanical/Assembly/PCBAs/PCBA-VSNX.FCStd
100.0 x 101.4 x 6.58 mm
LEG003
LEG002
LEG
LEG001
LEG004
LEG005
LEG006
LEG007
LEG008
LEG009
LEG010
LEG011
LEG012
LEG013
LEG014
LEG015
C_0402_1005Metric
C_0402_1005Metric001
C_0402_1005Metric002
C_0402_1005Metric003
C_0402_1005Metric004
C_0402_1005Metric005
R_0402_1005Metric
R_0402_1005Metric001
R_0402_1005Metric002
R_0402_1005Metric003
R_0402_1005Metric004
C_0402_1005Metric006
C_0402_1005Metric007
C_0402_1005Metric008
SOIC-16_3.9x9.9mm_P1.27mm
SOIC-16_3.9x9.9mm_P1.27mm001
R_0402_1005Metric005
R_0402_1005Metric006
R_0402_1005Metric007
R_0402_1005Metric008
C_0402_1005Metric009
C_0402_1005Metric010
C_0402_1005Metric011
C_0402_1005Metric012
C_0402_1005Metric013
C_0402_1005Metric014
C_0402_1005Metric015
C_0402_1005Metric016
R_0402_1005Metric009
R_0402_1005Metric010
R_0402_1005Metric011
R_0402_1005Metric012
C_0402_1005Metric017
C_0402_1005Metric018
C_0402_1005Metric019
SW-SMD_L4.6-W3.5-H1.8-P4.3
SOIC-16_3.9x9.9mm_P1.27mm002
C_0402_1005Metric020
C_0402_1005Metric021
SOT-23-5
SOT-23W
C_0402_1005Metric022
R_0402_1005Metric013
SW_SPST_CK_RS282G05A3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
