intechstudio/grid-hardware/Mechanical/Design/PLASTIC-KNOB-POT/pcba-pot-RK0952N.FCStd

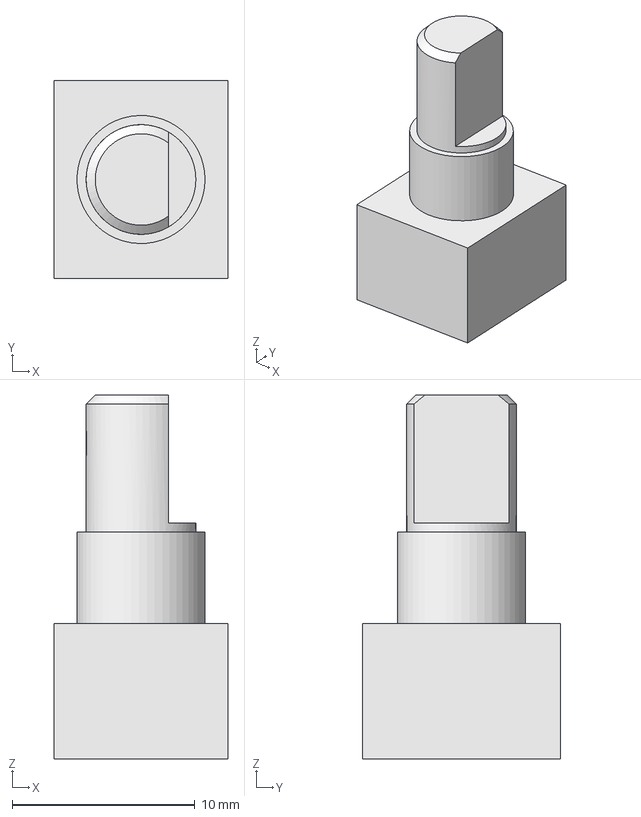
[picture p164: CAD file, 2024-05-31]
Mechanical/Design/PLASTIC-KNOB-POT/pcba-pot-RK0952N.FCStd
9.50 x 10.8 x 19.9 mm
