intechstudio/grid-hardware/Mechanical/Design/PLASTIC-VSN-DISPLAY-SPACER/PLASTIC-VSN-DISPLAY-SPACER_3.FCStd

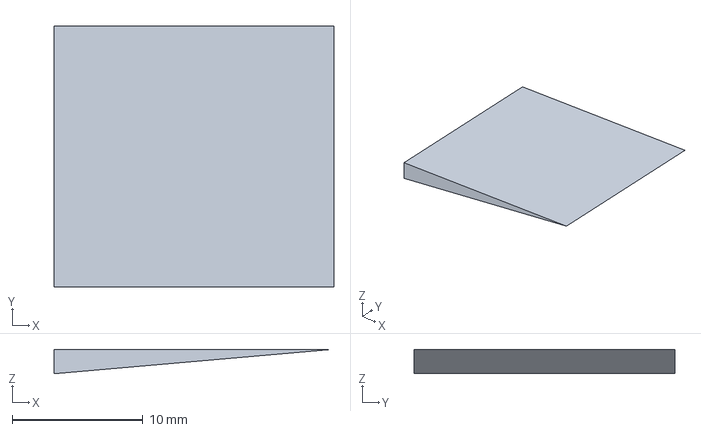
[picture p165: CAD file, 2025-03-20]
Mechanical/Design/PLASTIC-VSN-DISPLAY-SPACER/PLASTIC-VSN-DISPLAY-SPACER_3.FCStd
21.4 x 20.0 x 1.87 mm
