intechstudio/grid-hardware/Mechanical/Experiment/DisplayStand/mfg/Leg.stl

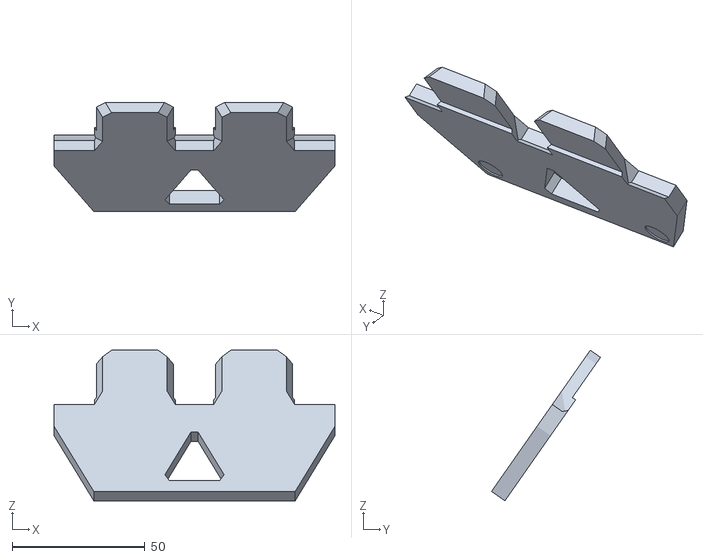
[picture p166: CAD file, 2021-09-07]
Mechanical/Experiment/DisplayStand/mfg/Leg.stl
106.0 x 41.1 x 56.8
