intechstudio/grid-hardware/Mechanical/Assembly/Frontpanel/release/overlay/BU16_SVG.pdf

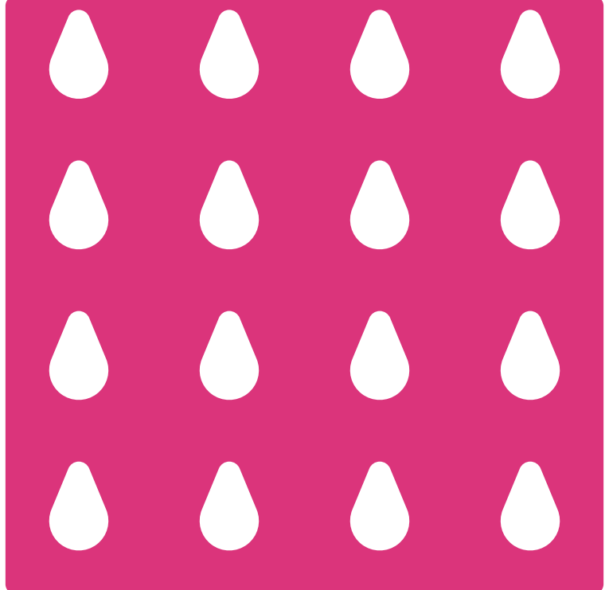
[picture p171: figure]
