intechstudio/grid-hardware/Mechanical/Assembly/Frontpanel/release/overlay/PBF4_SVG.pdf

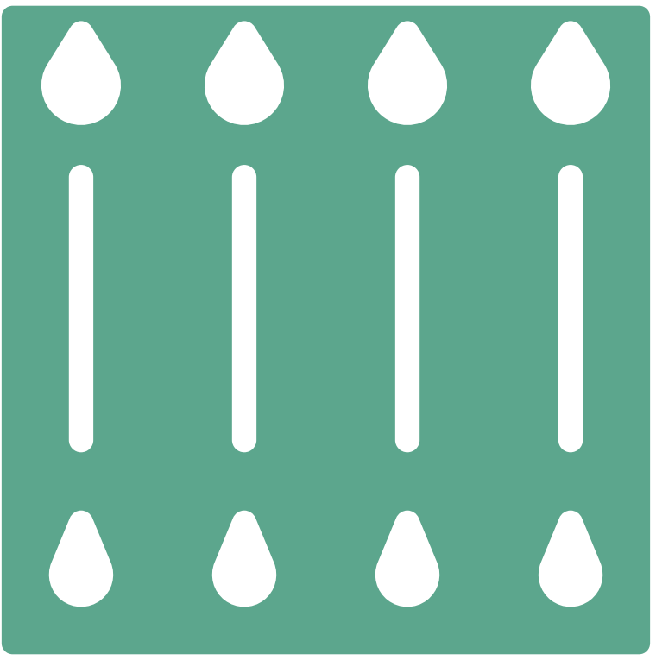
[picture p172: figure]
