intechstudio/grid-hardware/Mechanical/Assembly/Frontpanel/release/overlay/PO16_EN16_SVG.pdf

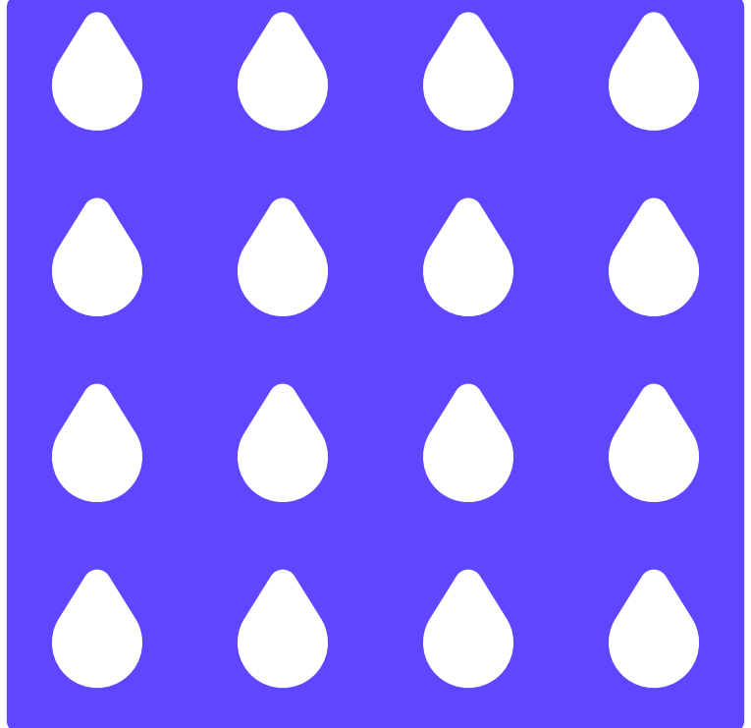
[picture p173: figure]
