intechstudio/grid-hardware/Manufacturing/Fumefood/mfg/asm.png

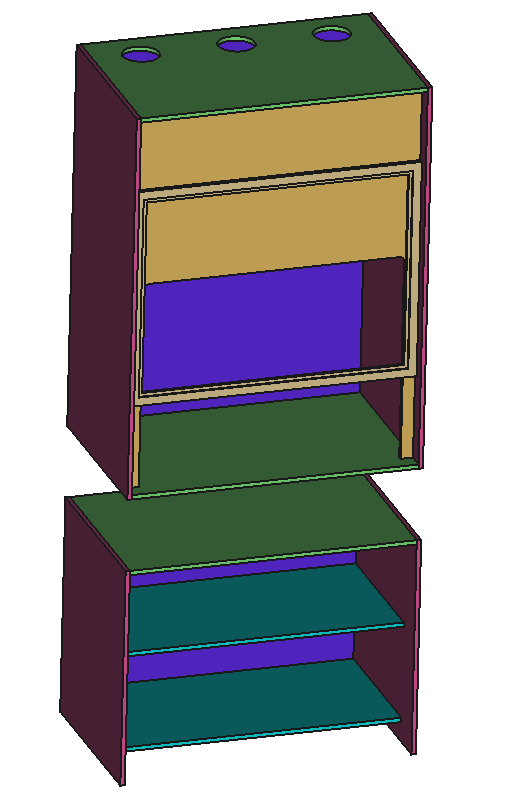
Manufacturing/Fumefood/mfg/asm.png
