intechstudio/grid-hardware/Manufacturing/Fumefood/mfg/szekreny.png

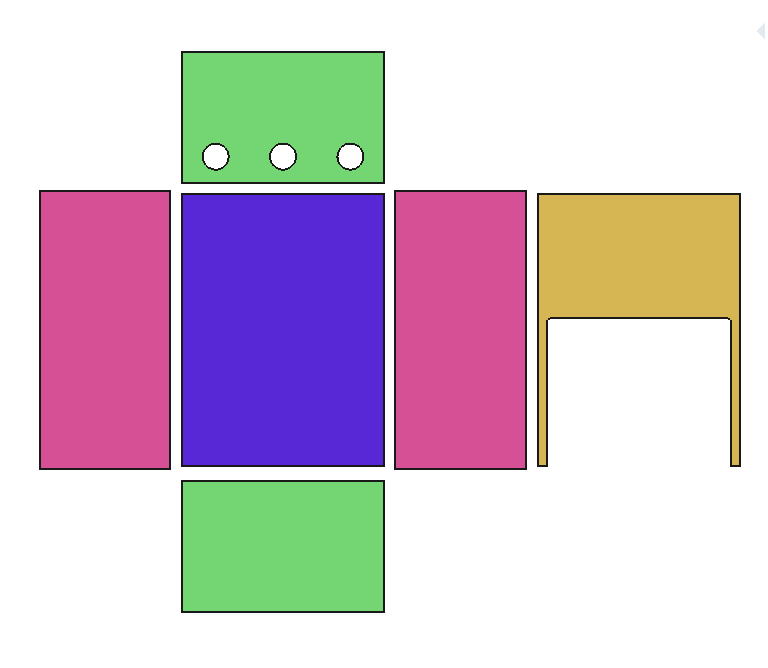
Manufacturing/Fumefood/mfg/szekreny.png
