intechstudio/grid-hardware/Manufacturing/Packaging/quote2/cardboard_insert2.png

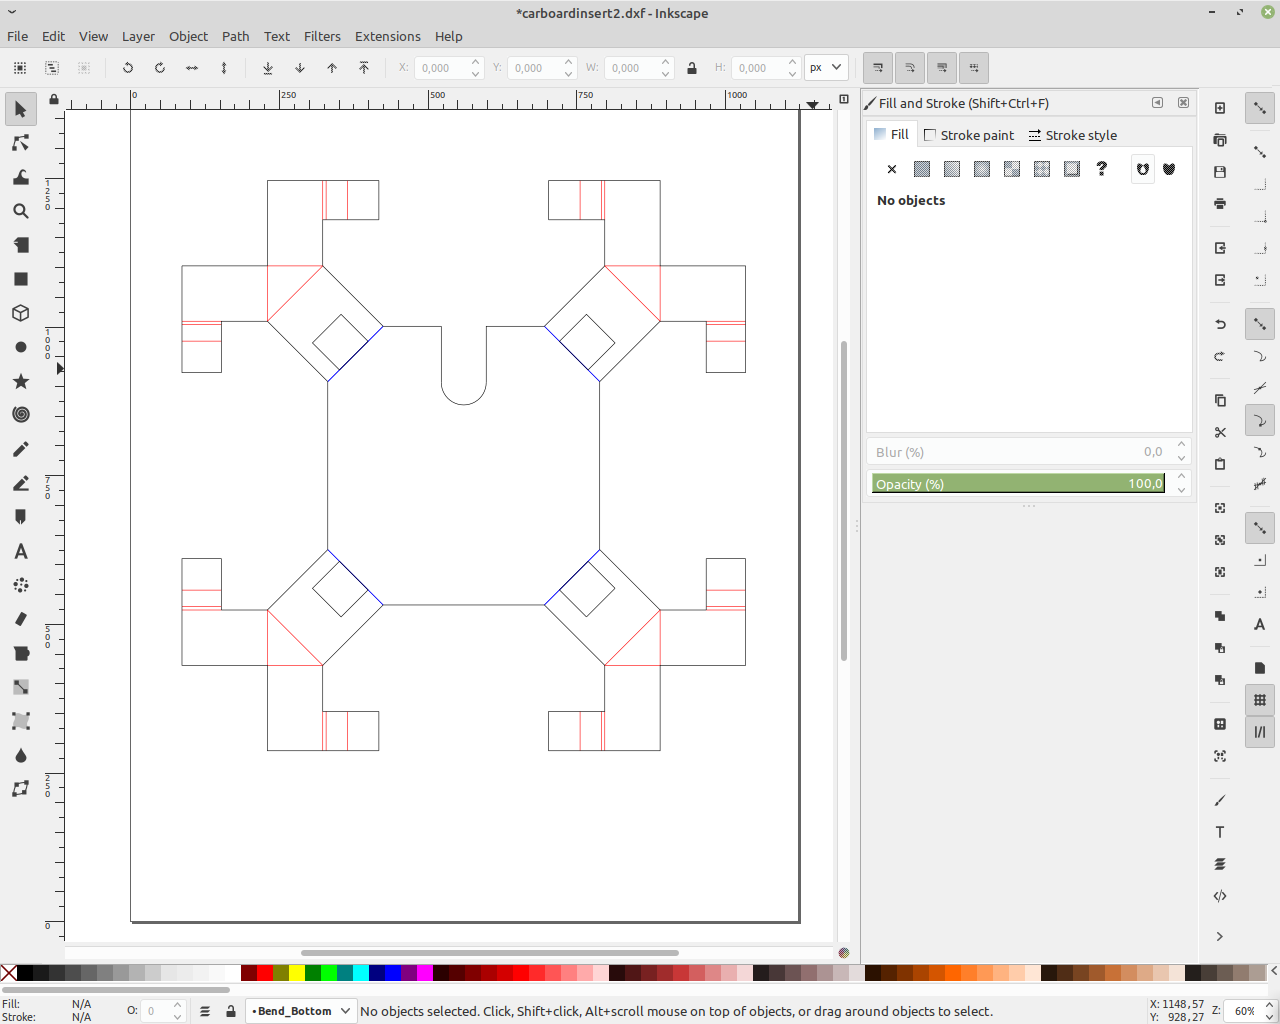
Manufacturing/Packaging/quote2/cardboard_insert2.png
