intechstudio/grid-hardware/Manufacturing/Packaging/quote2/IMAG0441.jpg

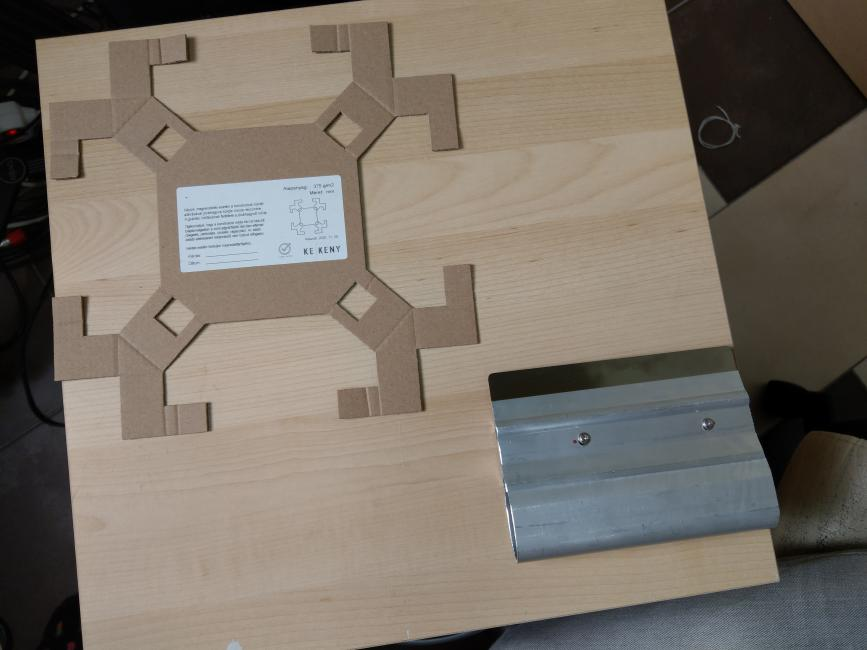
Manufacturing/Packaging/quote2/IMAG0441.jpg
