intechstudio/grid-hardware/Manufacturing/Packaging/quote2/IMAG0442.jpg

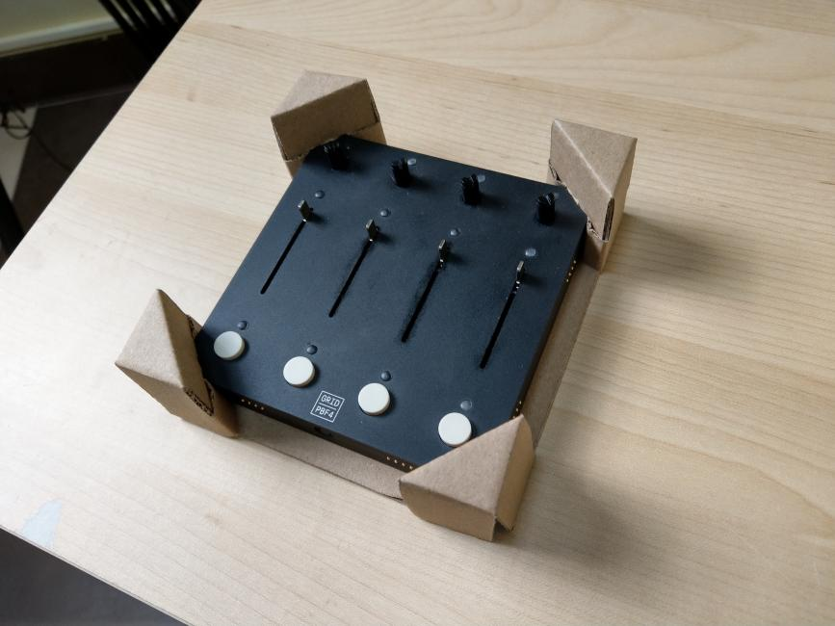
Manufacturing/Packaging/quote2/IMAG0442.jpg
