intechstudio/grid-hardware/Manufacturing/Packaging/quote2/IMAG0443.jpg

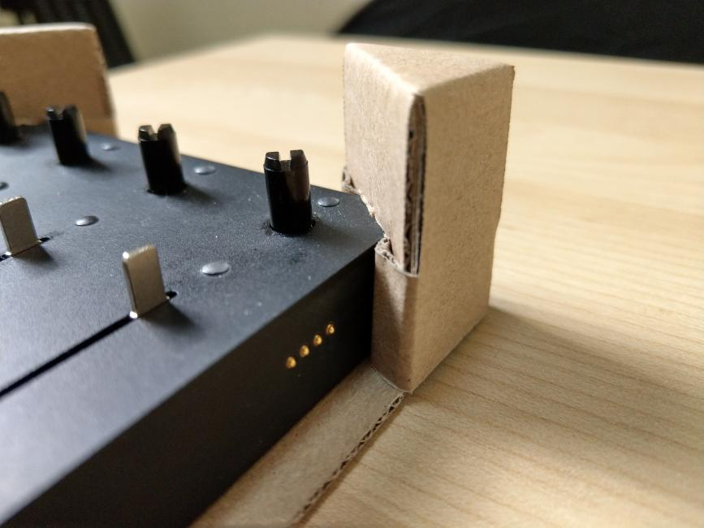
Manufacturing/Packaging/quote2/IMAG0443.jpg
