intechstudio/grid-hardware/Manufacturing/Packaging/quote2/IMAG0446.jpg

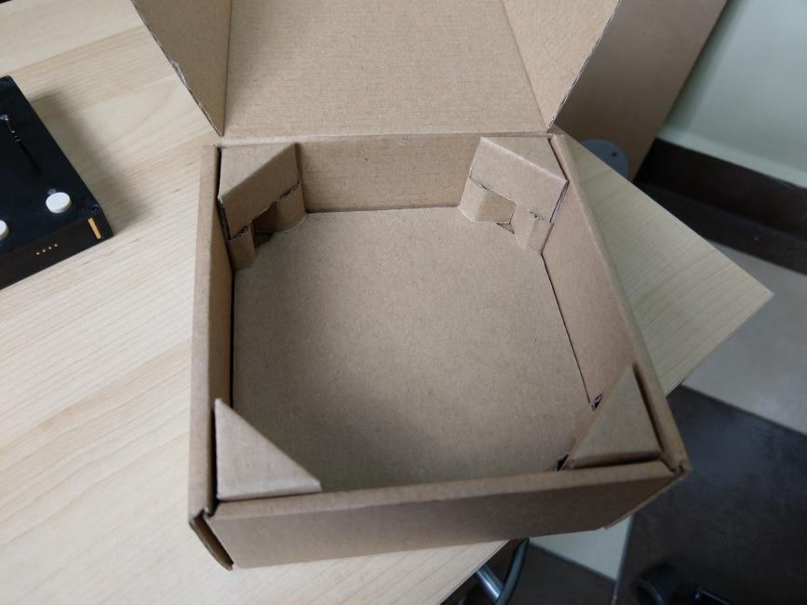
Manufacturing/Packaging/quote2/IMAG0446.jpg
