intechstudio/grid-hardware/Manufacturing/Packaging/quote3/insert3.png

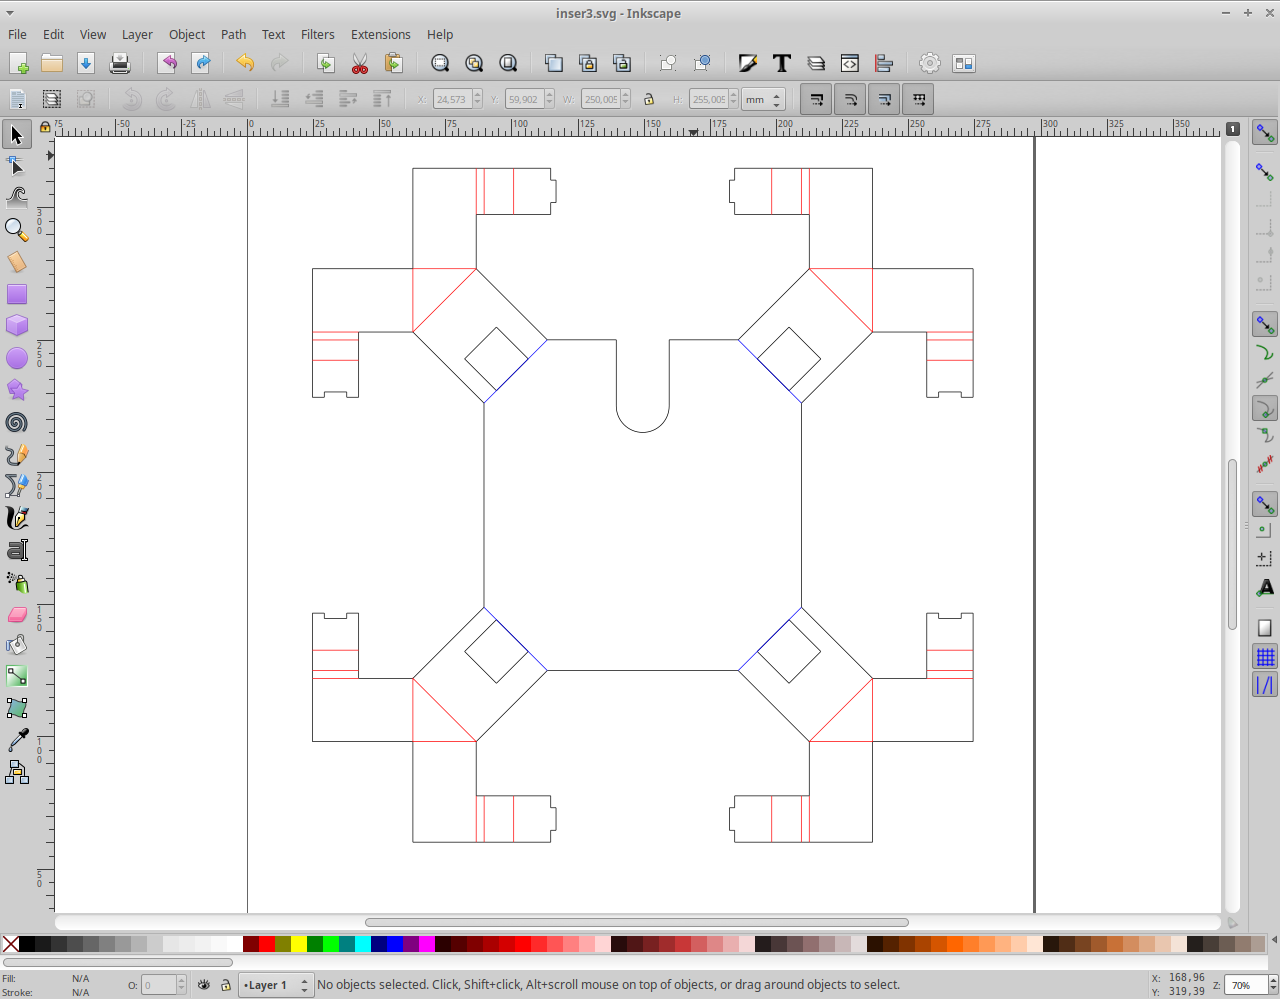
Manufacturing/Packaging/quote3/insert3.png
