intechstudio/grid-hardware/Manufacturing/Potbushing/pot_bushing_crossection.png

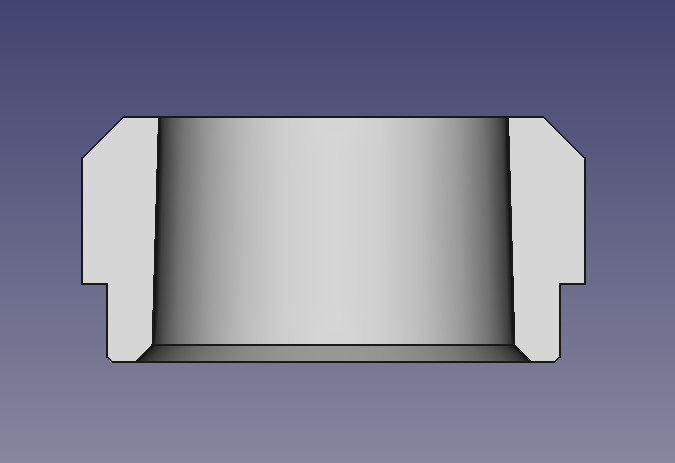
Manufacturing/Potbushing/pot_bushing_crossection.png
