intechstudio/grid-hardware/Manufacturing/Potbushing/pot_bushing_preview.png

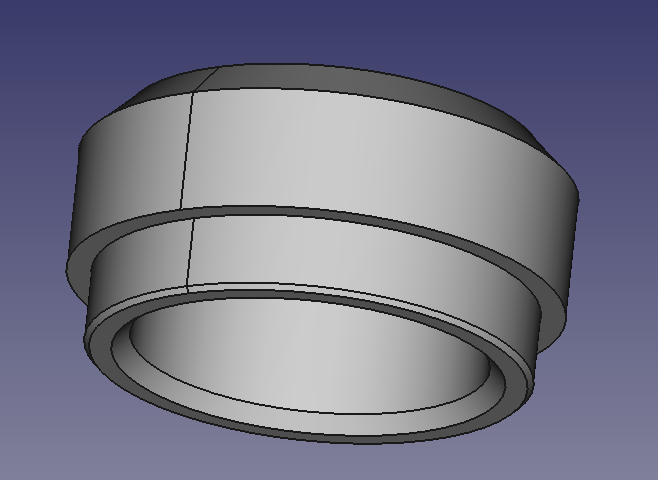
Manufacturing/Potbushing/pot_bushing_preview.png
