intechstudio/grid-hardware/Mechanical/Experiment/DisplayStand/mfg/slicer-pin.png

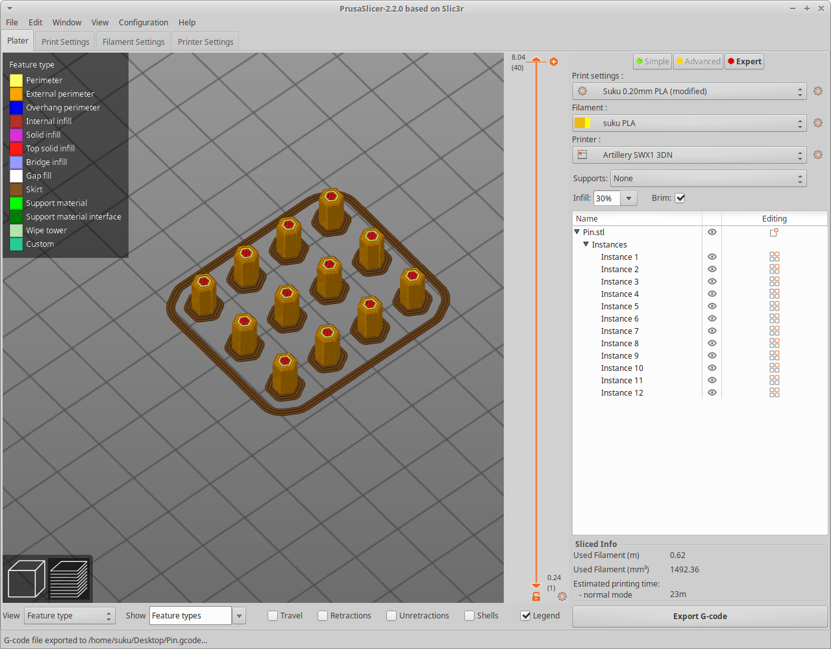
Mechanical/Experiment/DisplayStand/mfg/slicer-pin.png
