intechstudio/grid-hardware/Mechanical/Experiment/DisplayStand/mfg/slicer_leg.png

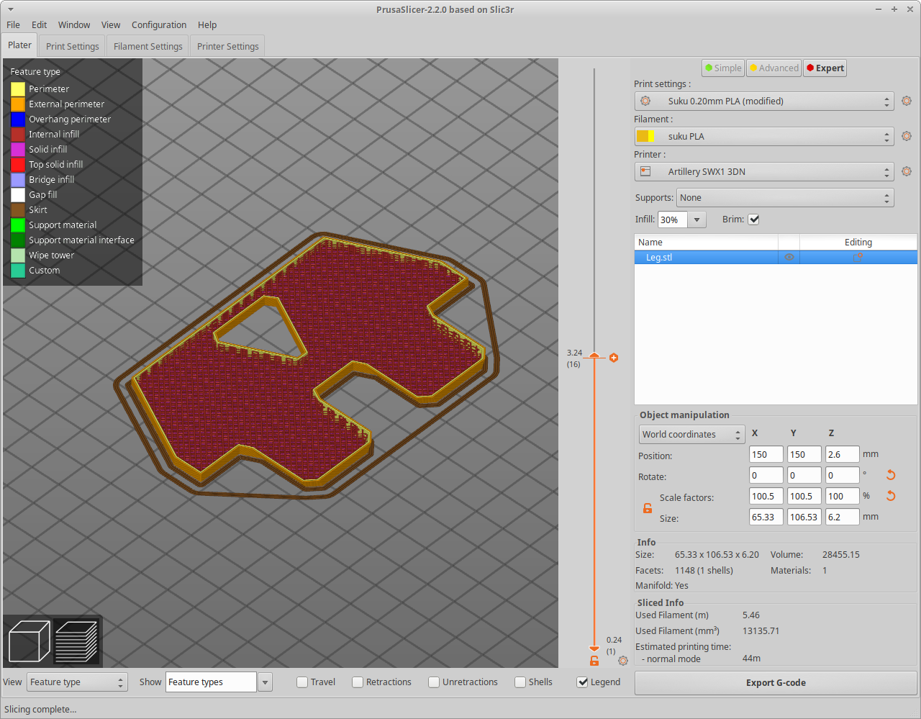
Mechanical/Experiment/DisplayStand/mfg/slicer_leg.png
