intechstudio/grid-hardware/Mechanical/Experiment/DisplayStand/mfg/slicer_stand.png

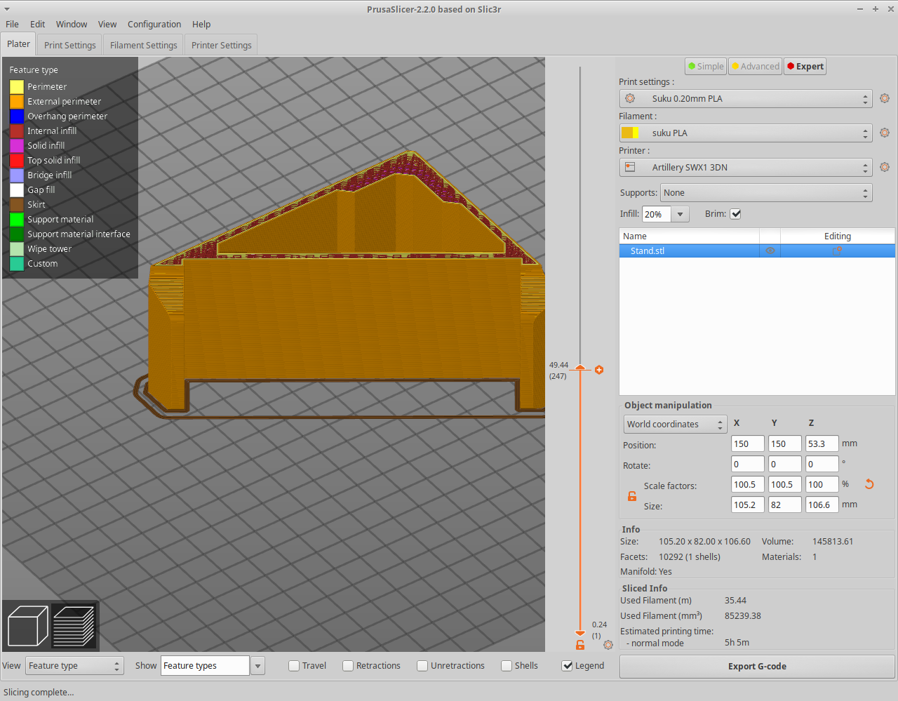
Mechanical/Experiment/DisplayStand/mfg/slicer_stand.png
