intechstudio/grid-hardware/Packaging/PACKAGING-SLEEVE-BU16.pdf

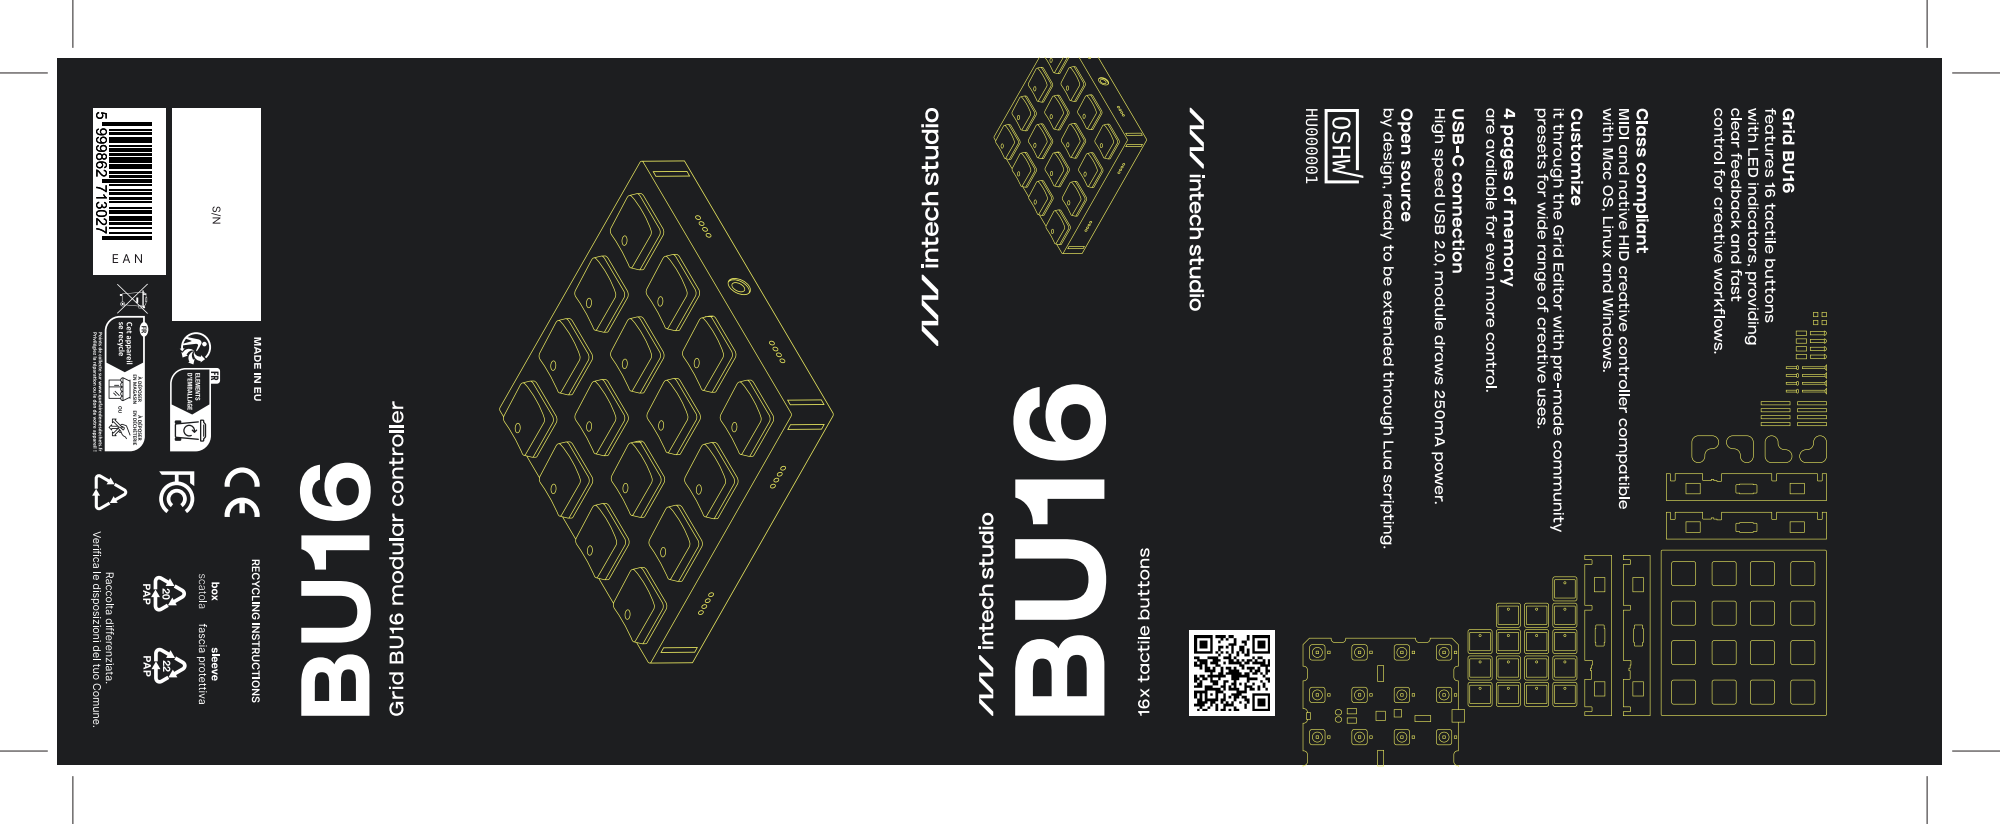
[picture p193: page 1]
