intechstudio/grid-hardware/Packaging/PACKAGING-SLEEVE-EF44.pdf

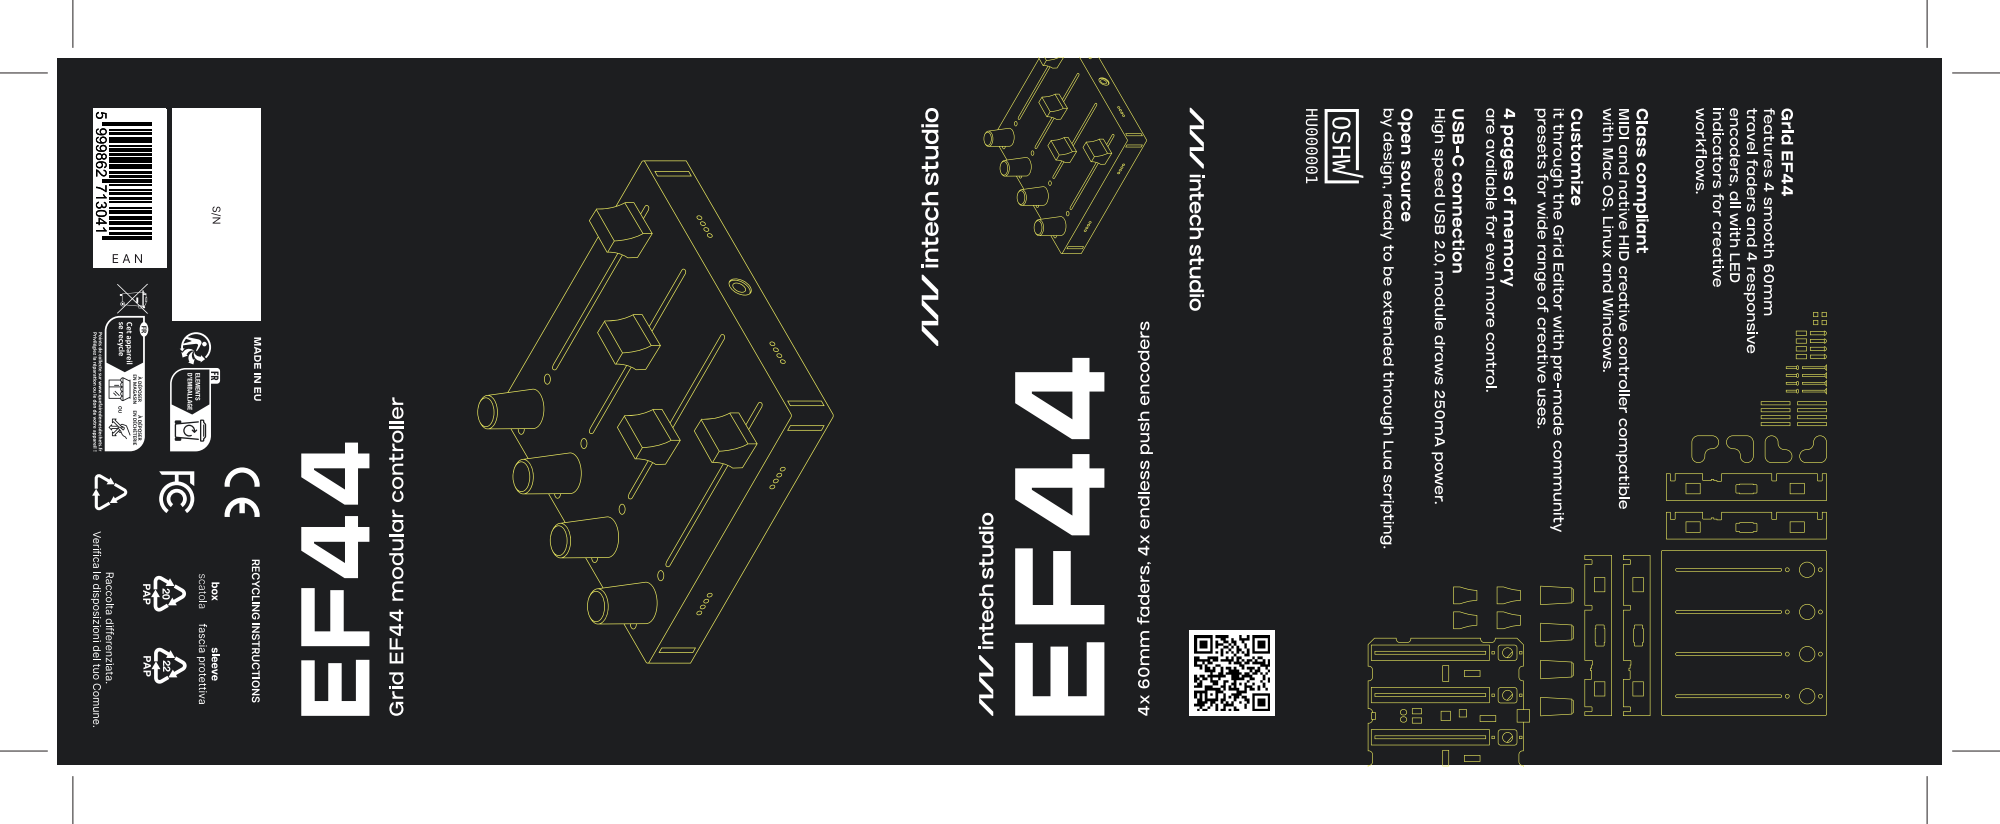
[picture p194: page 1]
