intechstudio/grid-hardware/Packaging/PACKAGING-SLEEVE-EN16.pdf

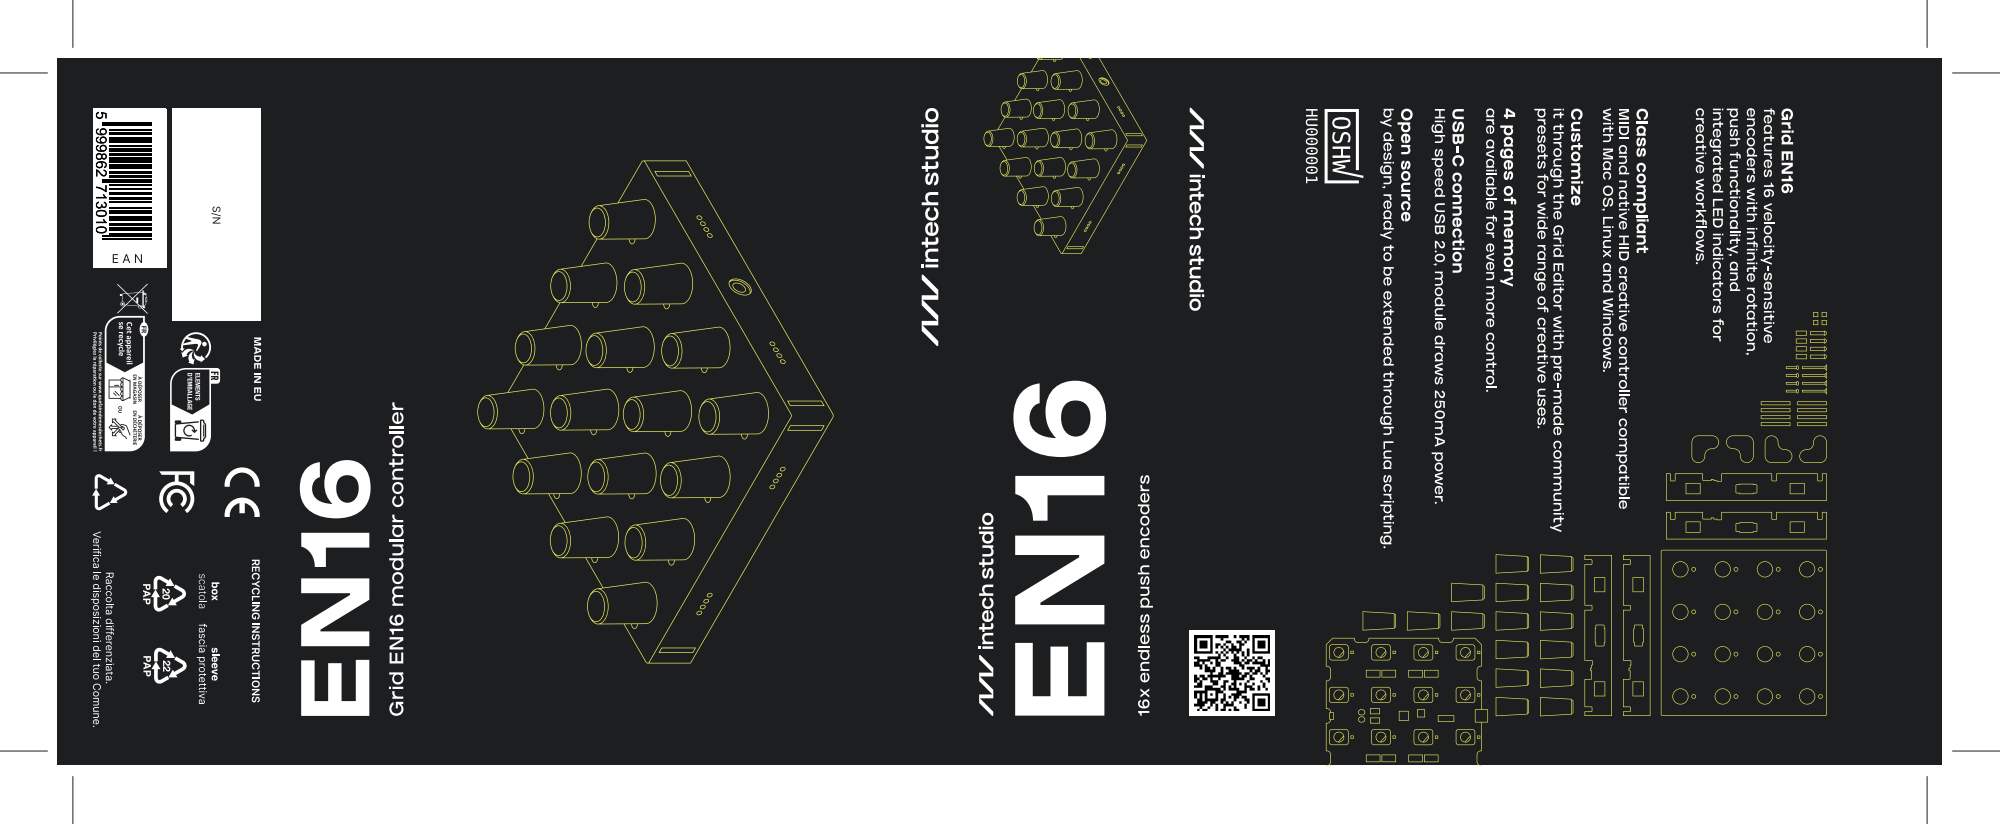
[picture p195: page 1]
