intechstudio/grid-hardware/Packaging/PACKAGING-SLEEVE-PBF4.pdf

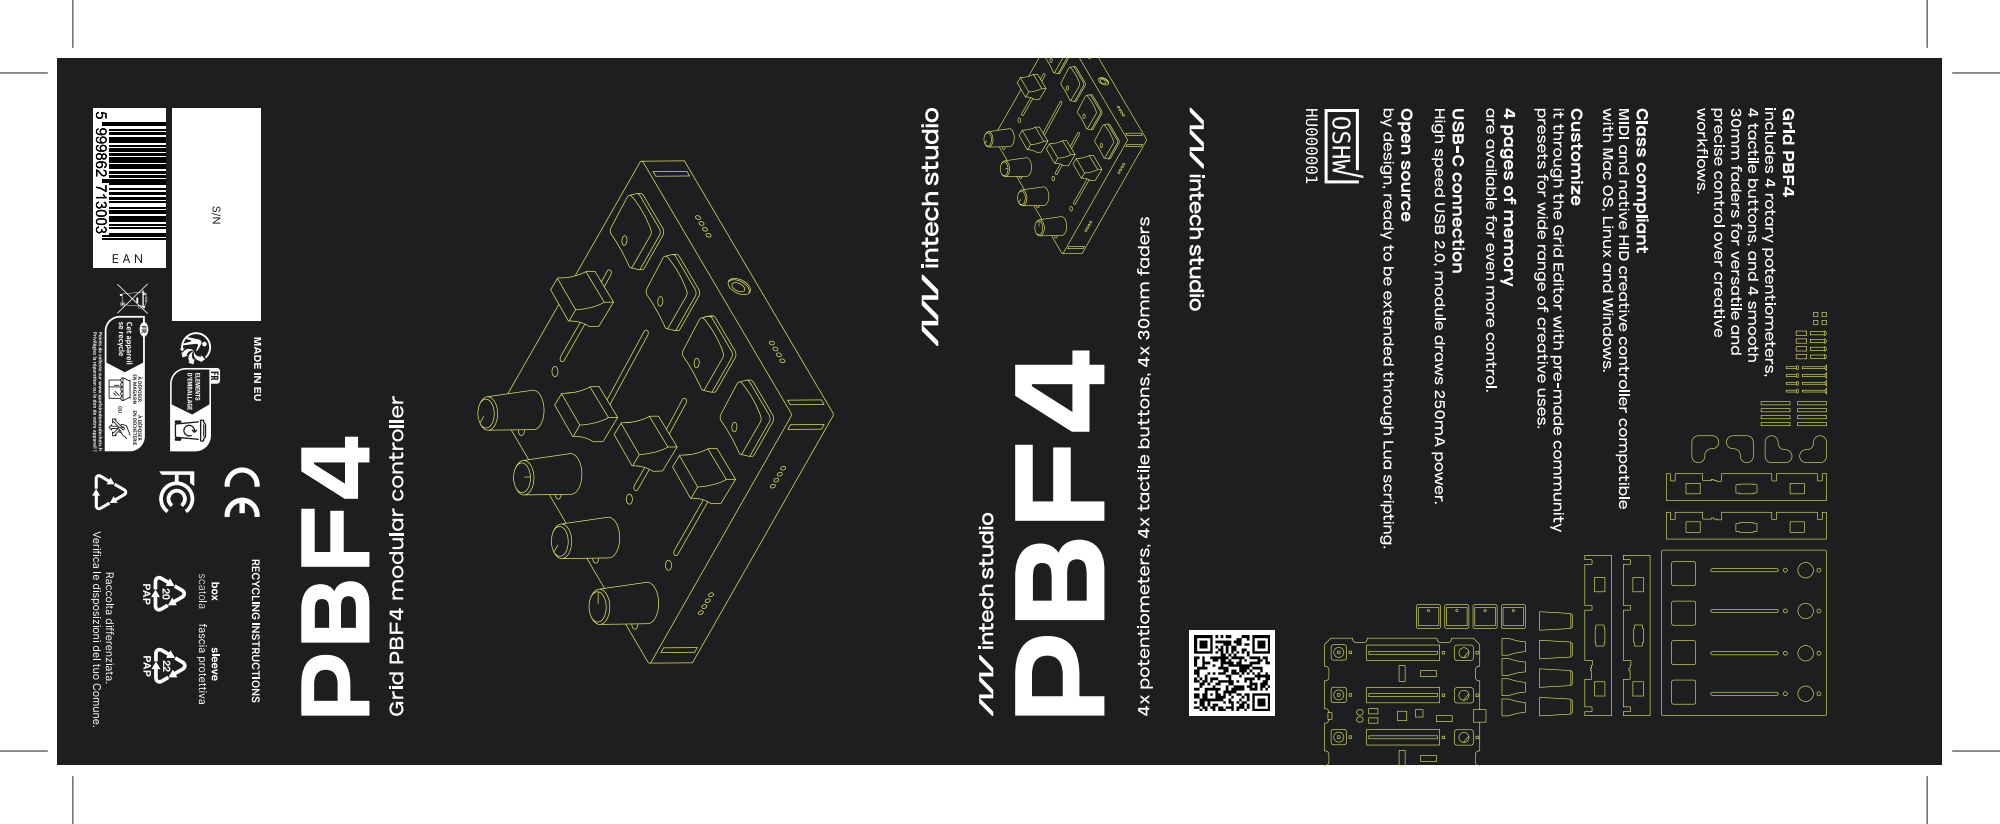
[picture p196: page 1]
