intechstudio/grid-hardware/Packaging/PACKAGING-SLEEVE-PO16.pdf

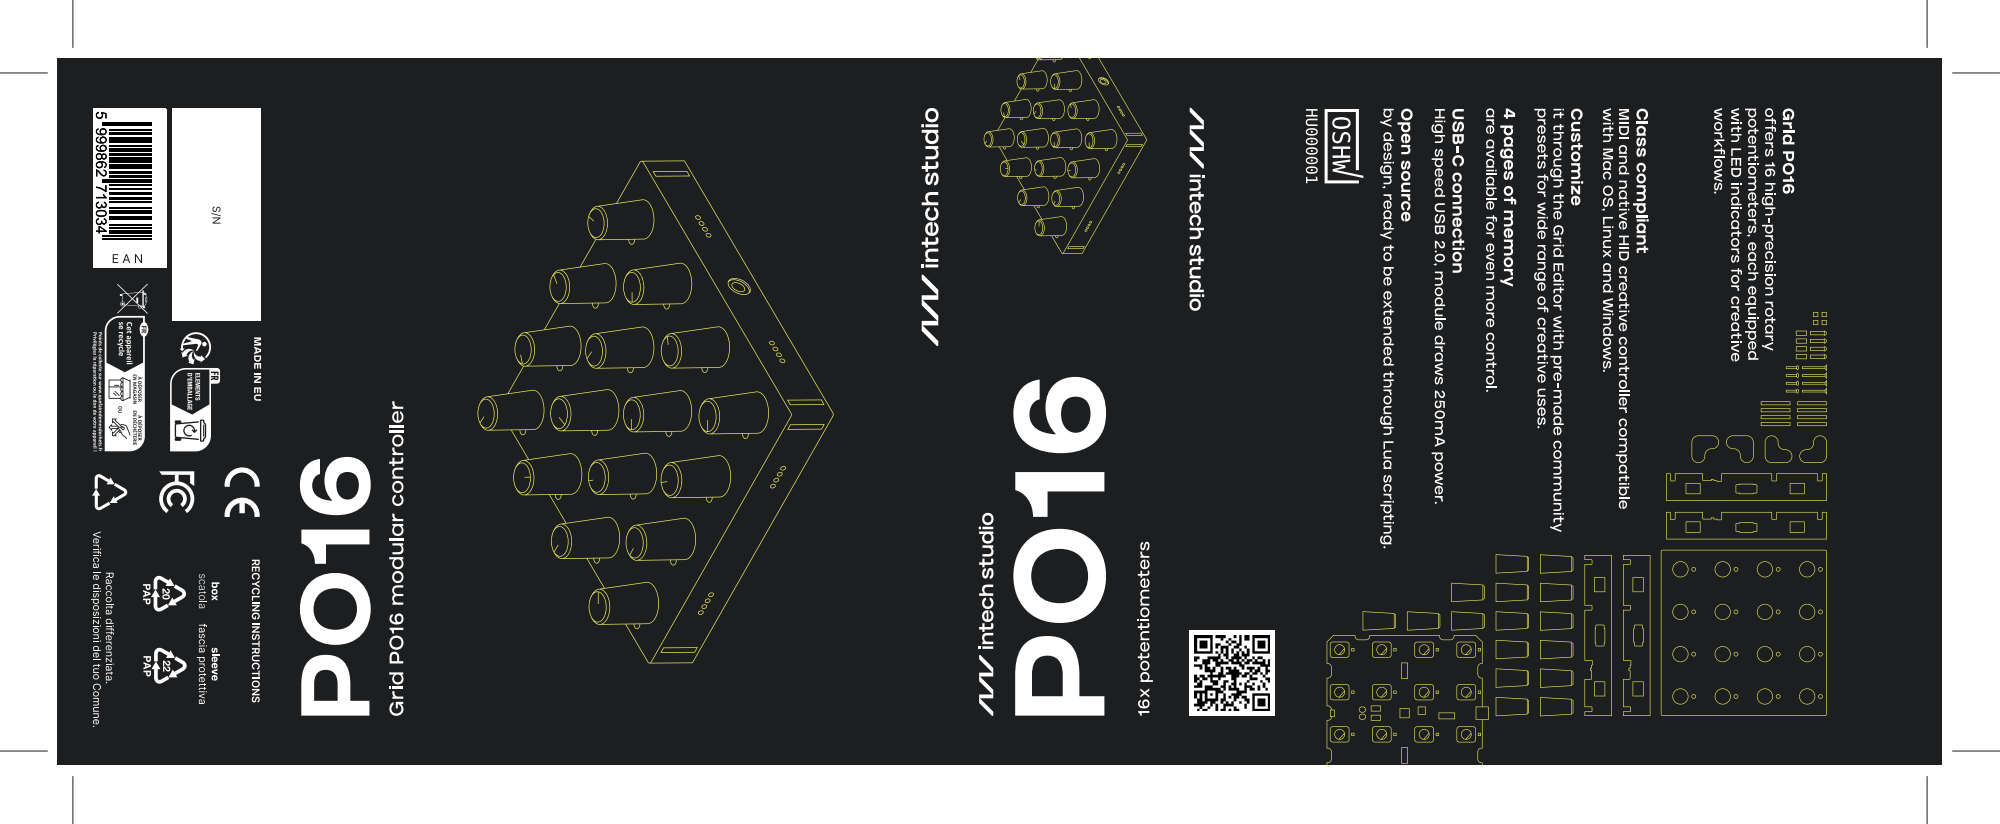
[picture p197: page 1]
