intechstudio/grid-hardware/Packaging/PACKAGING-SLEEVE-TEK2.pdf

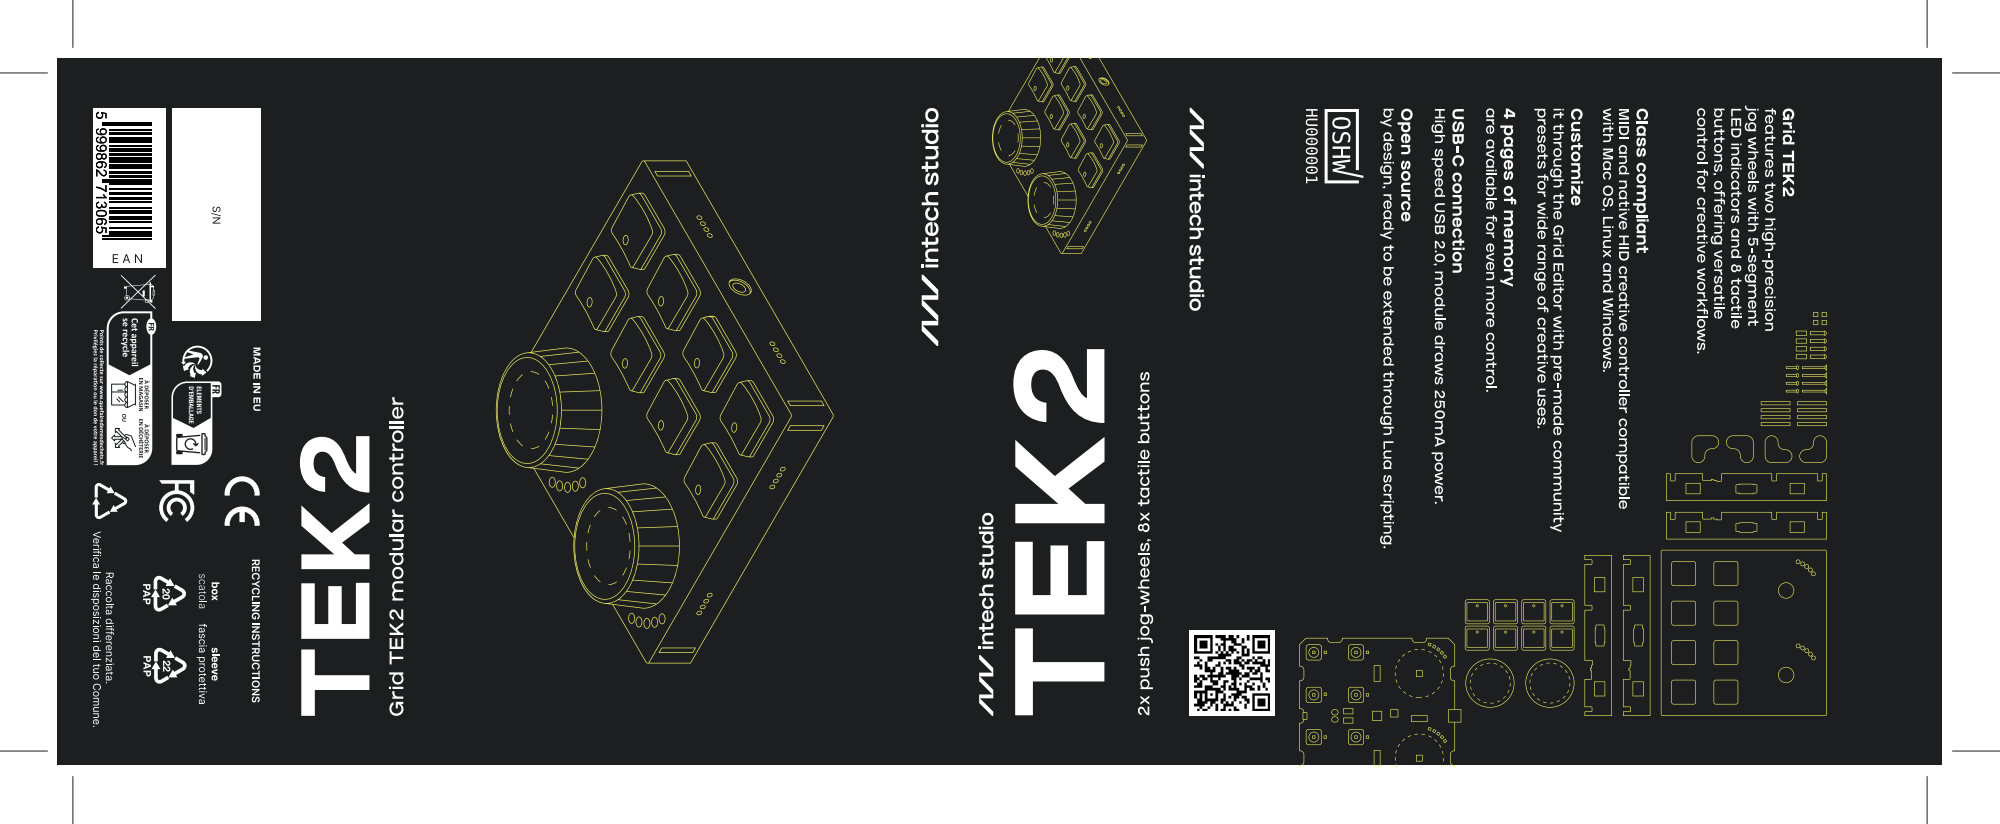
[picture p198: page 1]
