intechstudio/grid-hardware/Packaging/PACKAGING-SLEEVE-VSN1-L.pdf

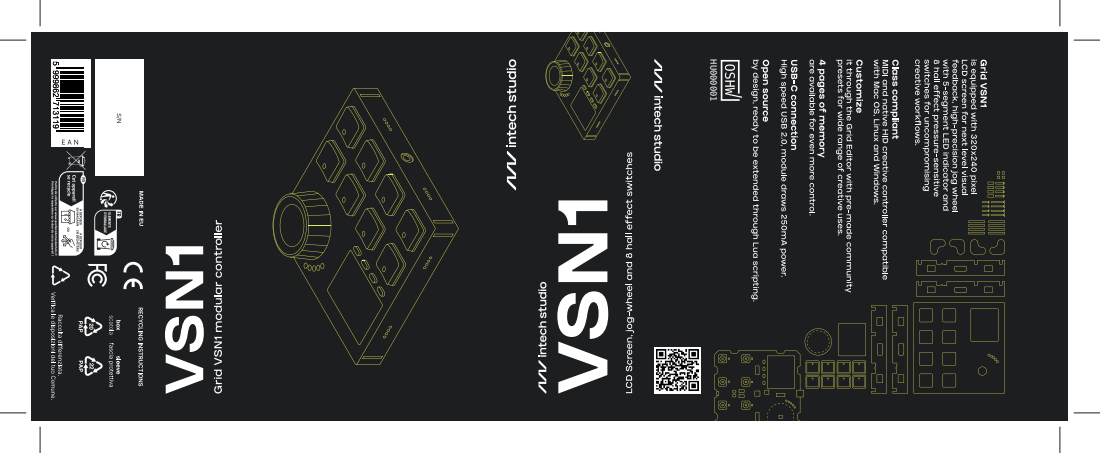
[picture p199: page 1]
