intechstudio/grid-hardware/Packaging/PACKAGING-SLEEVE-VSN1-R.pdf

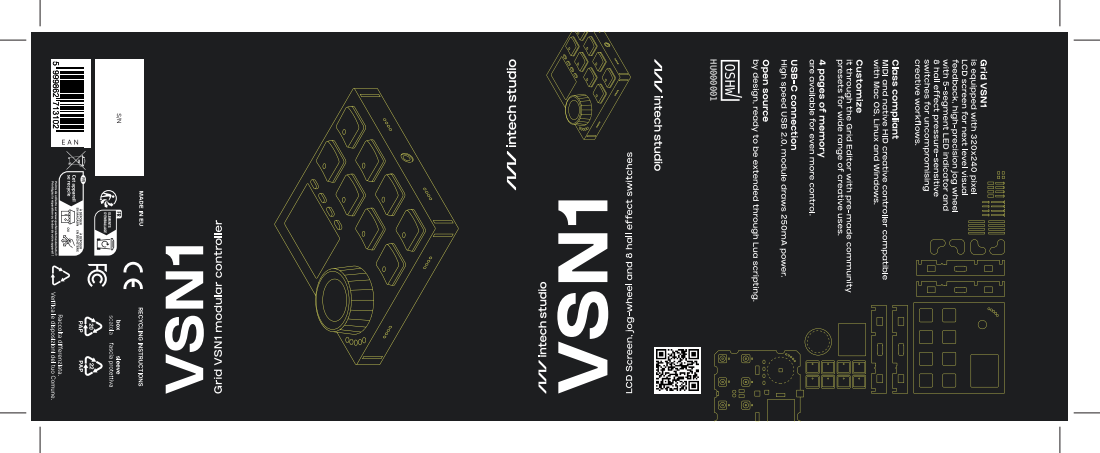
[picture p200: page 1]
