intechstudio/grid-hardware/Packaging/PACKAGING-USB-CABLE.pdf

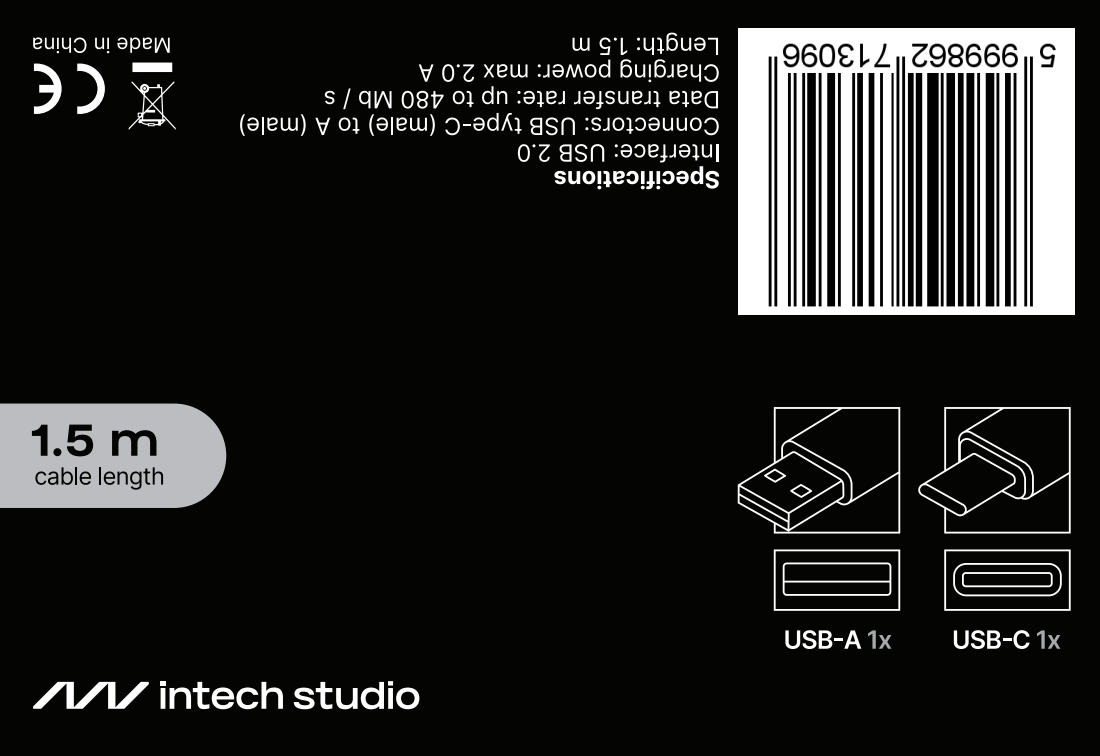
[picture p201: page 1]
