intechstudio/grid-hardware/Mechanical/Design/archive/reference_THT-ENC.pdf

® 松 暉 電 機 工 業 股 份 有 限 公 司 S O N G H U E I E L E C T R I C C O . , L T D .

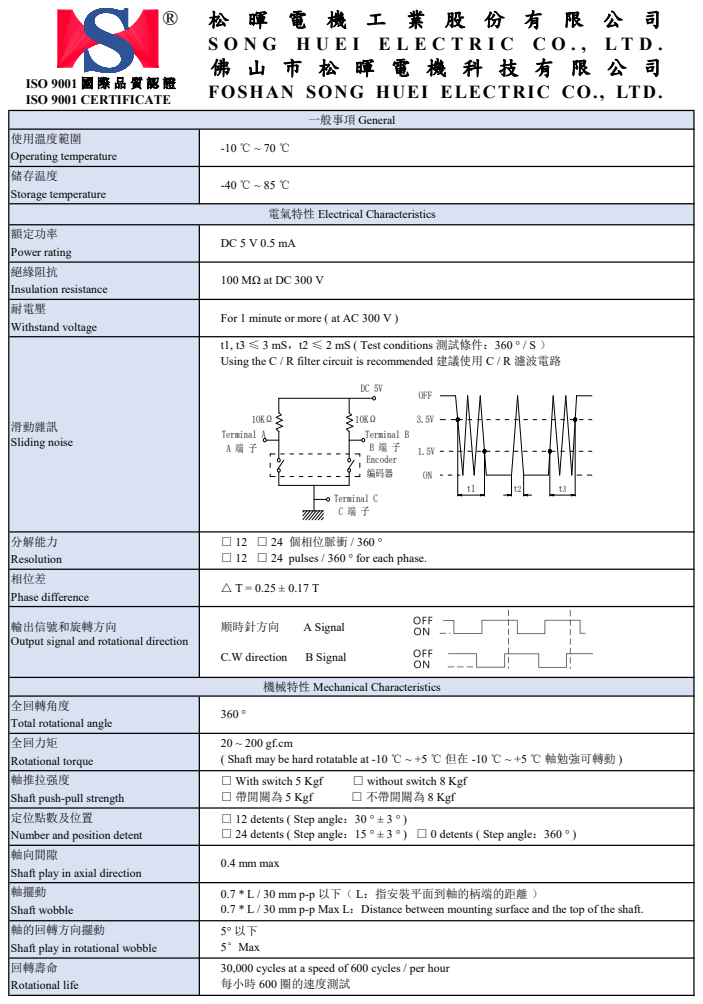
[picture p202: page 1]
一般事項 General; ISO 9001 國 際 品 質 認 證 ISO 9001 CERTIFICATE; Terminal C C 端 子; Terminal A A 端 子; Terminal B B 端 子; Encoder; 编码器

FOSHAN SONG HUEI ELECTRIC CO., LTD.

使用溫度範圍 Operating temperature | -10 ℃ ~ 70 ℃

储存温度 Storage temperature | -40 ℃ ~ 85 ℃

電氣特性 Electrical Characteristics

額定功率 Power rating | DC 5 V 0.5 mA

絕緣阻抗 Insulation resistance | 100 MΩ at DC 300 V

耐電壓 Withstand voltage | For 1 minute or more ( at AC 300 V )

滑動雜訊 Sliding noise | t1, t3 ≤ 3 mS，t2 ≤ 2 mS ( Test conditions 測試條件：360 ° / S ） Using the C / R filter circuit is recommended 建議使用 C / R 濾波電路 | DC 5V OFF

分解能力 Resolution | □ 12 □ 24 個相位脈衝 / 360 ° □ 12 □ 24 pulses / 360 ° for each phase.

相位差 Phase difference | △ T = 0.25 ± 0.17 T

輸出信號和旋轉方向 Output signal and rotational direction | 顺時針方向 A Signal C.W direction B Signal

機械特性 Mechanical Characteristics

全回轉角度 Total rotational angle | 360 °

全回力矩 Rotational torque | 20 ~ 200 gf.cm ( Shaft may be hard rotatable at -10 ℃ ~ +5 ℃ 但在 -10 ℃ ~ +5 ℃ 軸勉強可轉動 )

軸推拉强度 Shaft pushpull strength | □ With switch 5 Kgf □ without switch 8 Kgf □ 帶開關為 5 Kgf □ 不帶開關為 8 Kgf

定位點數及位置 Number and position detent | □ 12 detents ( Step angle：30 ° ± 3 ° ) □ 24 detents ( Step angle：15 ° ± 3 ° ) □ 0 detents ( Step angle：360 ° )

軸向間隙 Shaft play in axial direction | 0.4 mm max

軸擺動 Shaft wobble | 0.7 * L / 30 mm pp 以下（ L：指安裝平面到軸的柄端的距離 ） 0.7 * L / 30 mm pp Max L：Distance between mounting surface and the top of the shaft.

軸的回轉方向擺動 Shaft play in rotational wobble | 5° 以下 5°Max

回轉壽命 Rotational life | 30,000 cycles at a speed of 600 cycles / per hour 每小時 600 圈的速度測試

ISO 9001 國 際 品 質 認 證
ISO 9001 CERTIFICATE
® | 松 暉 電 機 工 業 股 份 有 限 公 司 S O N G H U E I E L E C T R I C C O . , L T D . 佛 山 市 松 暉 電 機 科 技 有 限 公 司 FOSHAN SONG HUEI ELECTRIC CO., LTD.
| 手焊：300 ℃ 以下, 3 秒以內. 自動或半自動機台焊錫條件：預熱:基板表面溫度 100 ℃ 以下, 時間 1分以內, 過錫爐：260 ± 5 ℃ 3 ~ 5 秒 Manual soldering： less than 300 ℃ and within 3 seconds. For automated or semiautomated soldering equipments： Preheating：surface temperature of board：less than 100 ℃ and within 1 min. Auto soldering：260 ± 5 ℃ for 3 ~ 5 seconds.

Note 注明：當產品無帶開關結構時，以上推動開關規格整項取消 Note：When product without switch structure, the above switch specifications are cancelled.

推動開關規格 Pushon Switch Specific Ations

焊錫耐熱性
Resistance to soldering heat
開關電路 Switch circuit | Single pole and single throw ( push on ) 單極單投 ( 推動 )
開關工作行程 Switch travel (mm) | 0.4 0.5 -0.3 mm
開關作動力 Switch operating force | -200 500 200 gf.cm
開關額定功率 Switch rating power | DC 5 V 10 mA
開關接觸阻抗 Switch contact resistance | 第一個週期：100 mΩ, 在有效的壽命範圍結束後 200 mΩ First period 100 mΩ ; 200 mΩ after the end of useful life is reached
開關按壓壽命 Switch push life | 20,000 cycles ( 500 cycles / H, shaft push load 1 kgf max ; 按壓力 1 kg 以下, 500 次 / H )

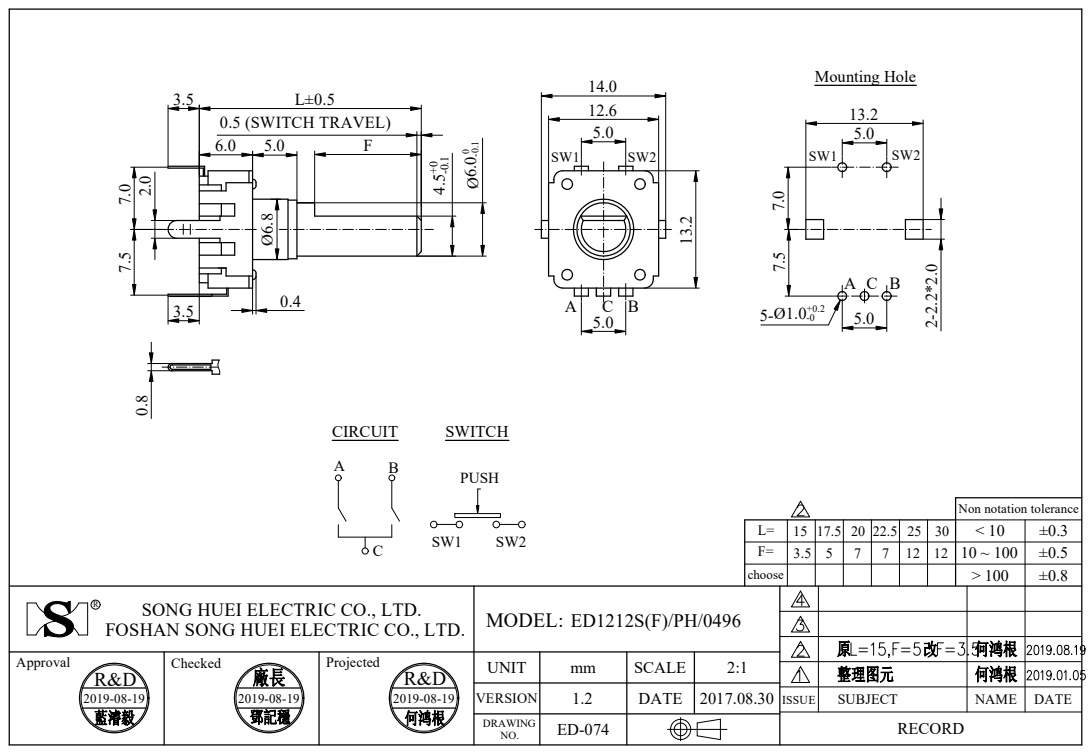
[picture p203: page 3]
2-2.2*2.0 14.0 A C B 0.5 (SWITCH TRAVEL) SW1 SW2

7.0 5-Ø1.0+0.2 -0 A C B 5.0 SW1 SW2 5.0 0.4 3.5 SW1 SW2 PUSH C A B Mounting Hole R&D R&D 2019-08-19 SONG HUEI ELECTRIC CO., LTD. FOSHAN SONG HUEI ELECTRIC CO., LTD. ±0.3 ±0.5 ±0.8 < 10 10 ~ 100 > 100 RECORD NAME DATE SCALE 2:1 DATE 2017.08.30 mm1.2 ED-074 ISSUE MODEL: Non notation tolerance Approval Checked Projected UNIT VERSION DRAWING NO. SUBJECT R CIRCUIT ED1212S(F)/PH/0496 SWITCH L=F= choose 20 22.5 25 30 7 12 12 17.5 3.5 7 15 5 2019-08-19 2019-08-19

軸型

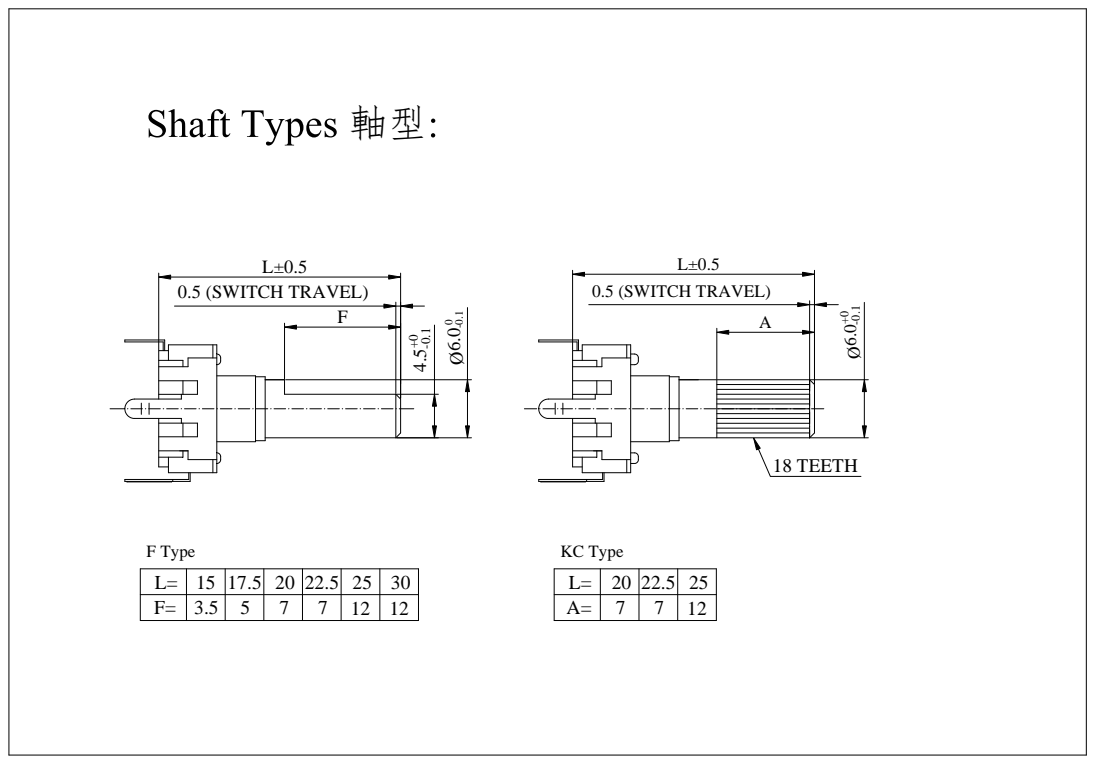
[picture p204: page 4]
0.5 (SWITCH TRAVEL); F Type; 18 TEETH; KC Type
