intechstudio/grid-hardware/Mechanical/Design/archive/reference_THT-POT.pdf

® 松 暉 電 機 工 業 股 份 有 限 公 司 S O N G H U E I E L E C T R I C C O . , L T D .

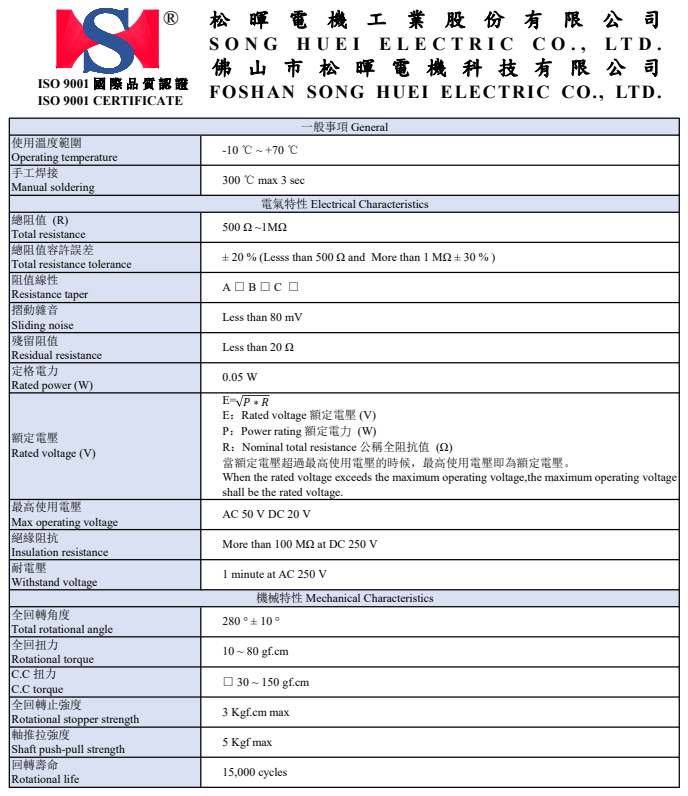
[picture p205: page 1]
一般事項 General; ISO 9001 國 際 品 質 認 證 ISO 9001 CERTIFICATE

FOSHAN SONG HUEI ELECTRIC CO., LTD.

使用溫度範圍 Operating temperature | -10 ℃ ~ +70 ℃

手工焊接 Manual soldering | 300 ℃ max 3 sec

電氣特性 Electrical Characteristics

總阻值 (R) Total resistance | 500 Ω ~1MΩ

總阻值容許誤差 Total resistance tolerance | ± 20 % (Lesss than 500 Ω and More than 1 MΩ ± 30 % )

阻值線性 Resistance taper | A □ B □ C □

摺動雜音 Sliding noise | Less than 80 mV

殘留阻值 Residual resistance | Less than 20 Ω

定格電力 Rated power (W) | 0.05 W

額定電壓 Rated voltage (V) | E= P ∗ R E：Rated voltage 額定電壓 (V) P：Power rating 額定電力 (W) R：Nominal total resistance 公稱全阻抗值 (Ω) 當額定電壓超過最高使用電壓的時候，最高使用電壓即為額定電壓。 When the rated voltage exceeds the maximum operating voltage,the maximum operating voltage shall be the rated voltage.

最高使用電壓 Max operating voltage | AC 50 V DC 20 V

絕緣阻抗 Insulation resistance | More than 100 MΩ at DC 250 V

耐電壓 Withstand voltage | 1 minute at AC 250 V

機械特性 Mechanical Characteristics

全回轉角度 Total rotational angle | 280 ° ± 10 °

全回扭力 Rotational torque | 10 ~ 80 gf.cm

C.C 扭力 C.C torque | □ 30 ~ 150 gf.cm

全回轉止強度 Rotational stopper strength | 3 Kgf.cm max

軸推拉強度 Shaft push-pull strength | 5 Kgf max

回轉壽命 Rotational life | 15,000 cycles

10.6

L±0.5

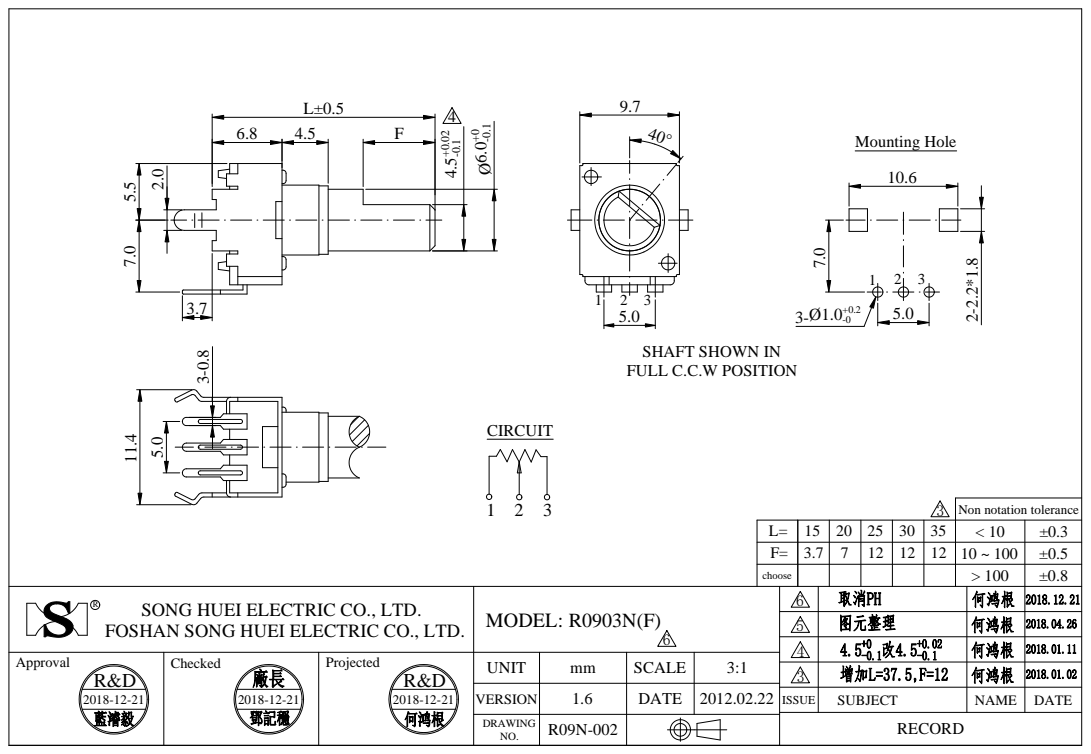
[picture p206: page 2]
CIRCUIT; Mounting Hole

SHAFT SHOWN IN
FULL C.C.W POSITION

Non notation tolerance

L= | 15 | 20 | 25 | 30 | 35 | < 10 | ±0.3
F= | 3.7 | 7 | 12 | 12 | 12 | 10 ~ 100 | ±0.5
choose | | | | | | > 100 | ±0.8

R0903N(F) SONG HUEI ELECTRIC CO., LTD. FOSHAN SONG HUEI ELECTRIC CO., LTD. MODEL: 6 | 6

ISSUE | SUBJECT | NAME | DATE

Approval R&D 2018-12-21 | Checked 2018-12-21 | Projected R&D 2018-12-21 | UNIT | mm | SCALE | 3:1

VERSION | 1.6 | DATE | 2012.02.22
DRAWING NO. | R09N-002 | | | | | RECORD

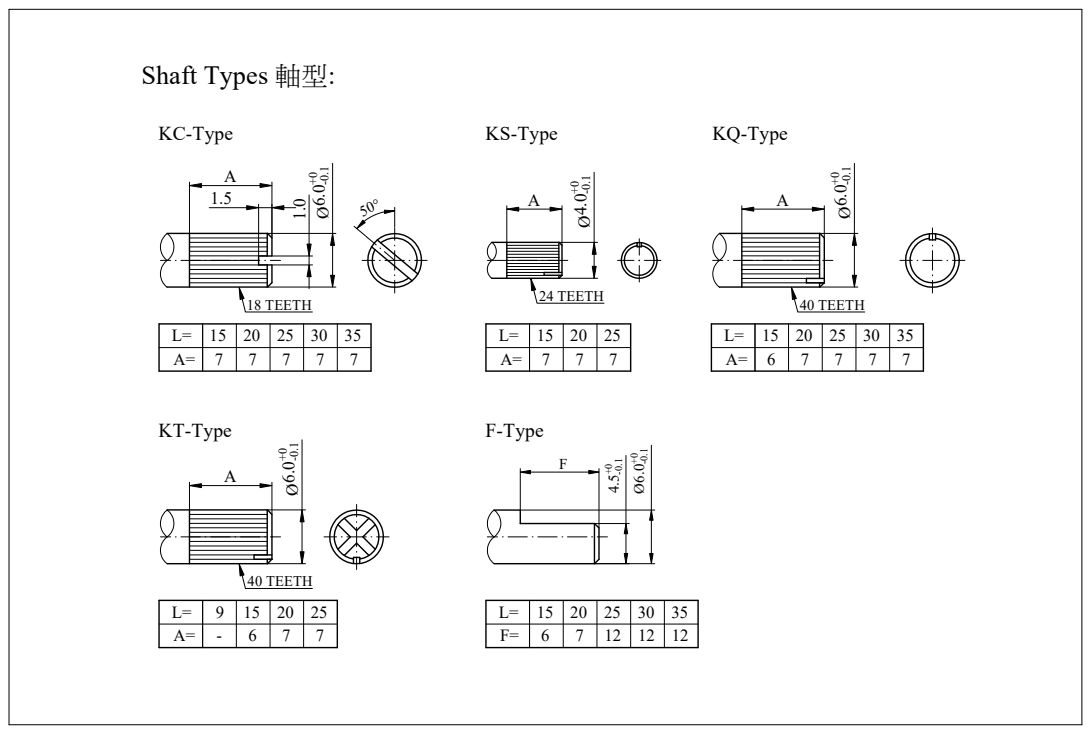
[picture p207: page 3]
-0.1 1.5 18 TEETH L= 20 25 30 A= 15 7 35 7 7 7 7 Ø4.0+0 -0.1 A L= 20 25 A= 15 7 7 7 24 TEETH Ø6.0+0; -0.1 A 40 TEETH L= 20 25 30 A= 15 7 35 6 7 7 7 50° Ø6.0+0

-0.1 A 40 TEETH L= 20 25 A= 15 6 7 7 9 - Shaft Types 軸型: KC-Type KQ-Type KT-Type KS-Type F-Type
