intechstudio/grid-hardware/Electrical/Experiments/# Legacy/InterfaceFFC/InterfaceFFC.PDF

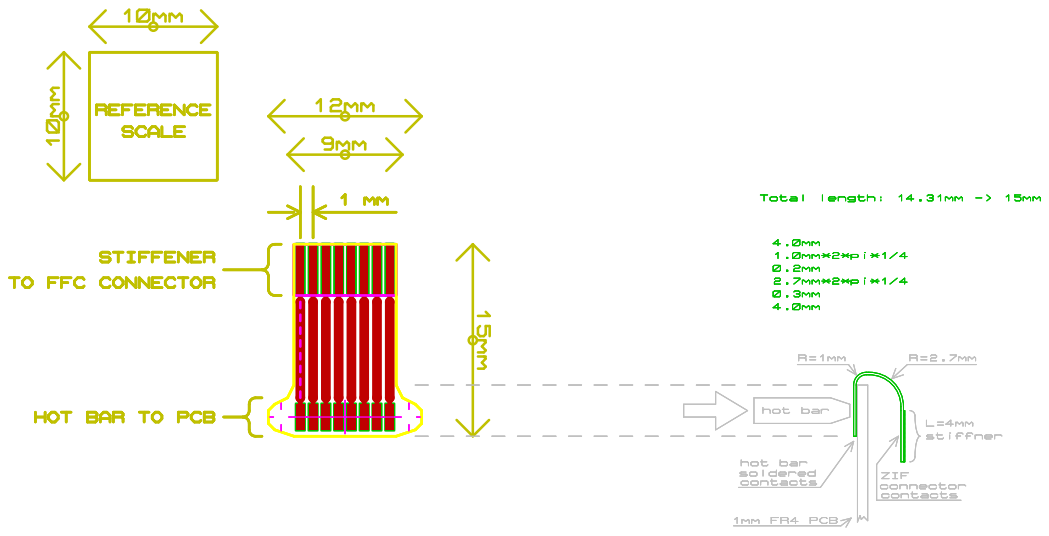
[picture p208: page 1]
